frankcohen/ReflectionsOS/Devices/Hoober/Hoober Avinidad Rework rev 2.pdf

July 10, 2022

Hi Ryan,

Here is a rework list for the remaining 4 Hoober Avinadad boards. Would you please make these reworks, then ship the boards to me at:

Frank Cohen
Bellingham Makerspace
1 Bellis
Fair Parkway #618,
Bellingham, WA 98225
Phone: (408) 364-5508

Thank you! -Frank

Rework #1
Hand-made wiring between TFT display module and pads. Pads are the wrong pitch.

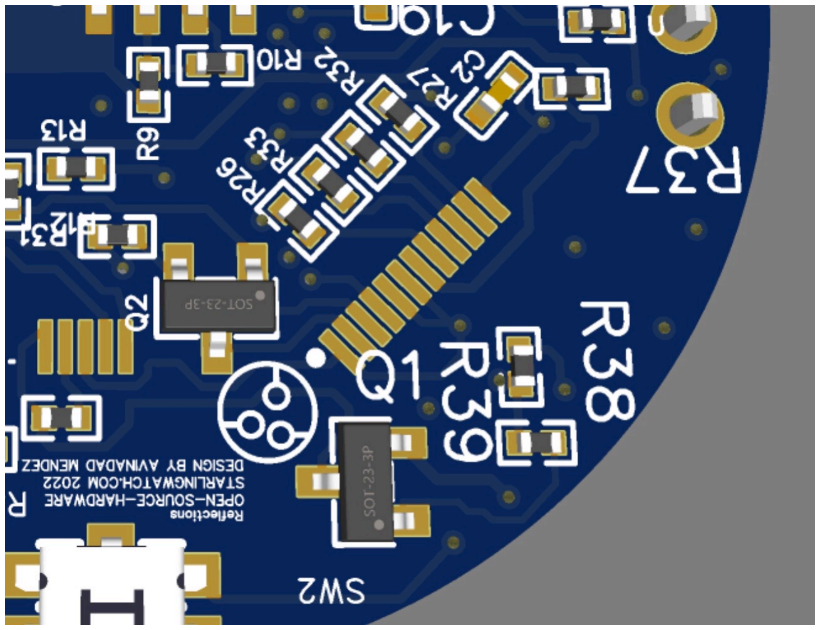
[picture p22: figure]
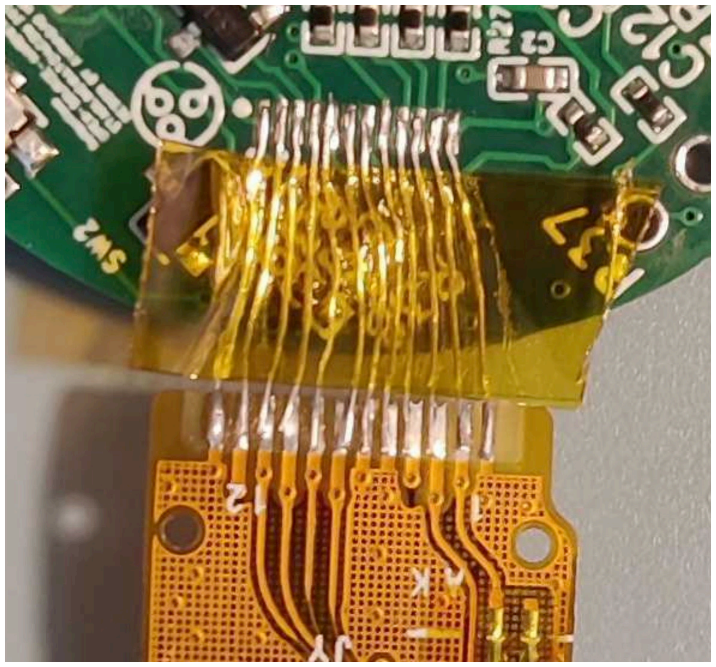
[picture p23: figure]

Make sure the display connector Pin 1 matches Pin 1 on the board.

Remove R26 from the board. There is no need to solder anything there.

Rework #2

Daughterboard welded to Main board using provided cable.

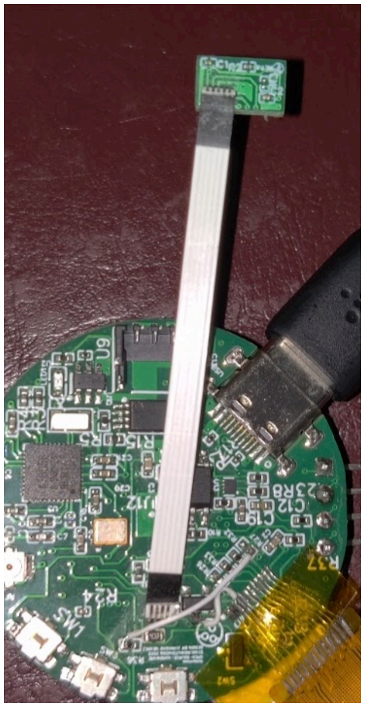
[picture p24: figure]

Rework #3

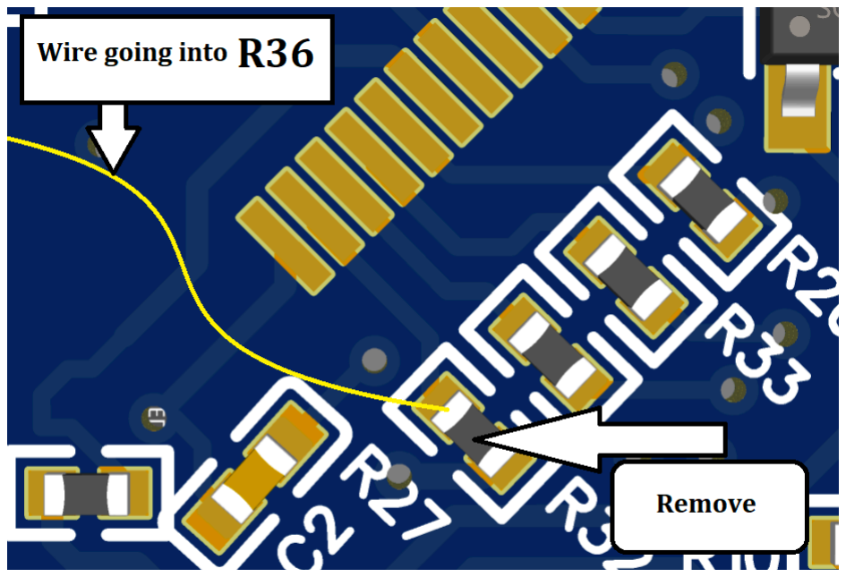
[picture p25: figure]
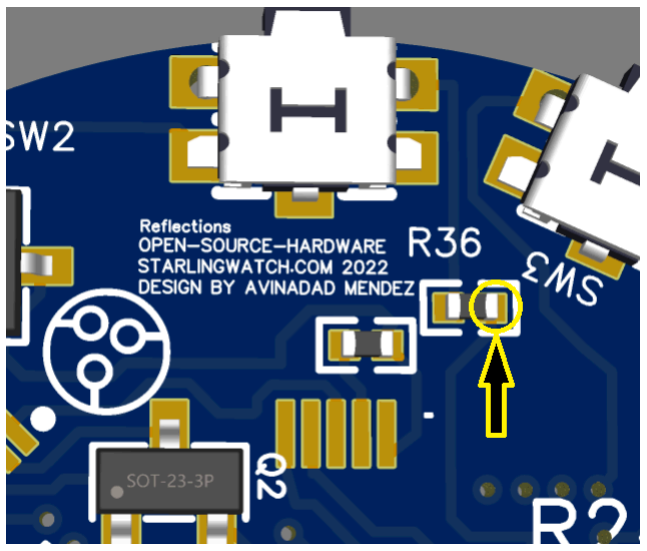
[picture p26: figure]
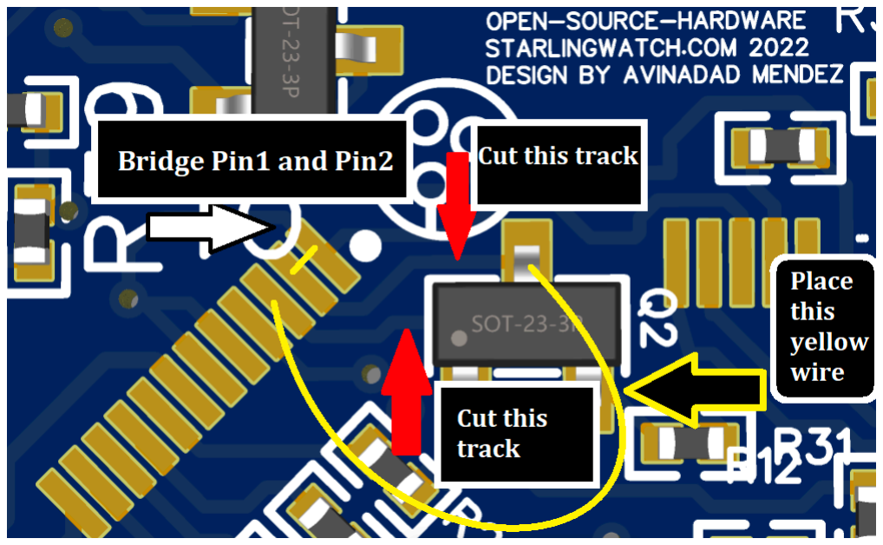
[picture p27: figure]

Rework #4

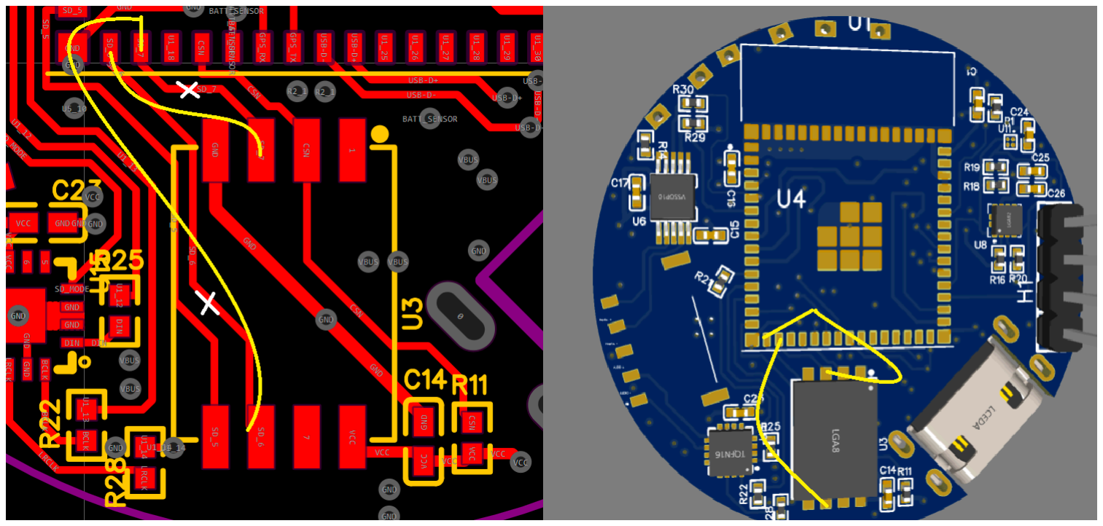
[picture p28: figure]

Cut SD_7 track.
Cut SD_6 track.
Solder SD_6 (ESP32) to SD_7 (NAND).
Solder SD_7 (ESP32) to SD_6 (NAND).
Remove R11
Cut pin 2 of the NAND (U3) from the trace/pad
Connect a wire to pin 2, the wire has a female Dupont connector

Rework #5
This is only for 2 of the remaining 4 boards.

Wire GPIO 8 of the AT6558R (U5) to Ground

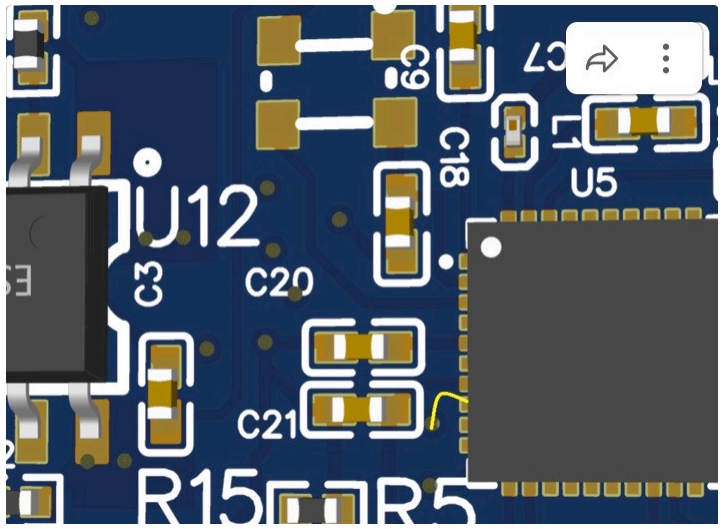
[picture p29: figure]
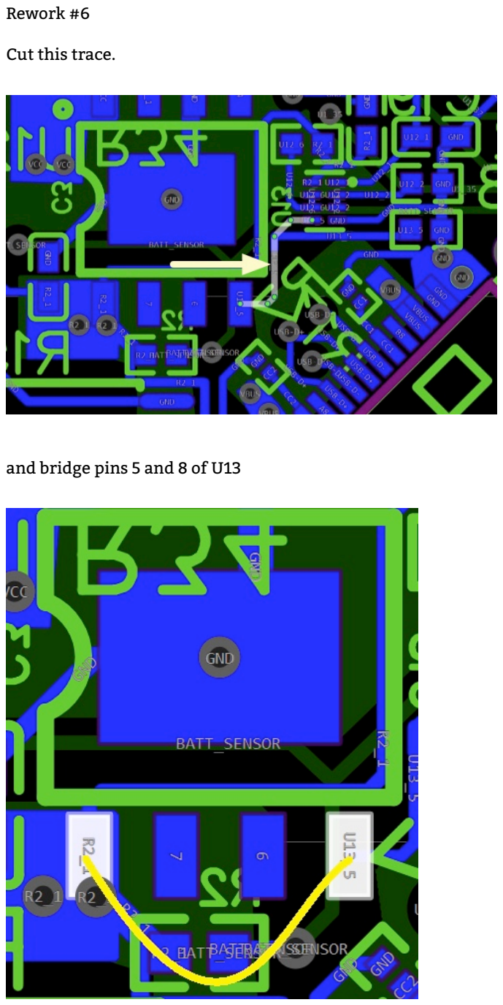
[picture p30: page 6]

Rework #6

Cut this trace.

and bridge pins 5 and 8 of U13
