frankcohen/ReflectionsOS/Devices/Hoober/Gesture Sensor Daughter Board.pdf

# Gesture Sensor Board

# VL53L5CX Sensor daughter board with FFC 4 wire cable

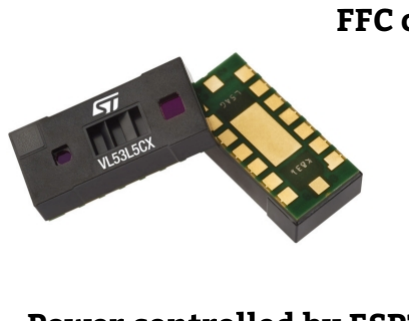
[picture p31: figure]

FFC connector welded to daughter board, adds FFC connector to main board

VL53L5CX

Power controlled by ESP32 GPIO pin

FFC 4 wire cable welded to the daughter board bottom Board is: 8mm x 4.67 mm, 1.57 mm
Sensor is: 6.4 mm x 3 mm x 1.5 mm
FFC wire: 5 mm x 20 mm x .24 mm
SMT mounted sensor pointing upwards

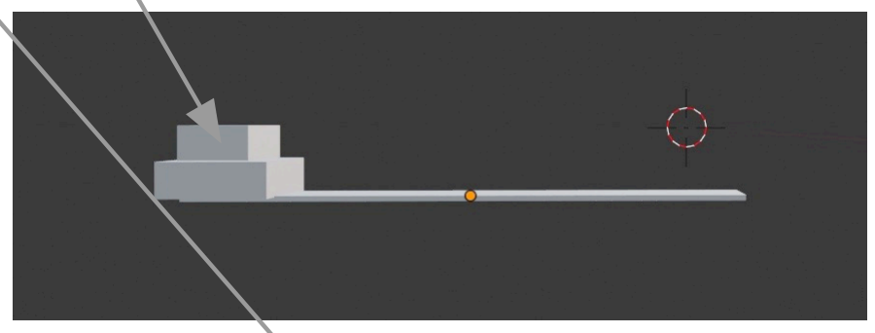
[picture p32: figure]
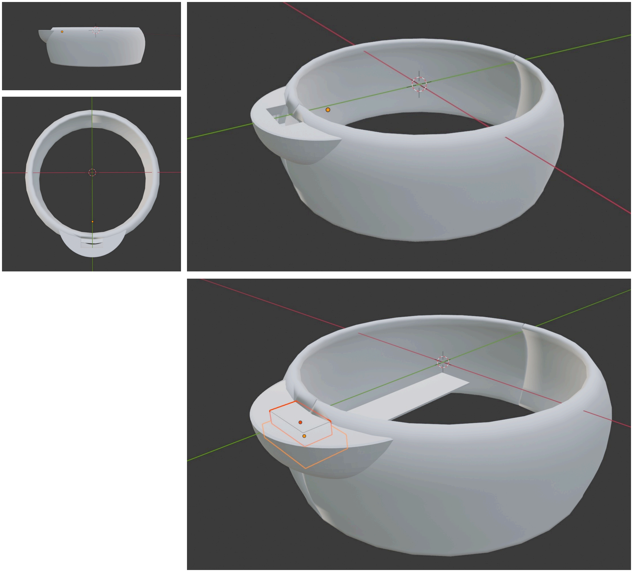
[picture p33: figure]
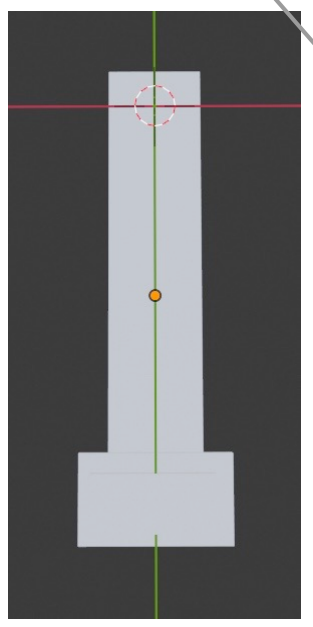
[picture p34: figure]
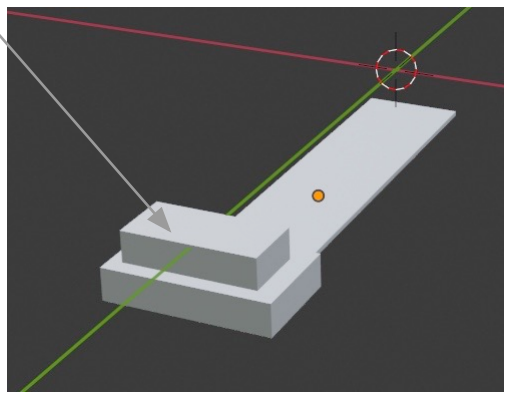
[picture p35: figure]
