frankcohen/ReflectionsOS/Devices/VladPlus/layouts/BoardOutLine.pdf

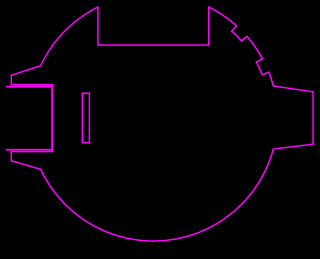
[picture p49: figure]
