frankcohen/ReflectionsOS/Devices/BlueFish/Datasheets/adafruit_products_FESP3_sch.png

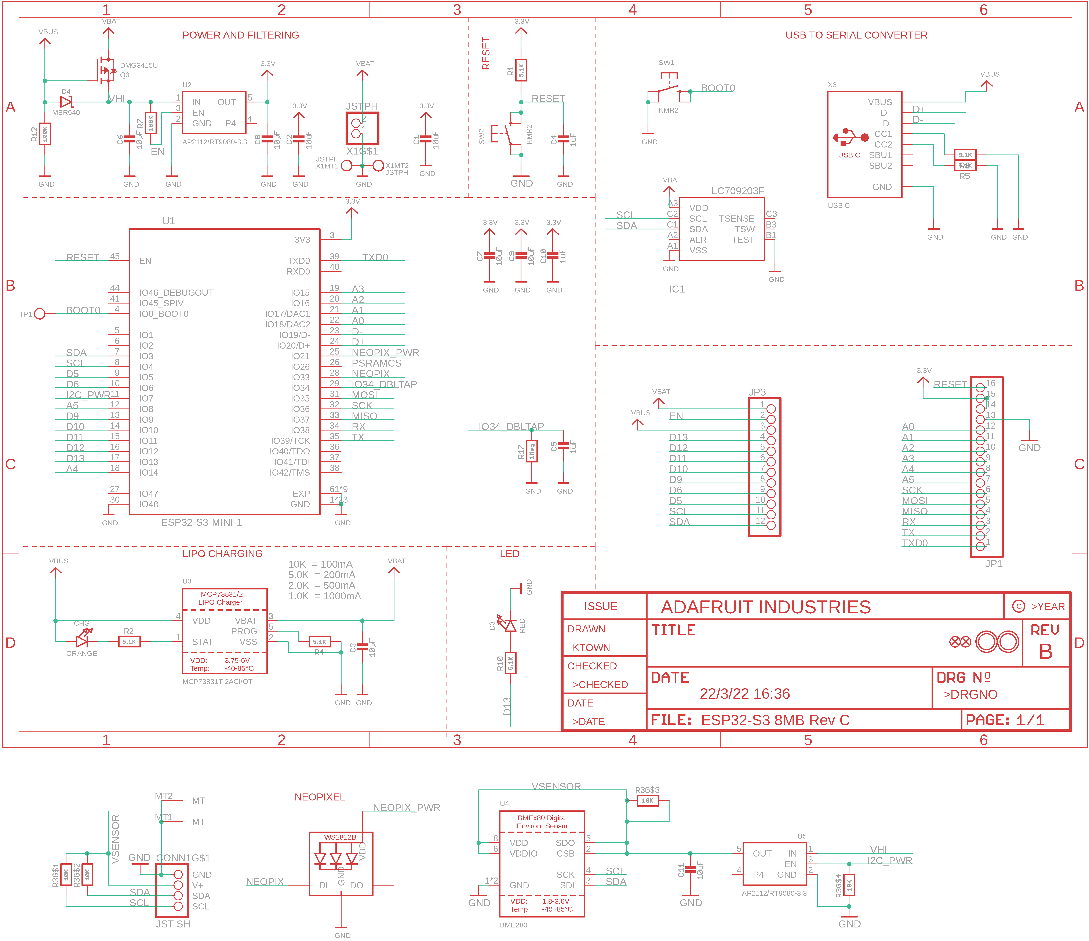
Devices/BlueFish/Datasheets/adafruit_products_FESP3_sch.png
