frankcohen/ReflectionsOS/Devices/CindyLou/CindyLou_daughter_board_stiffener.jpg

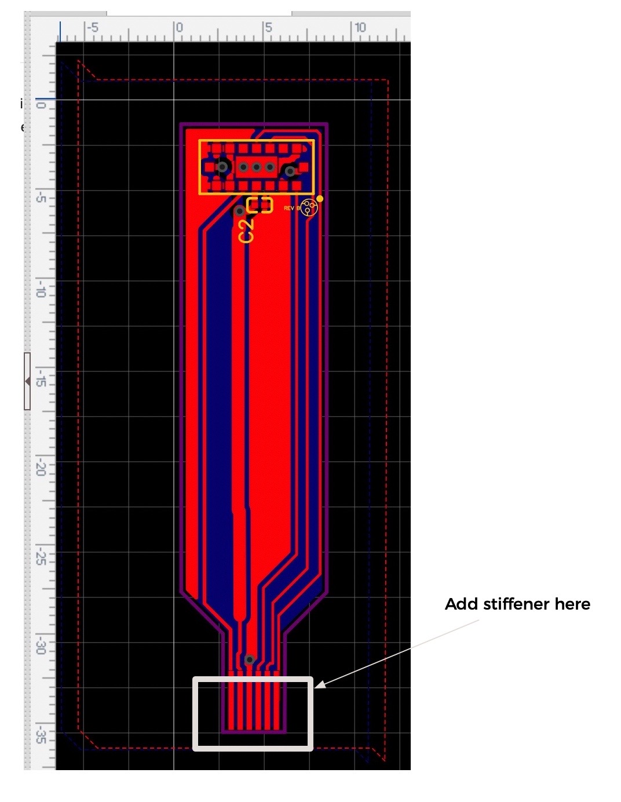
Devices/CindyLou/CindyLou_daughter_board_stiffener.jpg
