frankcohen/ReflectionsOS/Devices/CindyLou/Details daughter board.jpg

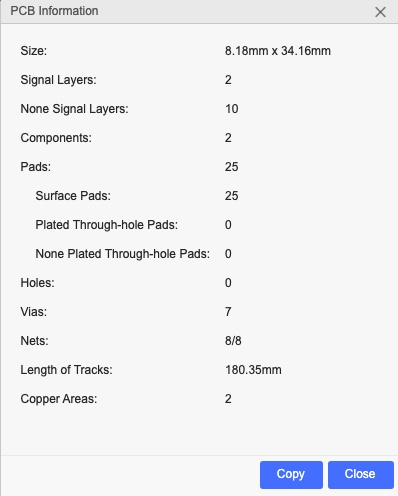
Devices/CindyLou/Details daughter board.jpg
