frankcohen/ReflectionsOS/Devices/CindyLou/Details main board.jpg

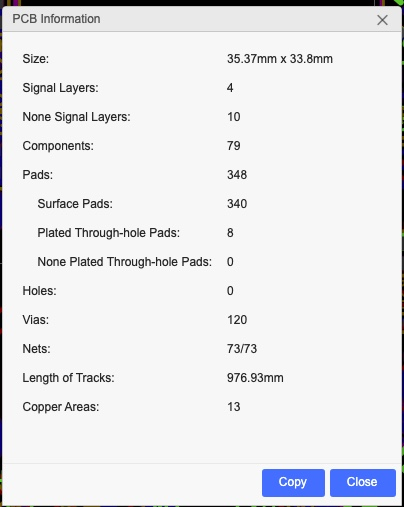
Devices/CindyLou/Details main board.jpg
