frankcohen/ReflectionsOS/Devices/CindyLou/PCBway photos/61b101b553f684890c5e4af1a7ff25e.jpeg

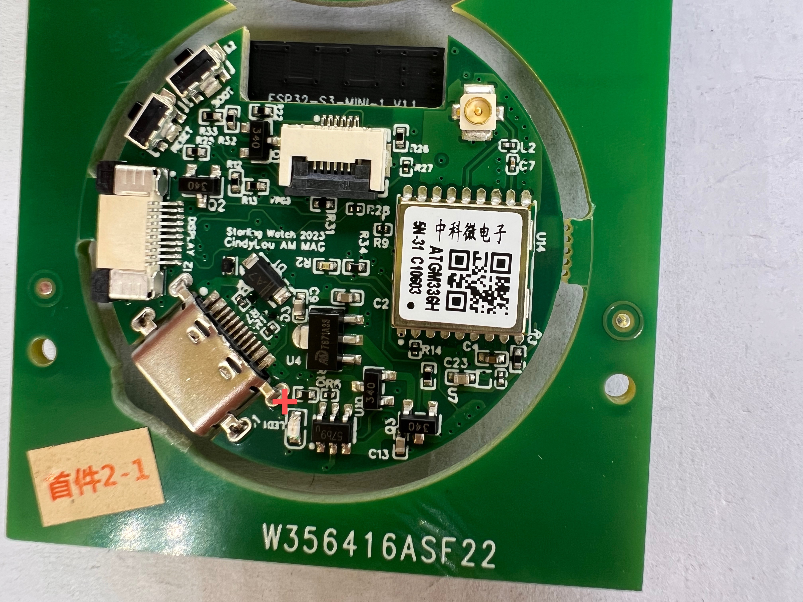
Devices/CindyLou/PCBway photos/61b101b553f684890c5e4af1a7ff25e.jpeg
