frankcohen/ReflectionsOS/Devices/Hoober/Photos/IMG_20220601_134554.jpg

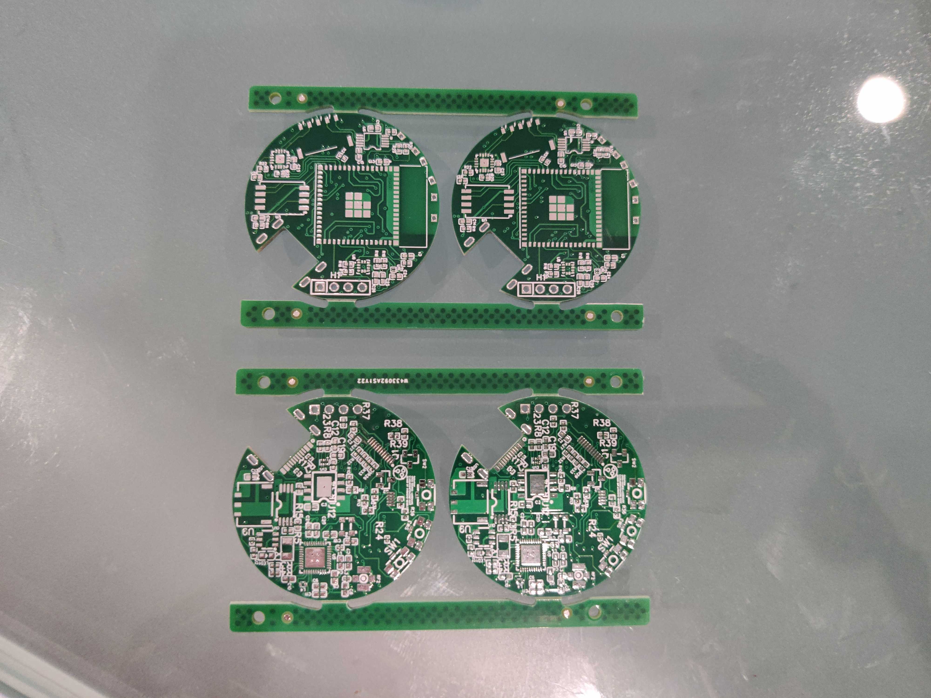
Devices/Hoober/Photos/IMG_20220601_134554.jpg
