frankcohen/ReflectionsOS/Devices/Hoober/Photos/IMG_20220627_172540.jpg

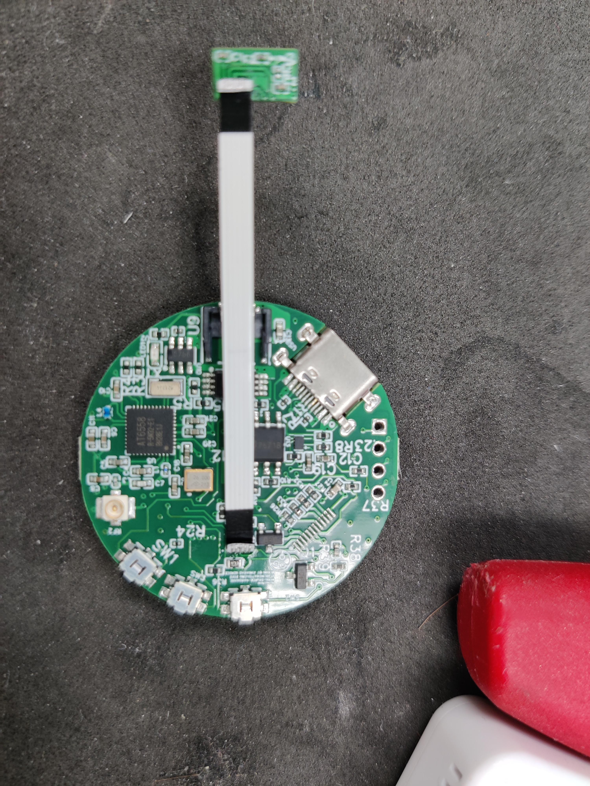
Devices/Hoober/Photos/IMG_20220627_172540.jpg
