frankcohen/ReflectionsOS/Devices/Hoober/Photos/IMG_20220627_172551.jpg

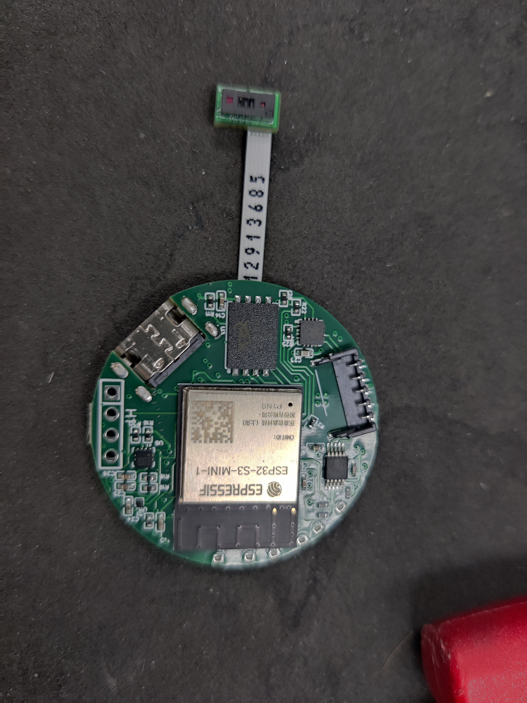
Devices/Hoober/Photos/IMG_20220627_172551.jpg
