frankcohen/ReflectionsOS/Devices/Hoober/Photos/IMG_20220627_183308.jpg

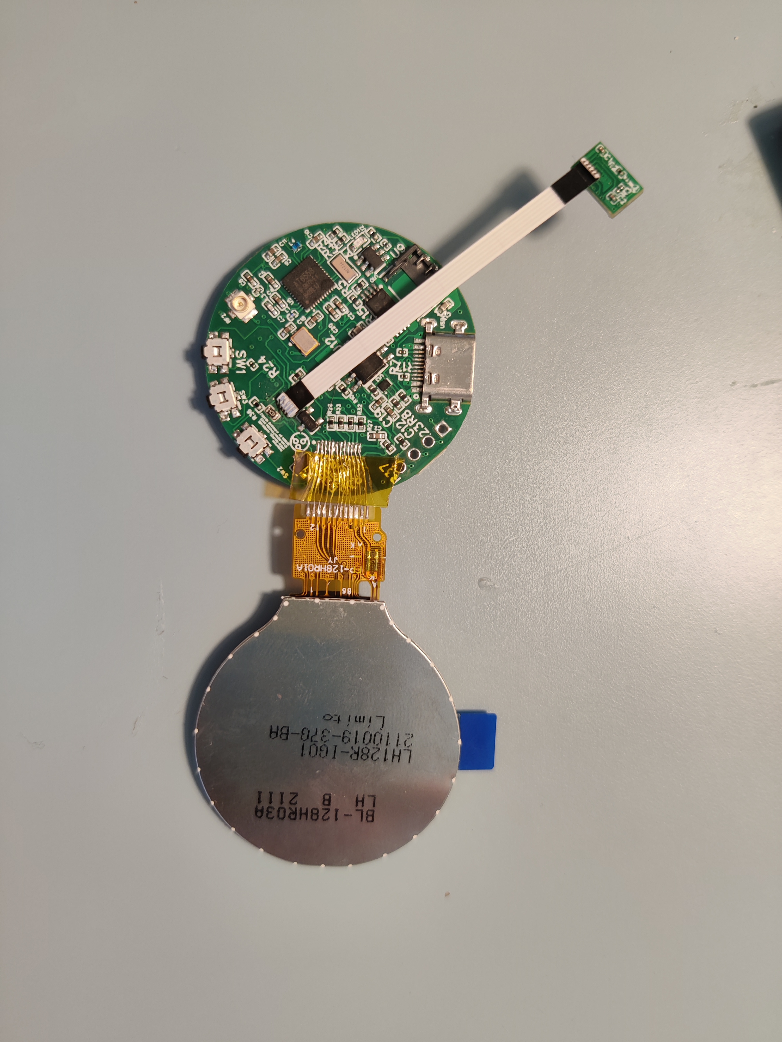
Devices/Hoober/Photos/IMG_20220627_183308.jpg
