frankcohen/ReflectionsOS/Devices/Hoober/Photos/IMG_20220627_183316.jpg

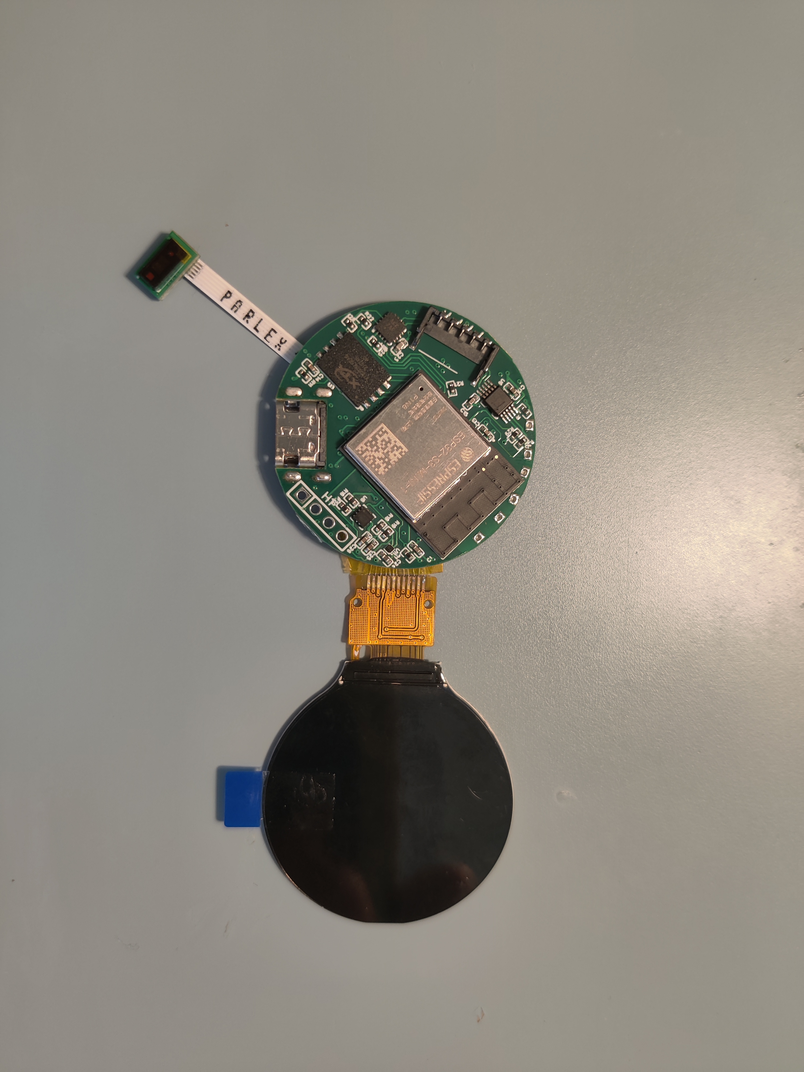
Devices/Hoober/Photos/IMG_20220627_183316.jpg
