frankcohen/ReflectionsOS/Devices/Hoober/Photos/IMG_20220707_080942.jpg

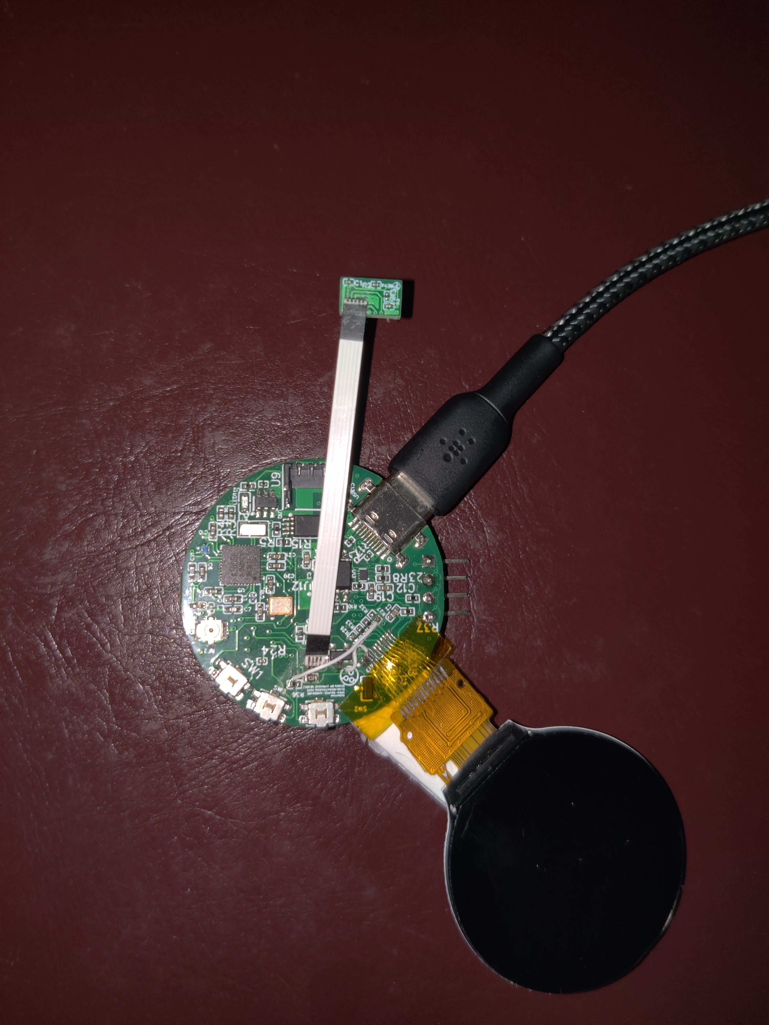
Devices/Hoober/Photos/IMG_20220707_080942.jpg
