frankcohen/ReflectionsOS/Devices/Hoober/Photos/IMG_20220710_211812.jpg

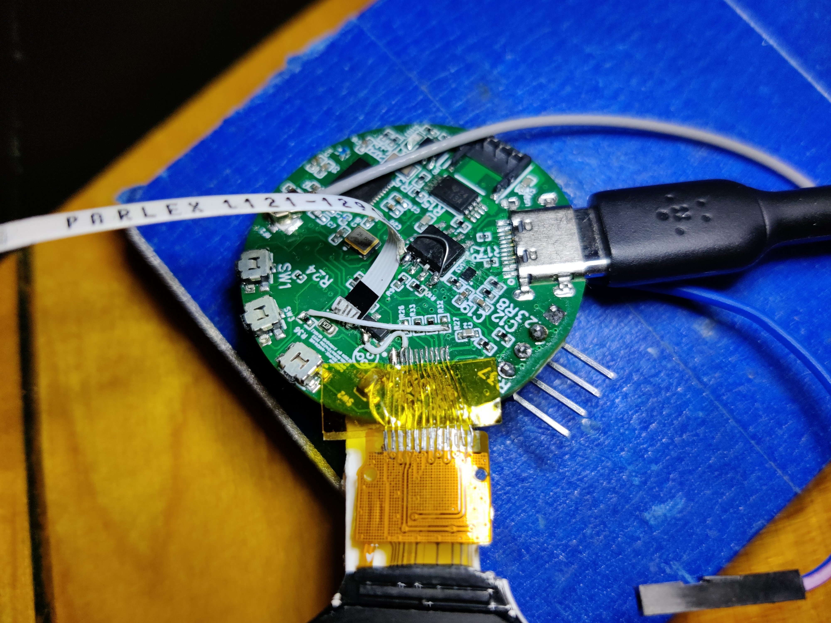
Devices/Hoober/Photos/IMG_20220710_211812.jpg
