frankcohen/ReflectionsOS/Devices/Hoober/Photos/screenshot_7177.jpg

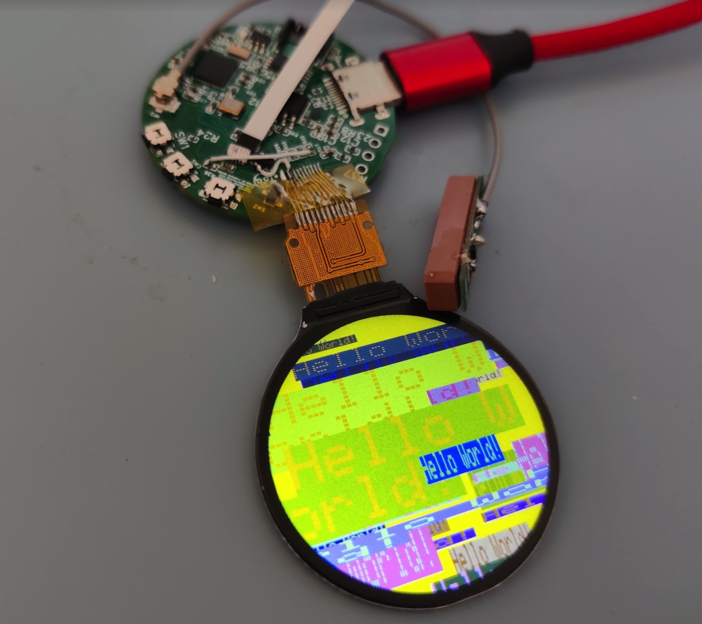
Devices/Hoober/Photos/screenshot_7177.jpg
