frankcohen/ReflectionsOS/Devices/Horton/Datasheets/Belinda FPC adaptor 3f5895c3af74f1fa5b2311e33c003cb9.jpg

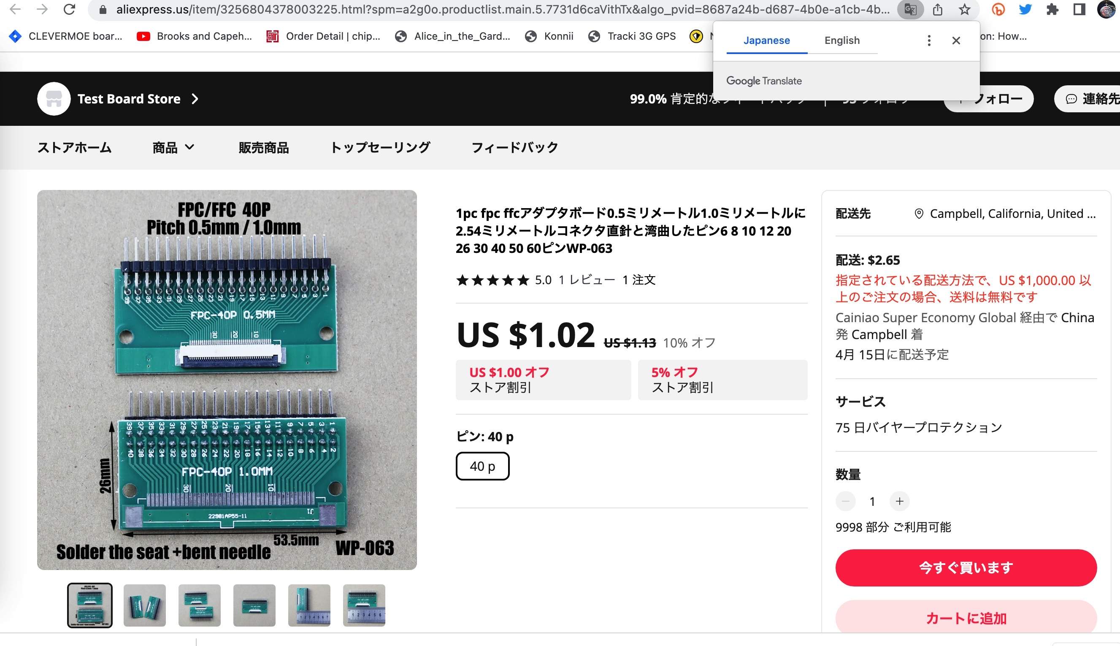
Devices/Horton/Datasheets/Belinda FPC adaptor 3f5895c3af74f1fa5b2311e33c003cb9.jpg
