frankcohen/ReflectionsOS/Devices/Knox/Breadboard Photos/IMG_20220116_211522.jpg

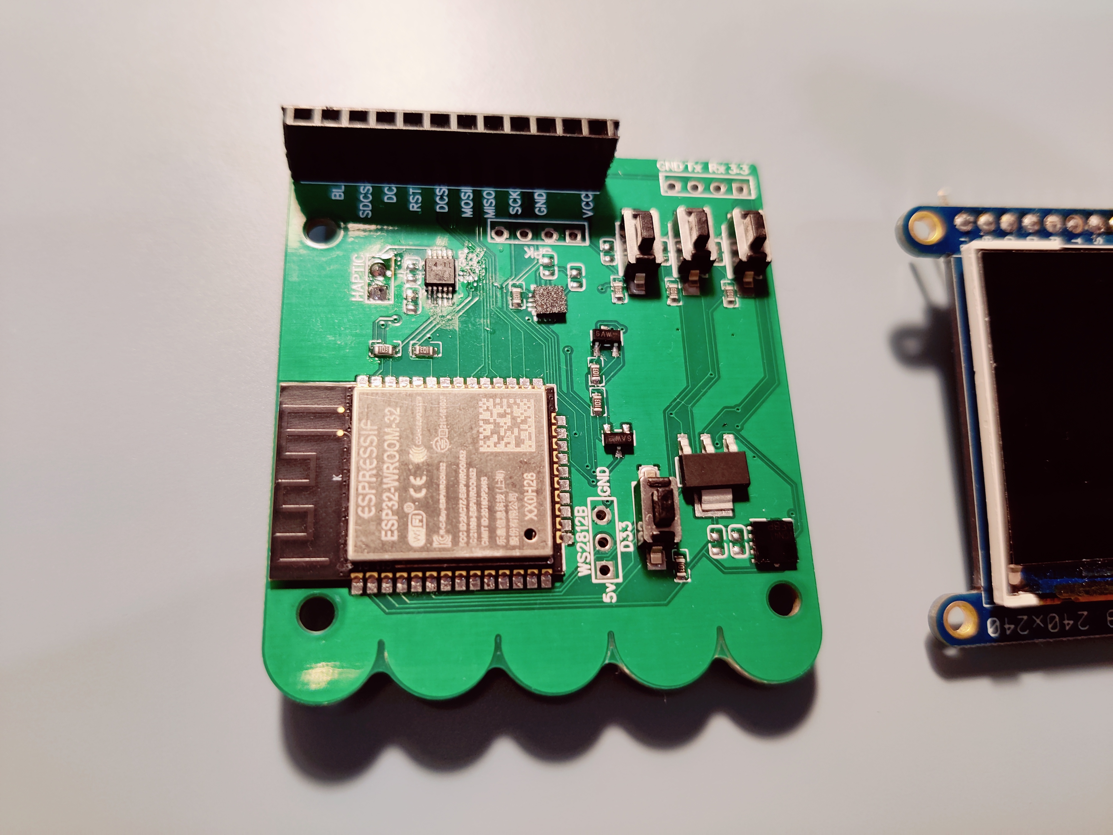
Devices/Knox/Breadboard Photos/IMG_20220116_211522.jpg
