frankcohen/ReflectionsOS/Devices/Knox/Breadboard Photos/IMG_20220116_211529.jpg

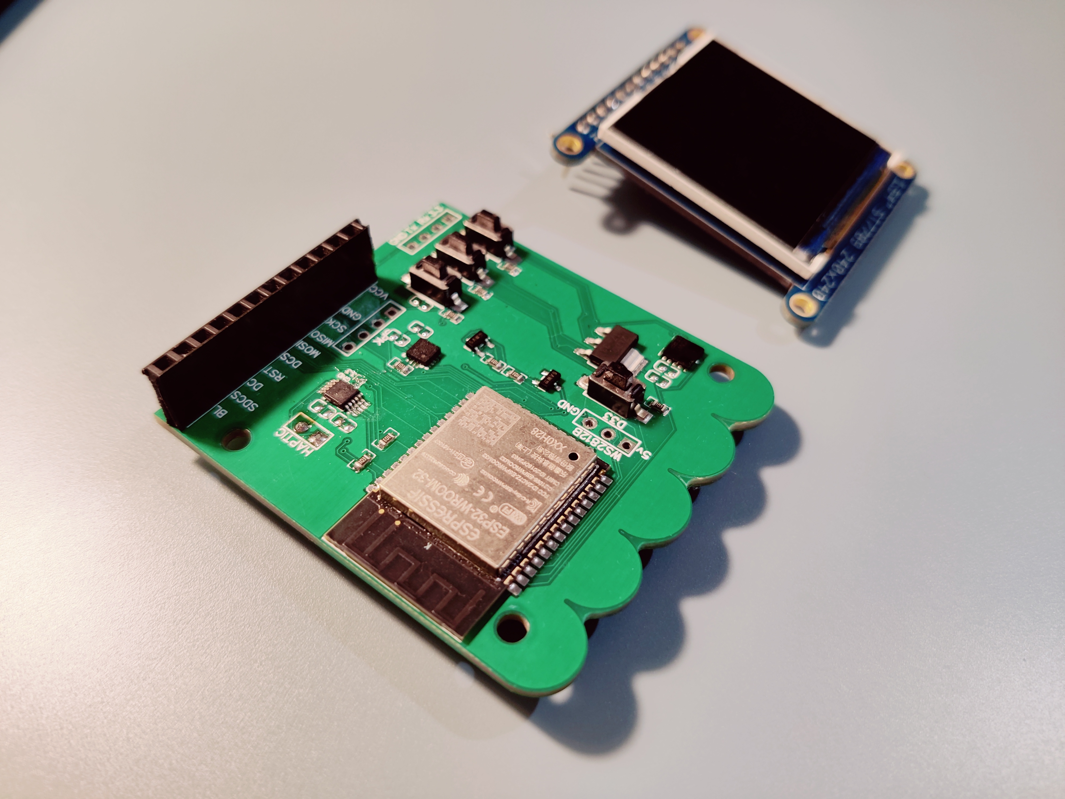
Devices/Knox/Breadboard Photos/IMG_20220116_211529.jpg
