frankcohen/ReflectionsOS/Devices/Knox/Breadboard Photos/IMG_20220116_211533.jpg

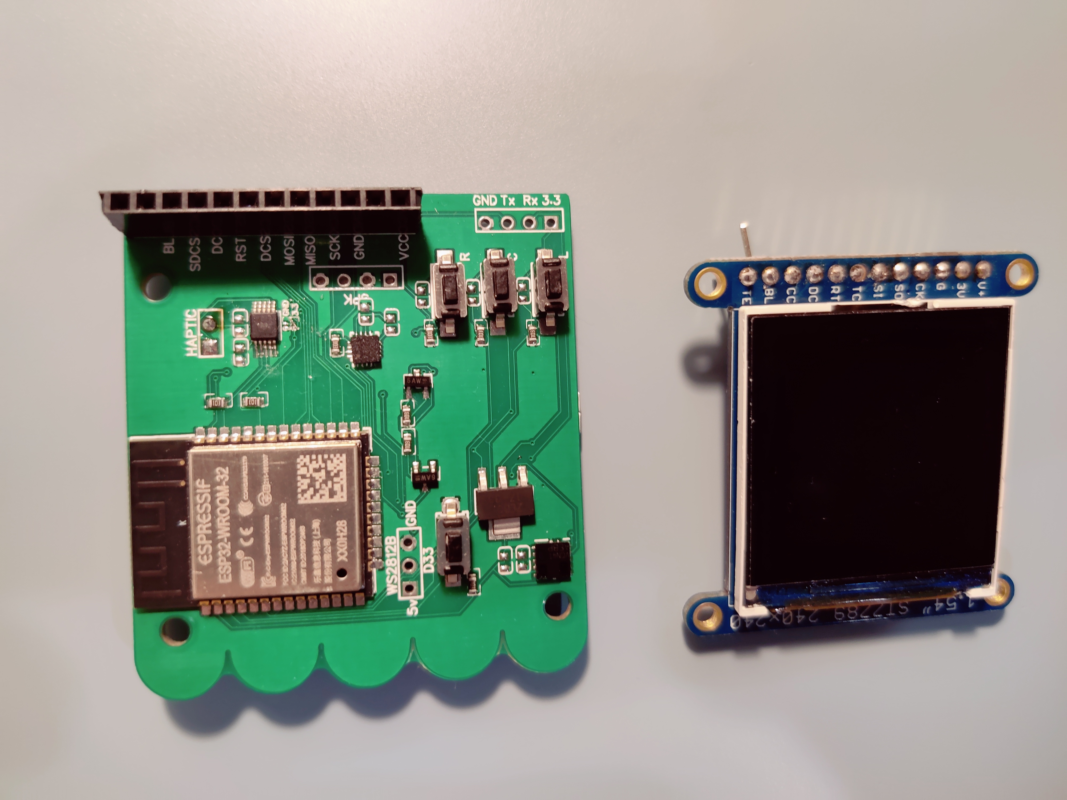
Devices/Knox/Breadboard Photos/IMG_20220116_211533.jpg
