frankcohen/ReflectionsOS/Devices/RedFish/T-F39W356416A/Check whether the orientation is correct.png

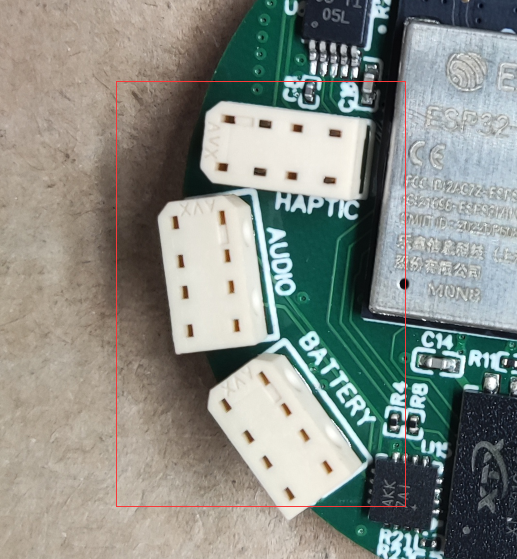
Devices/RedFish/T-F39W356416A/Check whether the orientation is correct.png
