frankcohen/ReflectionsOS/Devices/RedFish/T-F39W356416A/D3ĢŽD4 Check whether the orientation is correct.png

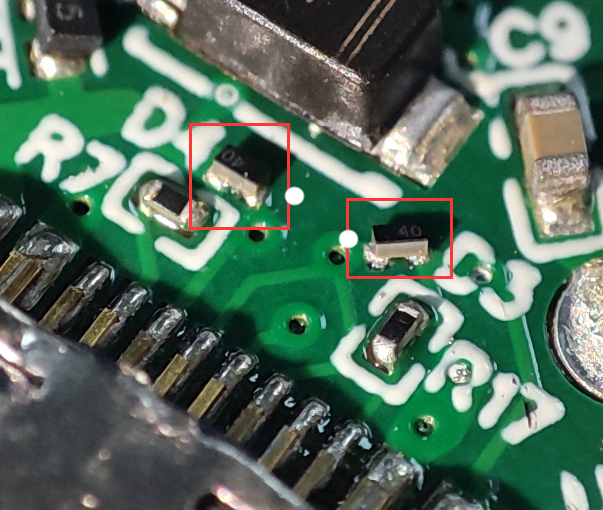
Devices/RedFish/T-F39W356416A/D3ĢŽD4 Check whether the orientation is correct.png
