frankcohen/ReflectionsOS/Devices/RedFish/T-F39W356416A/T-F39W356416A-QQ截图20230922172746.png

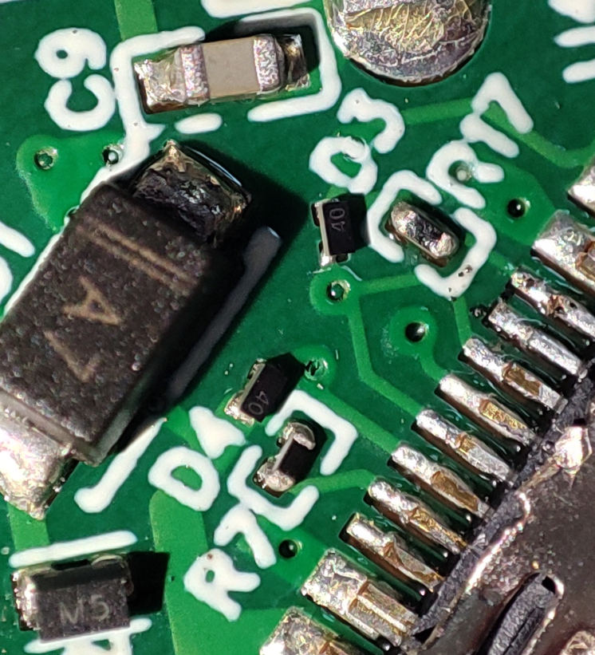
Devices/RedFish/T-F39W356416A/T-F39W356416A-QQ截图20230922172746.png
