frankcohen/ReflectionsOS/Devices/Sox/Breadboard Photos/Soxv1Breadboard/IMG_20220116_210145.jpg

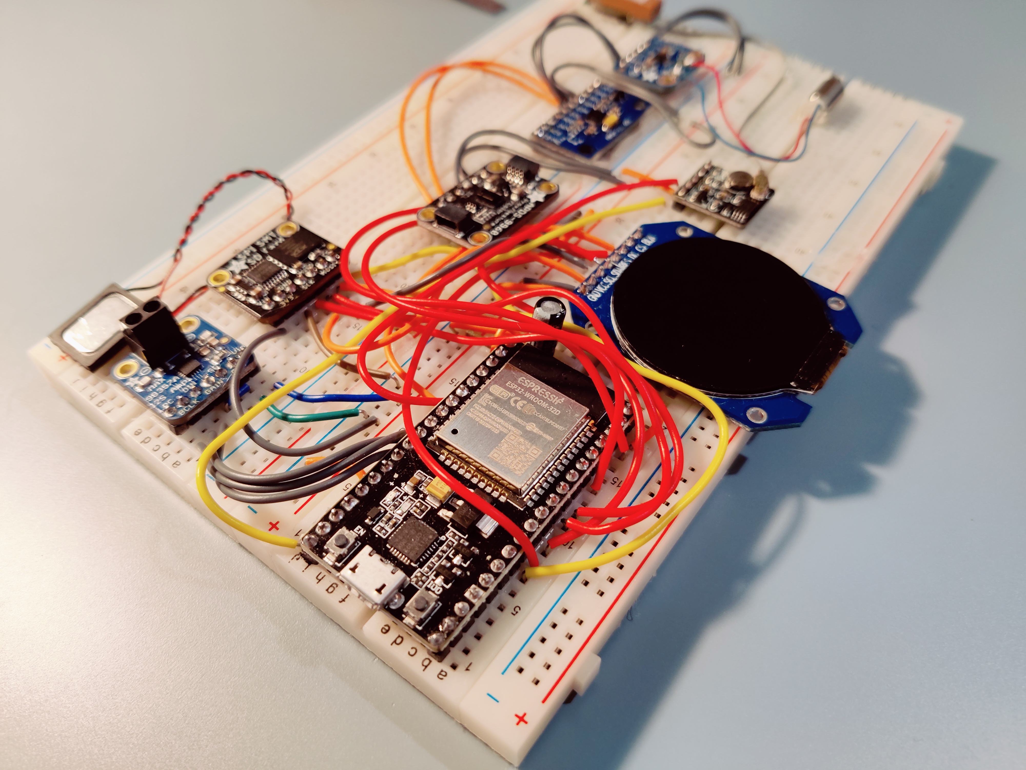
Devices/Sox/Breadboard Photos/Soxv1Breadboard/IMG_20220116_210145.jpg
