frankcohen/ReflectionsOS/Devices/Sox/Breadboard Photos/Soxv1Breadboard/IMG_20220116_210226.jpg

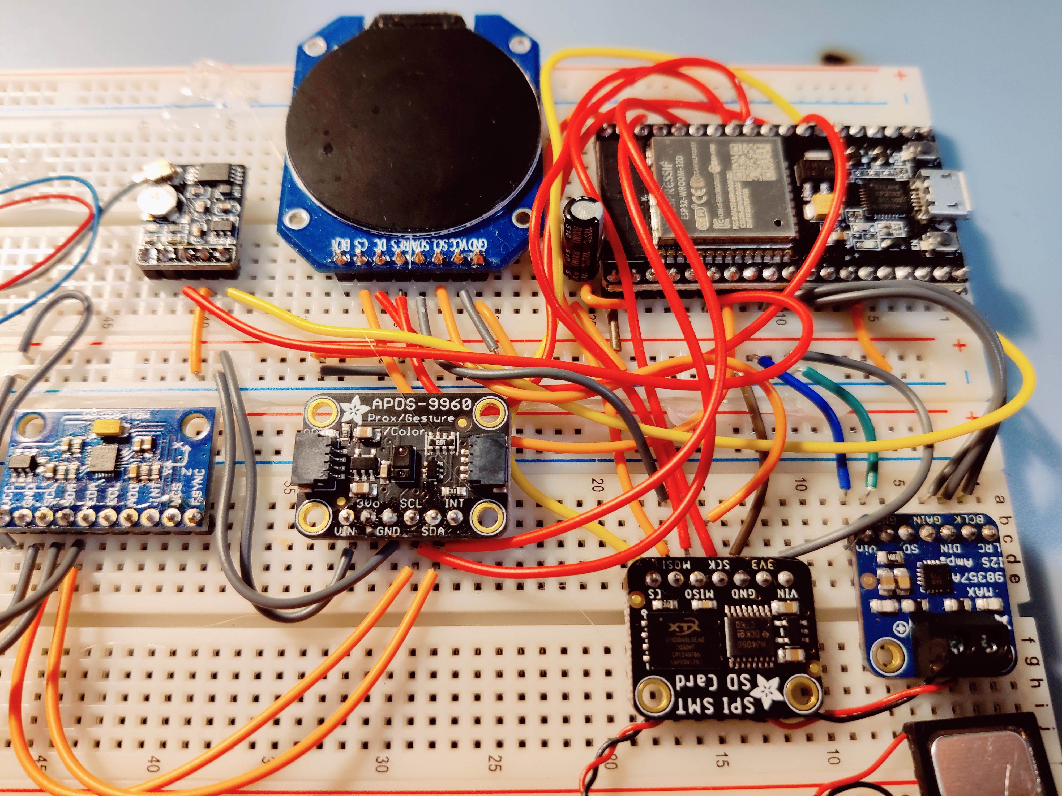
Devices/Sox/Breadboard Photos/Soxv1Breadboard/IMG_20220116_210226.jpg
