frankcohen/ReflectionsOS/Devices/Sox/Breadboard Photos/Soxv2Breadboard/IMG_20220124_091618.jpg

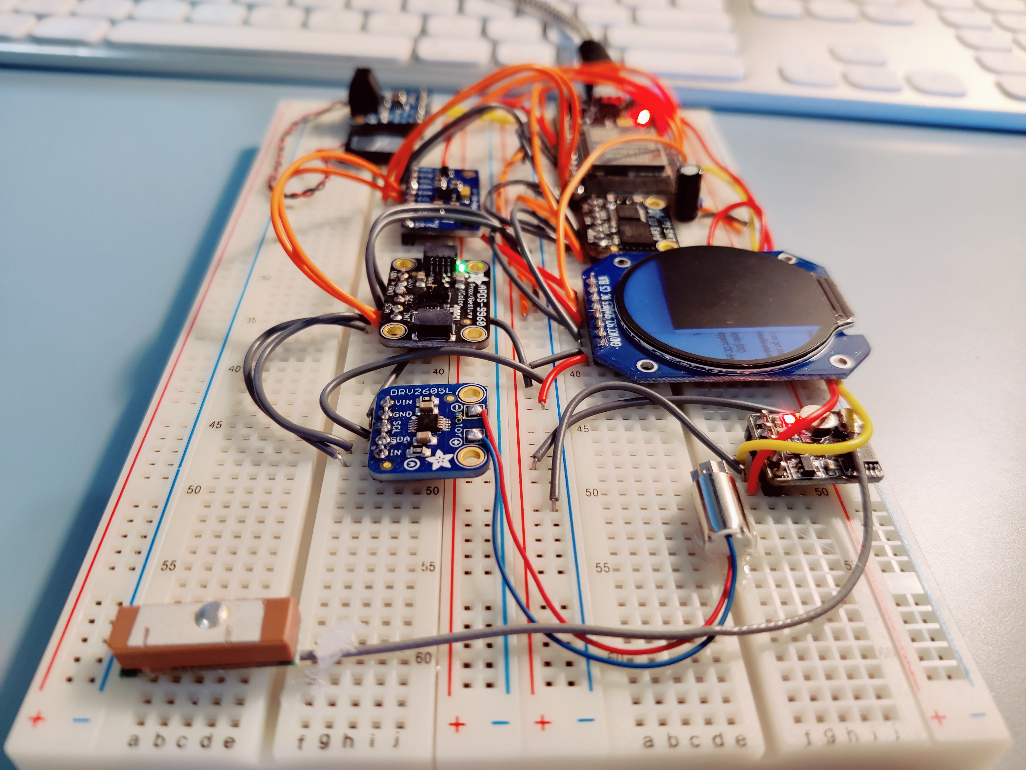
Devices/Sox/Breadboard Photos/Soxv2Breadboard/IMG_20220124_091618.jpg
