frankcohen/ReflectionsOS/Devices/Sox/Data Sheets/Haptic controller.jpeg

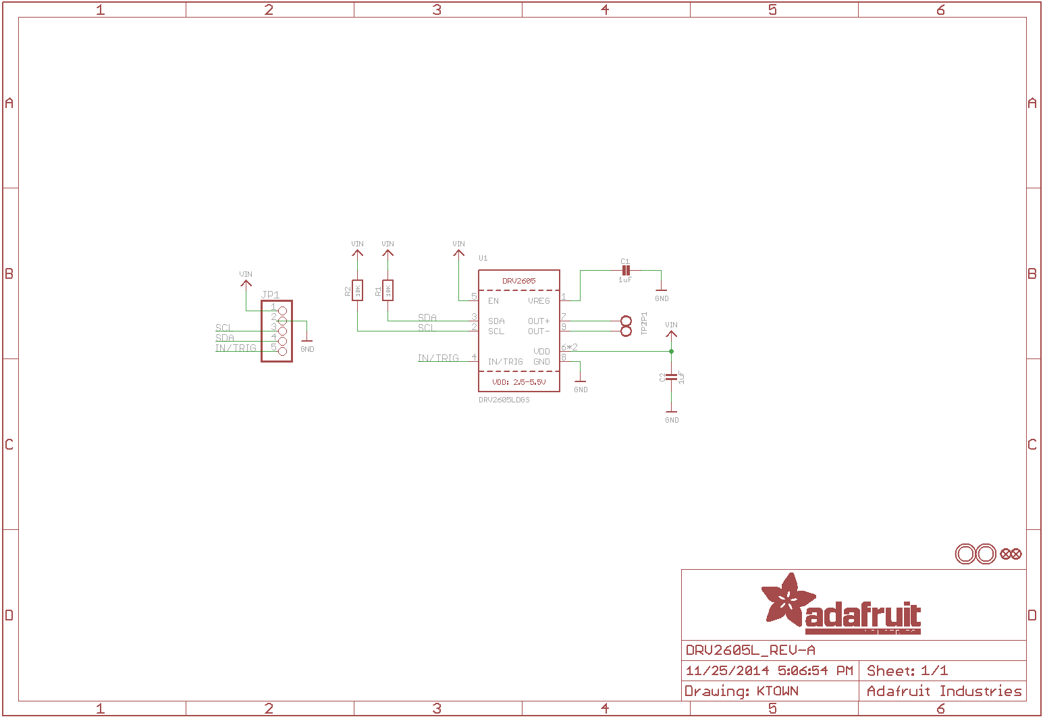
Devices/Sox/Data Sheets/Haptic controller.jpeg
