frankcohen/ReflectionsOS/Devices/Sox/Schematic/PCBway/Gerber_PCB_Sox Board Avinadad_2/阻抗线.png

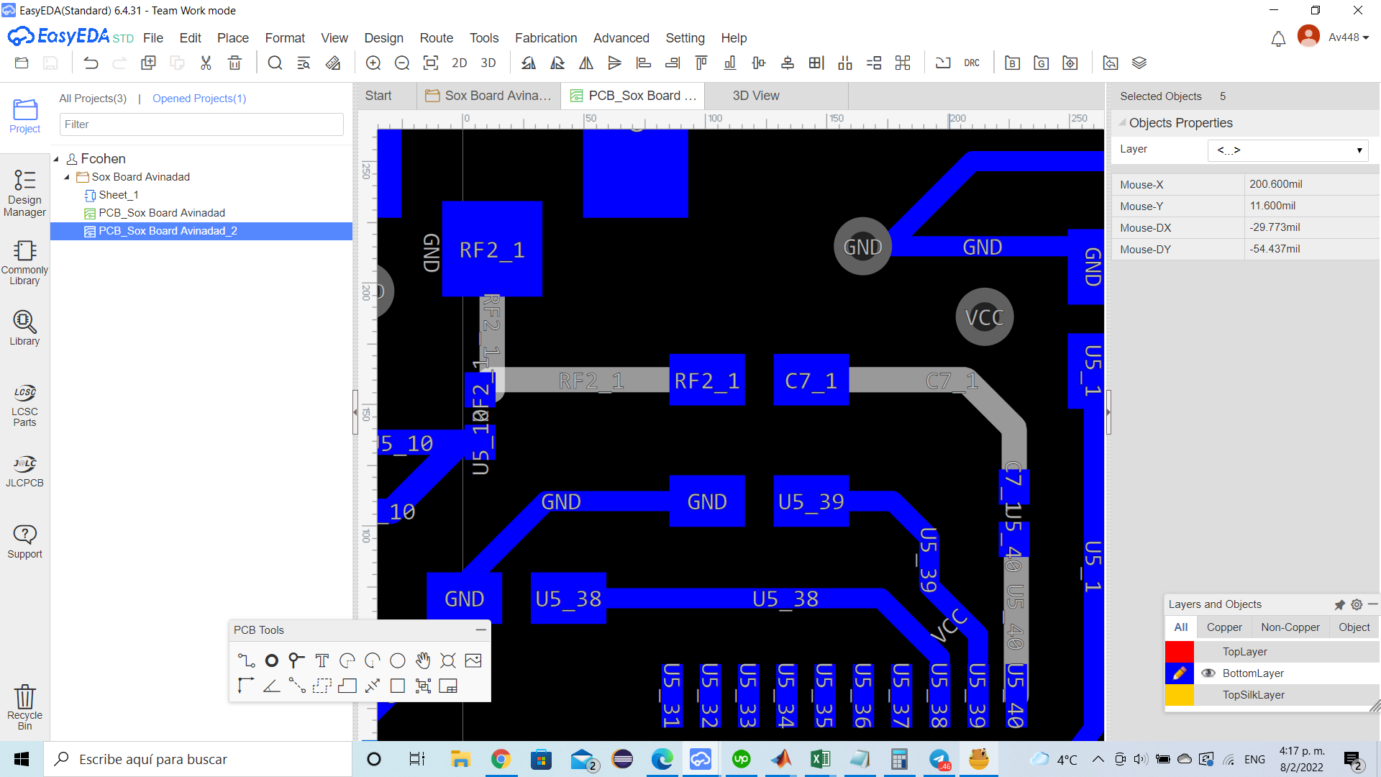
Devices/Sox/Schematic/PCBway/Gerber_PCB_Sox Board Avinadad_2/阻抗线.png
