frankcohen/ReflectionsOS/Devices/Vlad/XRays it is a board/1.jpg

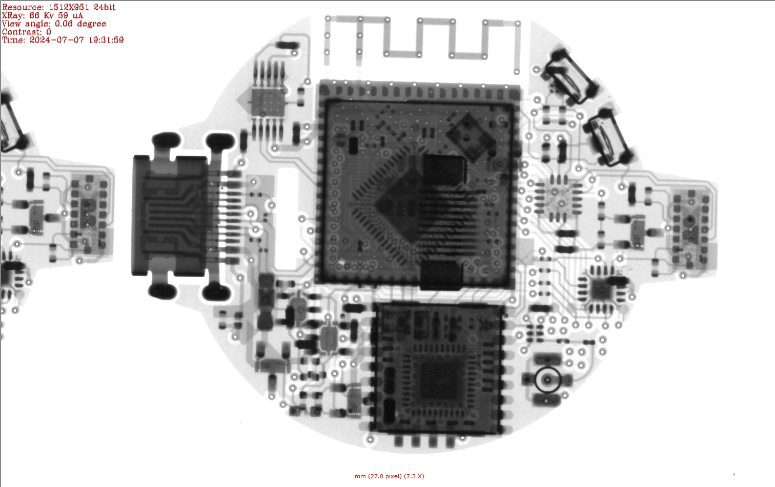
Devices/Vlad/XRays it is a board/1.jpg
