frankcohen/ReflectionsOS/Devices/Vlad/XRays it is a board/2.jpg

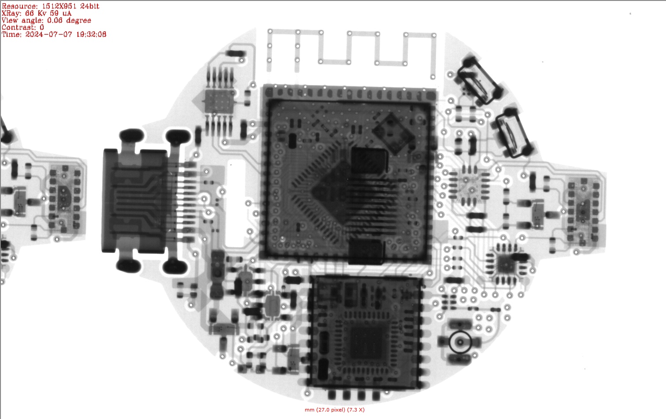
Devices/Vlad/XRays it is a board/2.jpg
