frankcohen/ReflectionsOS/Devices/Vlad/XRays it is a board/3.jpg

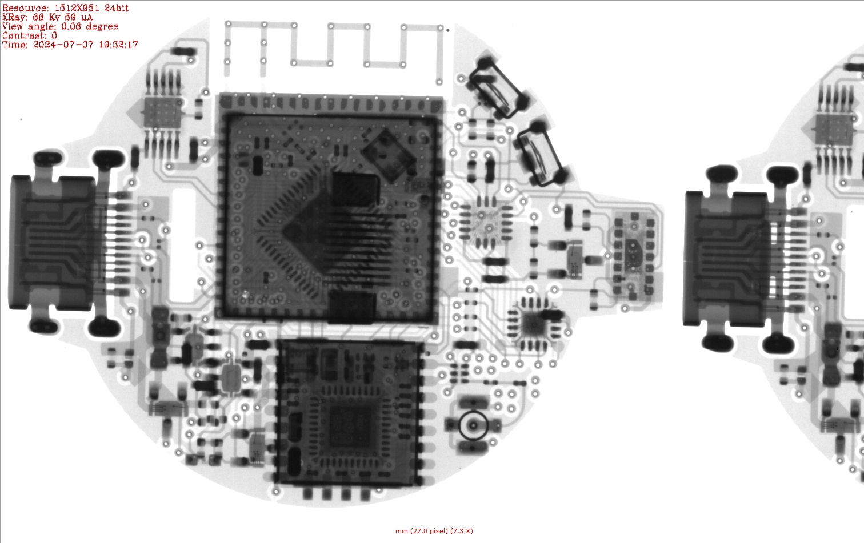
Devices/Vlad/XRays it is a board/3.jpg
