frankcohen/ReflectionsOS/Devices/Vlad/XRays it is a board/4.jpg

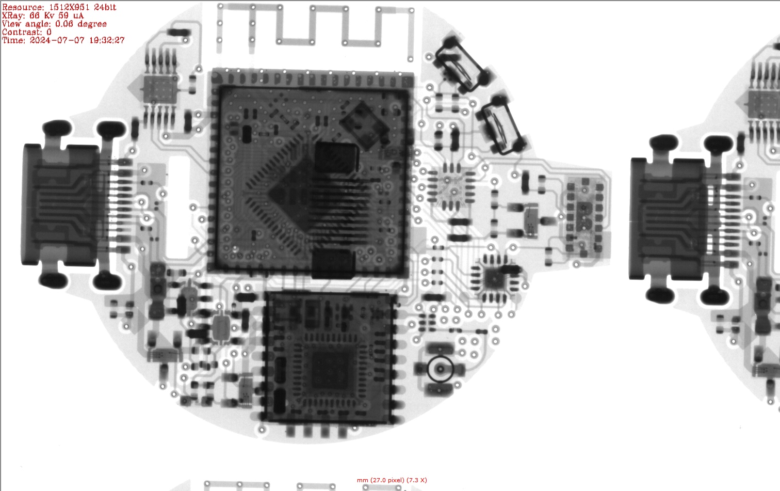
Devices/Vlad/XRays it is a board/4.jpg
