frankcohen/ReflectionsOS/Devices/Vlad/XRays it is a board/5.jpg

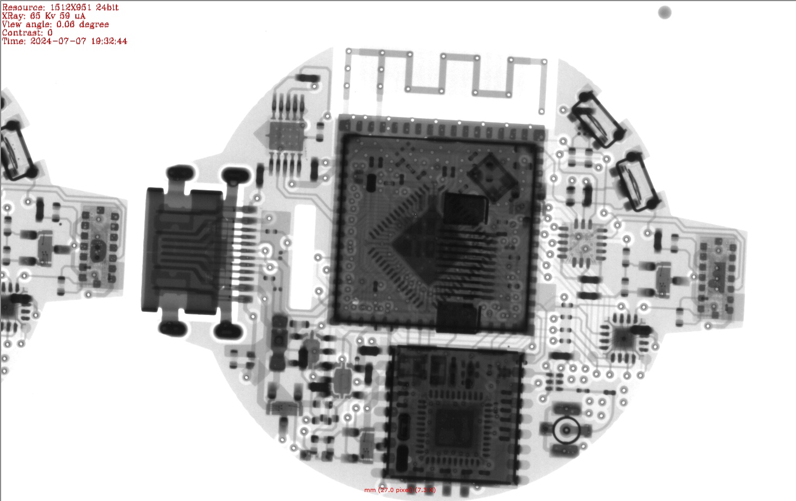
Devices/Vlad/XRays it is a board/5.jpg
