frankcohen/ReflectionsOS/Devices/Vlad/XRays it is a board/7.jpg

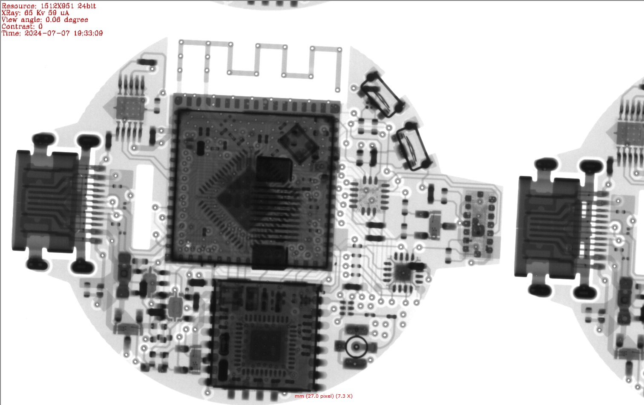
Devices/Vlad/XRays it is a board/7.jpg
