frankcohen/ReflectionsOS/Devices/Vlad/XRays it is a board/8.jpg

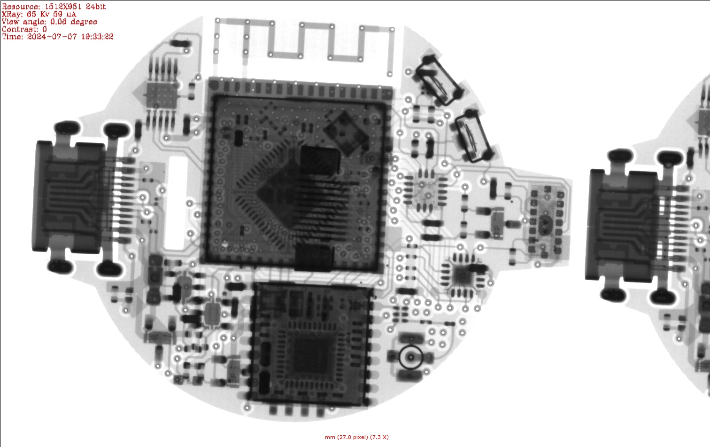
Devices/Vlad/XRays it is a board/8.jpg
