frankcohen/ReflectionsOS/Devices/VladPlus/Schematic_Vladplus_2024-10-29.png

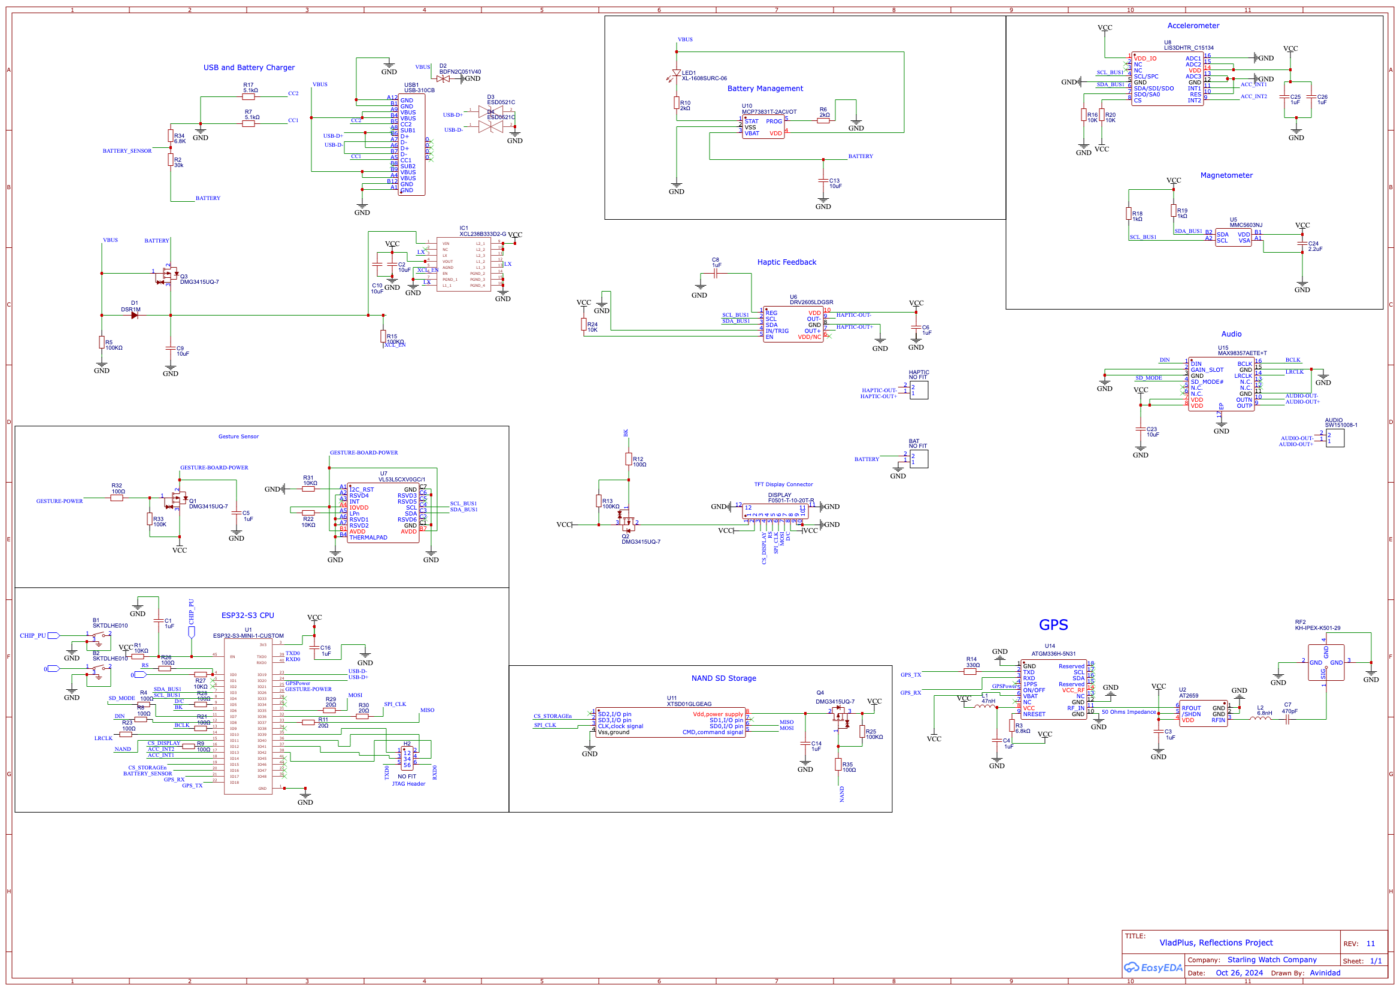
Devices/VladPlus/Schematic_Vladplus_2024-10-29.png
