frankcohen/ReflectionsOS/Docs/images/Cat In Hat.jpg

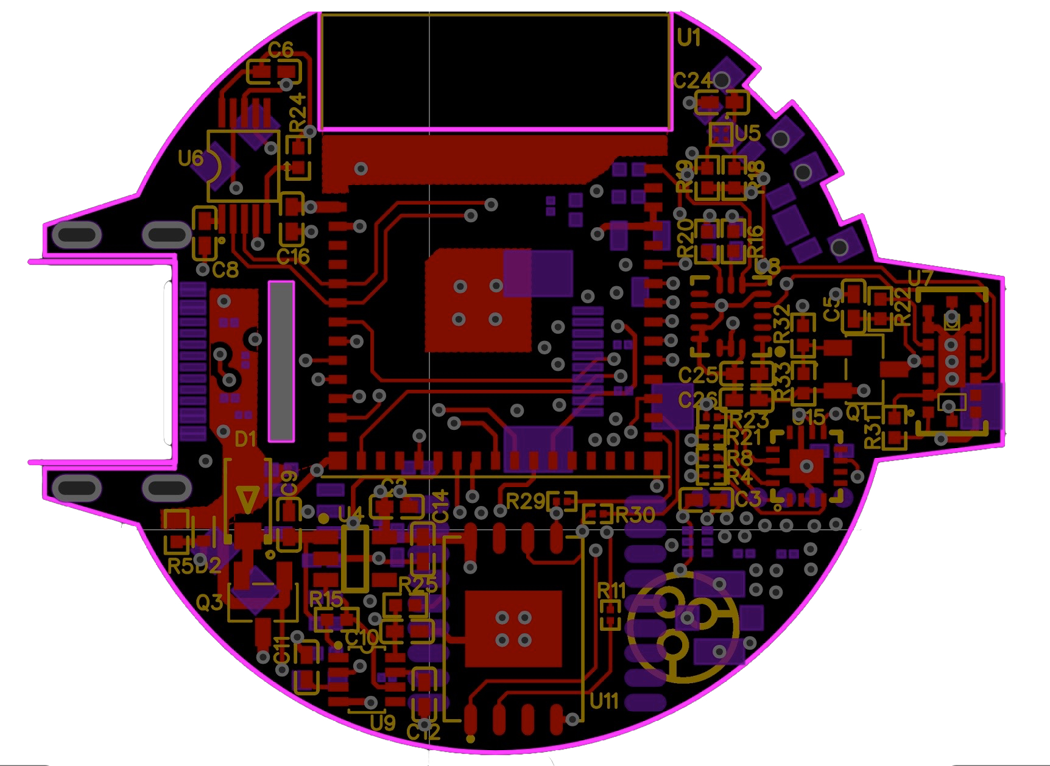
Docs/images/Cat In Hat.jpg
