frankcohen/ReflectionsOS/Docs/images/Intro title card.jpg

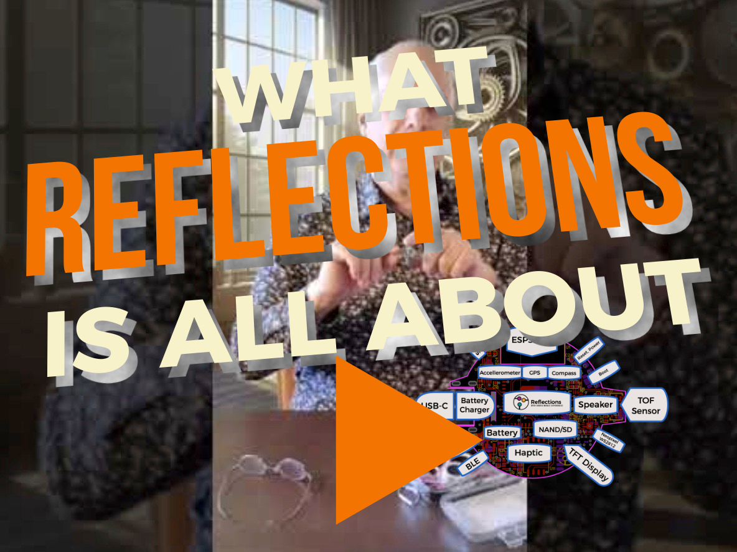
Docs/images/Intro title card.jpg
