frankcohen/ReflectionsOS/Docs/images/Reddit_USB_Frustratiing.jpg

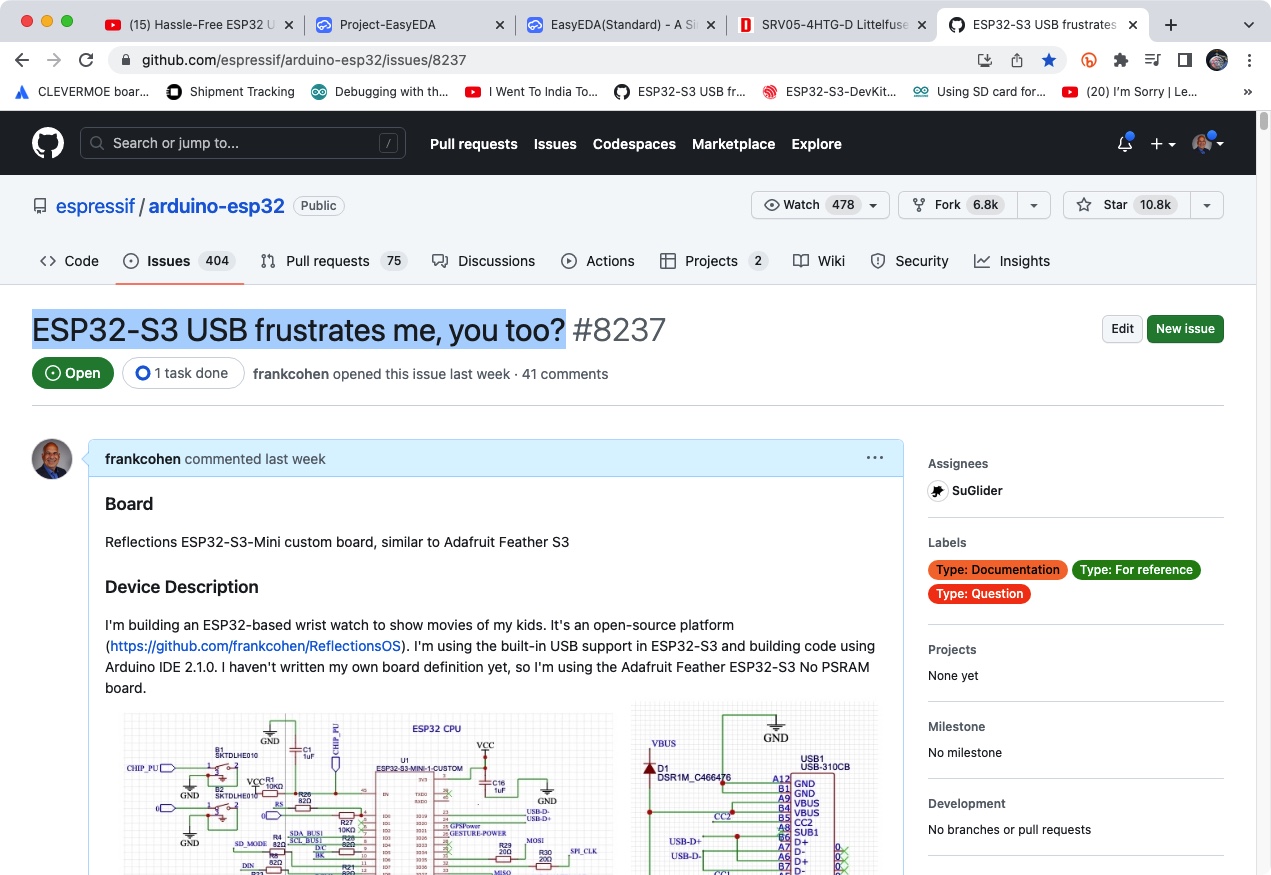
Docs/images/Reddit_USB_Frustratiing.jpg
