frankcohen/ReflectionsOS/Experiments/Parallax 3D Wallpaper/parallax_cat_face/cat1.jpg

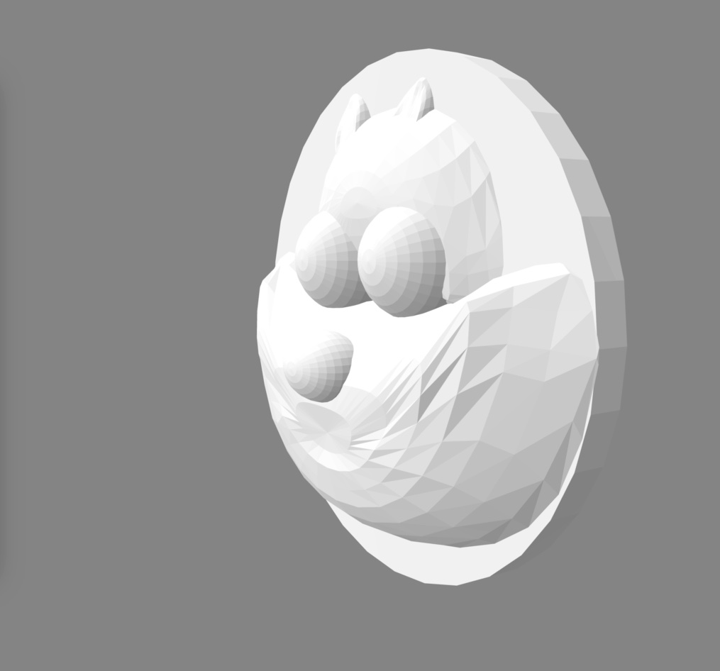
Experiments/Parallax 3D Wallpaper/parallax_cat_face/cat1.jpg
