frankcohen/ReflectionsOS/Experiments/Parallax 3D Wallpaper/parallax_cat_face/cat3.jpg

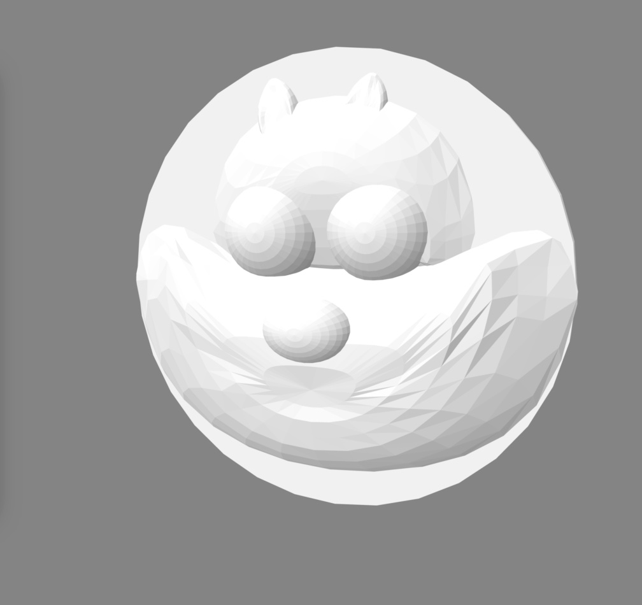
Experiments/Parallax 3D Wallpaper/parallax_cat_face/cat3.jpg
