frankcohen/ReflectionsOS/Devices/Sox/Schematic/PCBway/BOM.xlsx

Quantity | Reference | Part | Package | Manufacturer | Mfg # | Distributor | Dist #
17 | C1,C4,C5,C6,C9,C10,C12,C14,C15,C16,C17,C18,C20,C21,C22,C25,C26 | 1uF | C0402 | muRata(村田) | GRT155R70J105KE01D | LCSC | C711581
4 | C2,C3,C13,C23 | 10uF | C0402 | SAMSUNG(三星) | CL05A106MQ5NUNZ | LCSC | C2839440
1 | C7 | 100pF | C0402 | KEMET | C0402C101J5GAC7867 | LCSC | C140932
1 | C11 | 4.7uF | C0402 | Taiyo Yuden | JMK105BBJ475MVHF | LCSC | C386009
1 | C24 | 2.2uF | C0402 | MuRata | GRM155R61A225KE95D | LCSC | C77002
1 | FPC1 | FPC-05F-12PH20 | FPC-SMD_12P-P0.50_FPC-05F-12PH20 | XUNPU(讯普) | FPC-05F-12PH20 | LCSC | C2856799
1 | L1 | 6.2nH | L0201 | MuRata | LQP03TG6N2H02D | LCSC | C86119
1 | L3 | 33nH | L0201 | TDK | MLG0603P33NHTZ10 | LCSC | C275197
1 | L4 | 2.2nH | IND-SMD_L1.0-W0.5-2 | Murata Electronics | LQW15AN2N2G80D | LCSC | C412264
1 | LED1 | XL-1608SURC-06 | LED0603-RD_RED | XINGLIGHT(成兴光) | XL-1608SURC-06 | LCSC | C965799
1 | P1 | Female header1*2P | HDR-TH_2P-P2.00-V-F-1 | BOOMELE | Female header1*2P | LCSC | C66509
2 | Q1,Q2 | FDN340P | SOT-23-3_L2.9-W1.3-P1.90-LS2.4-BR | TECH PUBLIC(台舟) | FDN340P | LCSC | C2890122
1 | R1 | 10K | R0402 | Stackpole Elec | RNCF0402BTE10K0 | LCSC | C346559
1 | R2 | 20K | R0402 | ResistorToday | PTFR0402B20K0N9 | LCSC | C351700
2 | R3,R4 | 100 | R0402 | ResistorToday | PTFR0402B100RN9 | LCSC | C328416
1 | R5 | 10.7K | R0402 | Guangdong Fenghua Advanced Tech | RC-02W1072FT | LCSC | C321262
1 | R6 | 2kΩ | R0201 | Uniroyal Elec | 0201WMF2001TEE | LCSC | C270358
3 | R7,R8,R12 | 5.6K | R0402 | Uniroyal Elec | 0402WGD5601TCE | LCSC | C423273
1 | R9 | 390K | R0402 | ResistorToday | AECR0402F390KK9 | LCSC | C352430
1 | R10 | 105K | R0402 | YAGEO | AC0402FR-07105KL | LCSC | C226742
1 | R11 | 6.8kΩ | R0402 | TA-I | RM04FTN6801 | LCSC | C156119
5 | R13,R16,R24,R26,R27 | 100K | R0402 | YAGEO | RC0402FR-07100KL | LCSC | C60491
4 | R14,R18,R19,R20 | 10K | R0402 | ResistorToday | AECR0402F10K0K9 | LCSC | C328298
3 | R15,R17,R23 | 300 | R0402 | ResistorToday | AECR0402F120RK9 | LCSC | C352482
3 | R21,R22,R25 | 62 | R0402 | ResistorToday | AECR0402F62R0K9 | LCSC | C352402
1 | RF2 | KH-IPEX-K501-29 | ANT-SMD_KH-IPEX-K501-29 | Shenzhen Kinghelm Elec | KH-IPEX-K501-29 | LCSC | C411563
1 | U1 | ESP32-S3-MINI-1-N8 | XCVR_ESP32-S3-MINI-1-N8
1 | U2 | 182Ω | R0402 | Multicomp | MCWR04X1820FTL | LCSC | C241158
1 | U3 | XTSD01GLGEAG | LGA-8_L6.0-W8.0-P1.27-BL | XTX | XTSD01GLGEAG | LCSC | C558837
1 | U4 | 7L26003006 | OSC-SMD_4P-L2.5-W2.0-BL_7L-XXXXXXX | TXC(台湾晶技) | 7L26003006 | LCSC | C2452269
1 | U5 | AT6558R | QFN-40_L5.0-W5.0-P0.40-BL-EP | ZHONGKEWEI | AT6558R | LCSC | C350653
1 | U6 | DRV2605LDGSR | VSSOP-10_L3.0-W3.0-P0.50-LS4.9-BL | Texas Instruments | DRV2605LDGSR | LCSC | C527464
1 | U7 | 6.8K | R0402 | ResistorToday | HPCR0402F6K80K9 | LCSC | C365045
1 | U8 | LIS2DH12TR | LGA-12_L2.0-W2.0-P0.50-BL | STMicroelectronics | LIS2DH12TR | LCSC | C110926
1 | U10 | TP4057_C725791 | SOT-23-6_L2.9-W1.6-P0.95-LS2.8-BR | UMW(Youtai Semiconductor Co., Ltd.) | TP4057 | LCSC | C725791
1 | U11 | MMC5603NJ | FLIPCHIP-4_L0.8-W0.8-R2-C2-P0.40-TL | MEMSIC | MMC5603NJ | LCSC | C404328
1 | U12 | MAX98357AEWL+T | WLP-9_L1.4-W1.3-P0.40-R3-C3-BR | MAXIM(美信) | MAX98357AEWL+T | LCSC | C2682619
1 | U13 | MD7671B50SF4 | ESOP-8_L4.9-W3.9-P1.27-LS6.0-BL-EP | Shanghai Mingda Microelectronics | MD7671B50SF4 | LCSC | C920512
1 | U14 | 680 | R0402 | ResistorToday | HPCR0402F680RK9 | LCSC | C365041
1 | USB1 | USB-310CB | USB-C-SMD_20P-P0.50-L6.5-W11.2 | HOOYA | USB-310CB | LCSC | C309373
1 | X1 | 32.768KHz | CRYSTAL-SMD_L1.6-W1.0 | KDS Daishinku | DST1610A-32.768KHz | LCSC | C93230
