frankcohen/ReflectionsOS/Devices/Hoober/BOM Hoober Avinadad.xlsx

ID | Name | Designator | Footprint | Quantity | Manufacturer Part | Manufacturer | Digikey | Supplier Part | Price
1 | 1uF | C1,C4,C5,C6,C9,C10,C12,C14,C15,C16,C17,C18,C20,C21,C25,C26 | C0402 | 16 | CL05B105KQ5NQNC | Samsung Electro-Mechanics | Digikey | 1276-1513-2-ND | 0.028
2 | 10uF | C2,C3,C13,C23 | C0402 | 4 | C0402X5R6R3-106MNP-CT | Venkel | Digikey | 2679-C0402X5R6R3-106MNP-CT-ND | 0.009
3 | 100pF | C7 | C0402 | 1 | C0402C101J5GAC7867 | KEMET | Digikey | C140932 | 0.005
4 | 100nF | C8,C19 | C0402 | 2 | CL10B104KB8WPND | Samsung Electro-Mechanics | Digikey | 1276-CL10B104KB8WPNDTR-ND | 0.003
5 | 4.7uF | C11 | C0402 | 1 | JMK105BBJ475MVHF | Taiyo Yuden | Digikey | C386009 | 0.014
6 | 2.2uF | C24 | C0402 | 1 | JMK105C6225KV | Taiyo Yuden | Digikey | 587-JMK105C6225KV-FTR-ND | 0.006
7
8 | Header-Male-2.54_1x4 | H1 | HDR-TH_4P-P2.54-V-M | 1 | 210S-1*4P L=11.6MMGold-plated black | Ckmtw | LCSC | C124378 | 0.049
9 | DF65-3P-1.7V_21_ | J1 | DF65-3P-1.7V(21) | 1 | DF65-3P-1.7V(21) | Hirose Electric Co Ltd | Digikey | H122499TR-ND
10
11 | 6.2nH | L1 | L0201 | 1 | LQP03TG6N2H02D | MuRata | Digikey | C86119 | 0.008
12 | 33nH | L3 | L0201 | 1 | MLG0603P33NHTZ10 | TDK | LCSC | C275197 | 0.004
13 | 2.2nH | L4 | IND-SMD_L1.0-W0.5-2 | 1 | LQW15AN2N2G80D | Murata Electronics | Digikey | 490-LQW15AN2N2G80DCT-ND | 0.111
14 | XL-1608SURC-06 | LED1 | LED0603-RD_RED | 1 | XL-1608SURC-06 | XINGLIGHT(成兴光) | LCSC | C965799 | 0.004
15 | FDN340P_C2890122 | Q1 | SOT-23-3_L2.9-W1.3-P1.90-LS2.4-BR | 1 | FDN340P | TECH PUBLIC(台舟) | LCSC | C2890122 | 0.048
16 | FDN340P | Q2 | SOT-23-3_L2.9-W1.3-P1.90-LS2.4-BR | 1 | FDN340P | TECH PUBLIC(台舟) | LCSC | C2890122 | 0.048
17 | 10K | R1,R35 | R0402 | 2 | RNCF0402BTE10K0 | Stackpole Elec | Digikey | RNCF0402BTE10K0TR-ND | 0.098
18 | 30k | R2,R23 | R0402 | 2 | RMCF0402FT30K0TR-ND | Stackpole Elec | Digikey | RMCF0402FT30K0TR-ND
19 | 100 | R3,R4,R31 | R0402 | 3 | RC0402JR-07100RL | Yageo | Digikey | 311-100JRDKR-ND | 0.082
20 | 10K | R5,R8,R14,R20,R34,R29,R30 | R0402 | 7 | RNCF0402BTE10K0 | Stackpole Elec | Digikey | RNCF0402BTE10K0TR-ND | 0.004
21 | 2kΩ | R6 | R0201 | 1 | RMCF0201FT2K00 | Stackpole Elec | Digikey | RMCF0201FT2K00TR-ND | 0.001
22 | 5.6kΩ | R7,R17 | R0201 | 2 | CRGCQ0402F5K6 | TE Connectivity Passive Product | Digikey | A129636CT-ND | 0.002
23 | 390K | R9 | R0402 | 1 | AF0402FR-07390KL | YAGEO | Digikey | 13-AF0402FR-07390KLTR-ND | 0.002
24
25 | 6.8kΩ | R11 | R0402 | 1 | RMCF0402FT6K80 | Stackpole Electronics Inc | Digikey | RMCF0402FT6K80TR-ND | 0.002
26 | 5.6K | R12,R39 | R0402 | 2 | CRGCQ0402F5K6 | TE Connectivity Passive Product | Digikey | A129636TR-ND | 0.004
27 | 100K | R13,R16,R26,R27,R38,R10 | R0402 | 6 | RC0402FR-07100KL | YAGEO | Digikey | 311-100KJRTR-ND | 0.001
28 | 510 | R15 | R0402 | 1 | RC0402JR-07510RL | YAGEO | Digikey | 311-510JRTR-ND | 0.003
29 | 15K | R18,R19 | R0402 | 2 | RC0402FR-0715KL | YAGEO | Digikey | 311-15.0KLRTR-ND
30 | 62 | R21,R22,R25,R28 | R0402 | 4 | RMCF0402FT62R0 | Stackpole Electronics | Digikey | RMCF0402FT62R0TR-ND | 0.002
31 | 1MΩ | R24 | R0201 | 1 | ESR01MZPJ105 | ROHM Semicon | Digikey | RHM1005TR-ND | 0.011
32
33 | 20 | R32,R33,R37 | R0402 | 3 | RMCF0402JT20R0 | Stackpole Electronics Inc | Digikey | RMCF0402JT20R0TR-ND | 0.002
34 | 47kΩ | R36 | R0402 | 1 | RMCF0603FT47K0 | Stackpole Electronics Inc | Digikey | RMCF0603FT47K0TR-ND | 0.054
35 | KH-IPEX-K501-29 | RF2 | ANT-SMD_KH-IPEX-K501-29 | 1 | KH-IPEX-K501-29 | Shenzhen Kinghelm Elec | LCSC | C411563 | 0.071
36 | TBF313KQR | SW1,SW2,SW3 | KEY-SMD_4P-L3.5-W3.0-P1.50-LS4.7 | 3 | TBF313KQR | Diptronics | LCSC | C495957 | 0.228
37 | ESP32-S3-MINI-1-N8 | U1 | XCVR_ESP32-S3-MINI-1-N8 | 1
38 | 182Ω | U2 | R0402 | 1 | RC0402FR-07182RL | YAGEO | Digikey | YAG3016CT-ND | 0.002
39 | XTSD01GLGEAG | U3 | LGA-8_L6.0-W8.0-P1.27-BL | 1 | XTSD01GLGEAG | XTX | LCSC | C558837 | 2.292
40 | TCXO | U4 | OSC-SMD_4P-L2.5-W2.0-BL_7L-XXXXXXX | 1 | TXETALSANF-26.000000 | Taitien | Digikey | 1664-1264-1-ND
41 | AT6558R | U5 | QFN-40_L5.0-W5.0-P0.40-BL-EP | 1 | AT6558R | ZHONGKEWEI | LCSC | C350653 | 1.026
42 | DRV2605LDGSR | U6 | VSSOP-10_L3.0-W3.0-P0.50-LS4.9-BL | 1 | DRV2605LDGSR | Texas Instruments | LCSC | C527464 | 2.159
43 | 6.8K | U7 | R0402 | 1 | RMCF0402FT6K80 | Stackpole Electronics Inc | Digikey | RMCF0402FT6K80CT-ND | 0.004
44 | LIS2DH12TR | U8 | LGA-12_L2.0-W2.0-P0.50-BL | 1 | LIS2DH12TR | STMicroelectronics | LCSC | C110926 | 1.293
45 | TPS2113APW | U9 | TSSOP-8_L4.4-W3.0-P0.65-LS6.4-TL | 1 | TPS2113APW | TI(德州仪器) | Digikey | TPS2113APW | 2.034
46 | TP4057_C725791 | U10 | SOT-23-6_L2.9-W1.6-P0.95-LS2.8-BR | 1 | TP4057 | UMW(Youtai Semiconductor Co., Ltd.) | LCSC | C725791 | 0.094
47 | MMC5603NJ | U11 | FLIPCHIP-4_L0.8-W0.8-R2-C2-P0.40-TL | 1 | MMC5603NJ | MEMSIC | Digikey | 1267-MMC5603NJCT-ND | 0.331
48 | 74LVC1G74GF,115 | U12 | XSON-8_L1.4-W1.0-P0.35-S0.55-BL | 1 | 74LVC1G74GF,115 | Nexperia | Digikey | 74LVC1G74GF,115 | 0.469
49 | MD7671B50SF4 | U13 | ESOP-8_L4.9-W3.9-P1.27-LS6.0-BL-EP | 1 | MD7671B50SF4 | Shanghai Mingda Microelectronics | LCSC | C920512 | 0.246
50 | MAX98357AETE+T | U15 | TQFN-16_L3.0-W3.0-P0.50-BL-EP1.5 | 1 | MAX98357AETE+T | MAXIM(美信) | LCSC | C910544 | 1.569
51 | USB-310CB | USB1 | USB-C-SMD_20P-P0.50-L6.5-W11.2 | 1 | USB-310CB | HOOYA | LCSC | C309373 | 0.431
52 | - | X1 | OSC-SMD_L3.2-W1.5 | 1 | CM7V-T1A-32.768KHZ-12.5PF-20PPM-TA-QC | Micro Crystal AG | Digikey | 2195-CM7V-T1A-32.768KHZ-12.5PF-20PPM-TA-QCCT-ND - Cut Tape | 0.731
