frankcohen/ReflectionsOS/src/ReflectionsOS/build/esp32.esp32.esp32s3/flash_log.csv

timestamp | port | baud | result | exit_code | note | merged_bin
2026-01-20 14:26:38 | /dev/cu.usbmodem122301 | 921600 | FAIL | 2 | esptool failed; will retry lower baud | /Users/frankcohen/Documents/Arduino/ReflectionsOS/src/ReflectionsOS/build/esp32.esp32.esp32s3/ReflectionsOS.ino.merged.bin
2026-01-20 14:26:42 | /dev/cu.usbmodem122301 | 460800 | FAIL | 2 | esptool failed; will retry lower baud | /Users/frankcohen/Documents/Arduino/ReflectionsOS/src/ReflectionsOS/build/esp32.esp32.esp32s3/ReflectionsOS.ino.merged.bin
2026-01-20 14:26:45 | /dev/cu.usbmodem122301 | 115200 | FAIL | 2 | esptool failed; will retry lower baud | /Users/frankcohen/Documents/Arduino/ReflectionsOS/src/ReflectionsOS/build/esp32.esp32.esp32s3/ReflectionsOS.ino.merged.bin
2026-01-20 14:27:07 | /dev/cu.usbmodem122301 | 921600 | FAIL | 2 | esptool failed; will retry lower baud | /Users/frankcohen/Documents/Arduino/ReflectionsOS/src/ReflectionsOS/build/esp32.esp32.esp32s3/ReflectionsOS.ino.merged.bin
2026-01-20 14:27:10 | /dev/cu.usbmodem122301 | 460800 | FAIL | 2 | esptool failed; will retry lower baud | /Users/frankcohen/Documents/Arduino/ReflectionsOS/src/ReflectionsOS/build/esp32.esp32.esp32s3/ReflectionsOS.ino.merged.bin
2026-01-20 14:27:14 | /dev/cu.usbmodem122301 | 115200 | FAIL | 2 | esptool failed; will retry lower baud | /Users/frankcohen/Documents/Arduino/ReflectionsOS/src/ReflectionsOS/build/esp32.esp32.esp32s3/ReflectionsOS.ino.merged.bin
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
2026-01-20 15:07:52 | /dev/cu.usbmodem1224401 | f0:f5:bd:51:1a:10 | 921600 | OK | 0 | flashed merged.bin | /Users/frankcohen/Documents/Arduino/ReflectionsOS/src/ReflectionsOS/build/esp32.esp32.esp32s3/ReflectionsOS.ino.merged.bin
