frankcohen/ReflectionsOS/Experiments/Recorder4/README.md

# Reflections Recorder version 4

Moved to 
https://github.com/frankcohen/ReflectionsOS/tree/main/CloudCity/Recorder

-Frank
August 8, 2023
