frankcohen/ReflectionsOS/Devices/Horton/Datasheets/Annie Test Code 7fe819344983bc1aaa16103deedac08b.txt

void GC9A01_HSD1.28_Init(void)
{
LCD_RST = 1;
delayms(120);
LCD_RST = 0;
delayms(100); 
LCD_RST = 1;
delayms(120);
SPI_WriteComm(0xFE);			 
SPI_WriteComm(0xEF); 

SPI_WriteComm(0xEB);	
SPI_WriteData(0x14); 

SPI_WriteComm(0x84);			
SPI_WriteData(0x40); 

SPI_WriteComm(0x85);
SPI_WriteData(0xFF); 

SPI_WriteComm(0x86);            
SPI_WriteData(0xFF); 

SPI_WriteComm(0x87);            
SPI_WriteData(0xFF);

SPI_WriteComm(0x8E);        
SPI_WriteData(0xFF); 

SPI_WriteComm(0x8F);     
SPI_WriteData(0xFF); 

SPI_WriteComm(0x88);			
SPI_WriteData(0x0A);

SPI_WriteComm(0x89);			
SPI_WriteData(0x21); 

SPI_WriteComm(0x8A);			
SPI_WriteData(0x00); 

SPI_WriteComm(0x8B);			
SPI_WriteData(0x80); 

SPI_WriteComm(0x8C);			
SPI_WriteData(0x01); 

SPI_WriteComm(0x8D);			
SPI_WriteData(0x01); 

//正扫
SPI_WriteComm(0xB6);			
SPI_WriteData(0x00); 
SPI_WriteData(0x00); 

SPI_WriteComm(0x36);			
SPI_WriteData(0x48);

SPI_WriteComm(0x3A);			
SPI_WriteData(0x05); 

SPI_WriteComm(0x90);			
SPI_WriteData(0x08);
SPI_WriteData(0x08);
SPI_WriteData(0x08);
SPI_WriteData(0x08); 

SPI_WriteComm(0xBD);			
SPI_WriteData(0x06);

SPI_WriteComm(0xBC);			
SPI_WriteData(0x00);	

SPI_WriteComm(0xFF);			
SPI_WriteData(0x60);
SPI_WriteData(0x01);
SPI_WriteData(0x04);

SPI_WriteComm(0xC3);			
SPI_WriteData(0x1d);
SPI_WriteComm(0xC4);			
SPI_WriteData(0x1d);

SPI_WriteComm(0xC9);			
SPI_WriteData(0x25);

SPI_WriteComm(0xBE);			
SPI_WriteData(0x11); 

SPI_WriteComm(0xE1);
SPI_WriteData(0x10);
SPI_WriteData(0x0E);

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

SPI_WriteComm(0x98);			
SPI_WriteData(0x3e);
SPI_WriteData(0x07);

SPI_WriteComm(0x35);	
SPI_WriteData(0x00); 
SPI_WriteComm(0x21);
Delay(120);
//--------end gamma setting--------------//

SPI_WriteComm(0x11);
Delay(120);
SPI_WriteComm(0x29);
Delay(120);
SPI_WriteComm(0x2C);
Delay(120);
