frankcohen/ReflectionsOS/Experiments/Range Heading Distance RHD/Angle model.ods

Reflections by Frank Cohen, fcohen@starlingwatch.com, July 3, 2023
Solving the Range Heading Distance Experiment using Law Of Cosines
https://www.youtube.com/watch?v=9CGY0s-uCUE
Step 1) Solve for angle C using c^2 = a^2 + b^2 – 2ab cos z
a | 200 | 40000
b rssi | 36.33 | 1319.8689
c | 200 | 40000
 | -1319.8689 | 0.090825
 |  | 1.479845989
 | C = | 84.7889294987 | degrees
Step 2) Solve for angle C using a^2 = b^2 + c^2 – 2bc cos x
 | -1319.8689 | 0.090825
 |  | 1.479845989
 | A = | 84.7889294987 | degrees
Step 3) Solve for angle B using 180 = a + b + c
 | B = | 10.4221410027 | degrees
Step 4)
Alternate method to solve for angle A
 | -0.9100351993 | -6.3702463949 | = 9 sin A
 |  | -0.707805155 | = sin A
 | A = | 45.0566161414
 | B = | 50.15445436
