frankcohen/ReflectionsOS/Experiments/Range Heading Distance RHD/Cat_RHD_Faces/cat_6_baseline.jpg

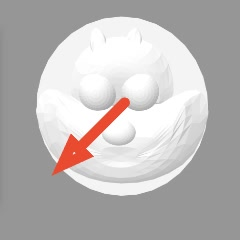
Experiments/Range Heading Distance RHD/Cat_RHD_Faces/cat_6_baseline.jpg
