frankcohen/ReflectionsOS/Devices/Marvin/Benjamin display.pdf

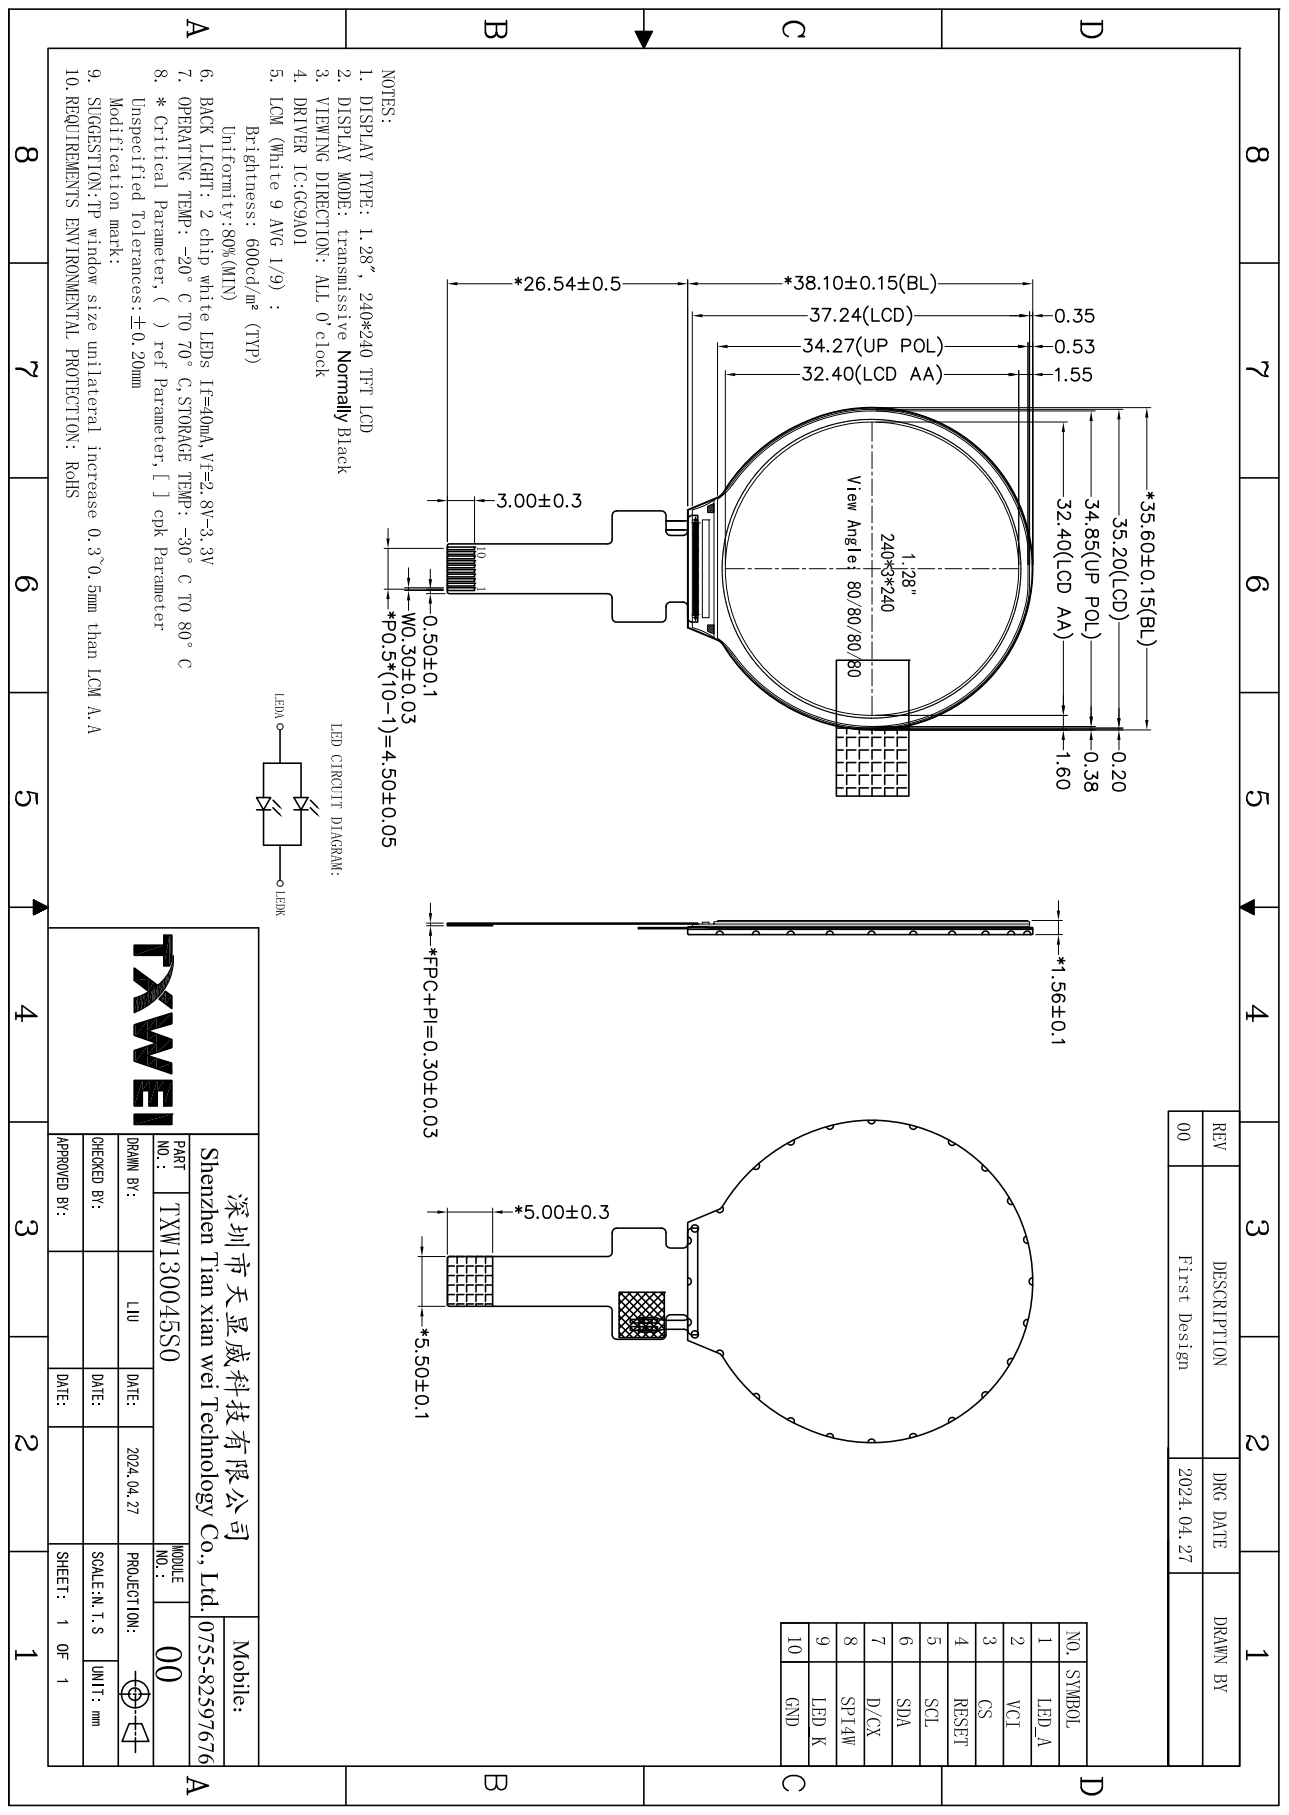
[picture p142: page 1]
