frankcohen/ReflectionsOS/Devices/Horton/pcb panelization banke transfer.pdf

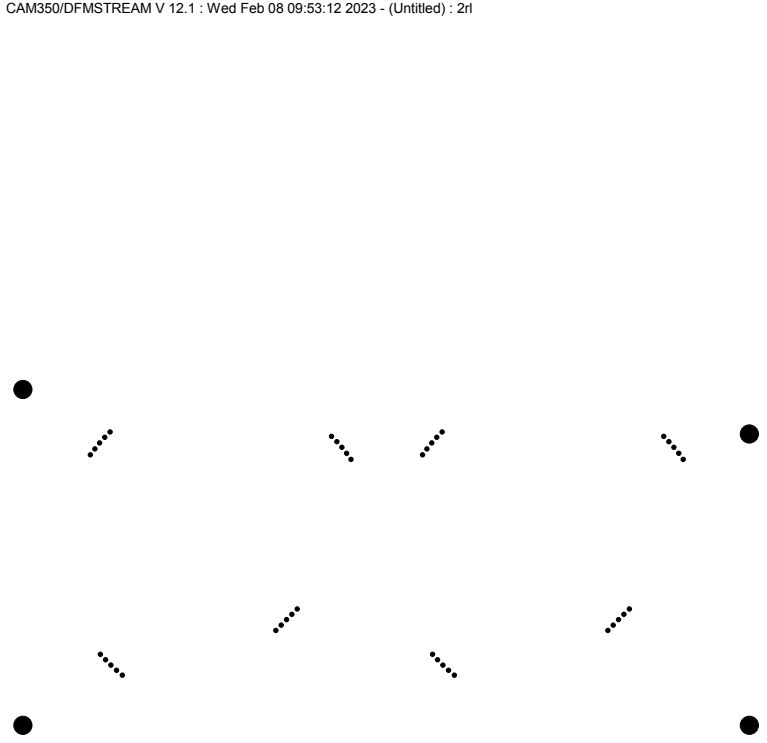
[picture p143: page 1]

CAM350/DFMSTREAM V 12.1 : Wed Feb 08 09:53:12 2023 - (Untitled) : 2rl

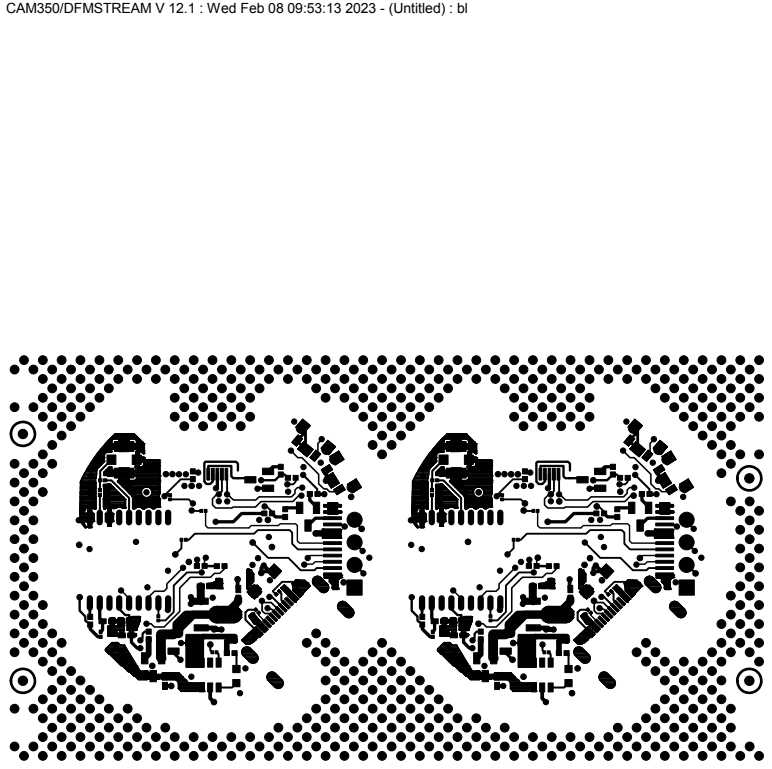
[picture p144: page 2]

CAM350/DFMSTREAM V 12.1 : Wed Feb 08 09:53:13 2023 - (Untitled) : bl

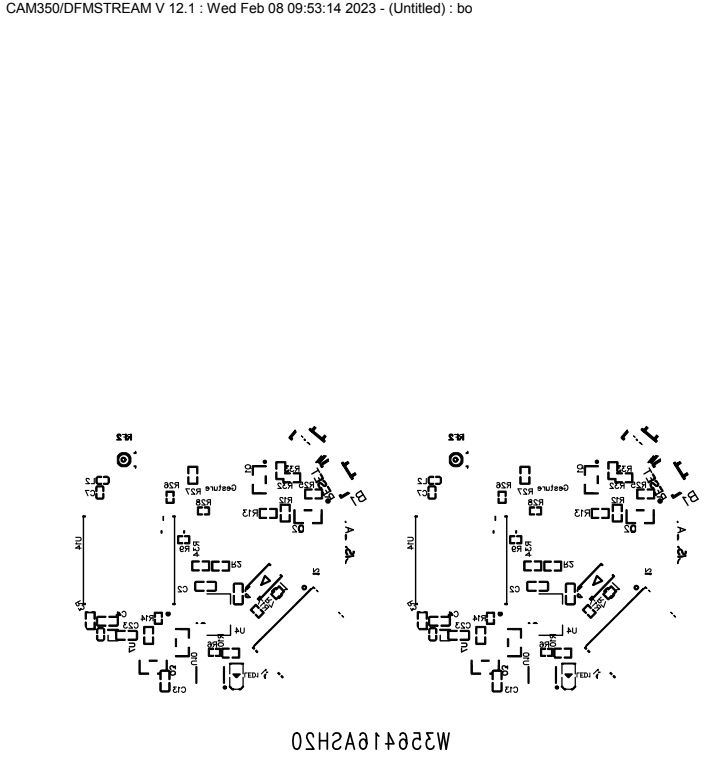
[picture p145: page 3]

CAM350/DFMSTREAM V 12.1 : Wed Feb 08 09:53:14 2023 - (Untitled) : bo

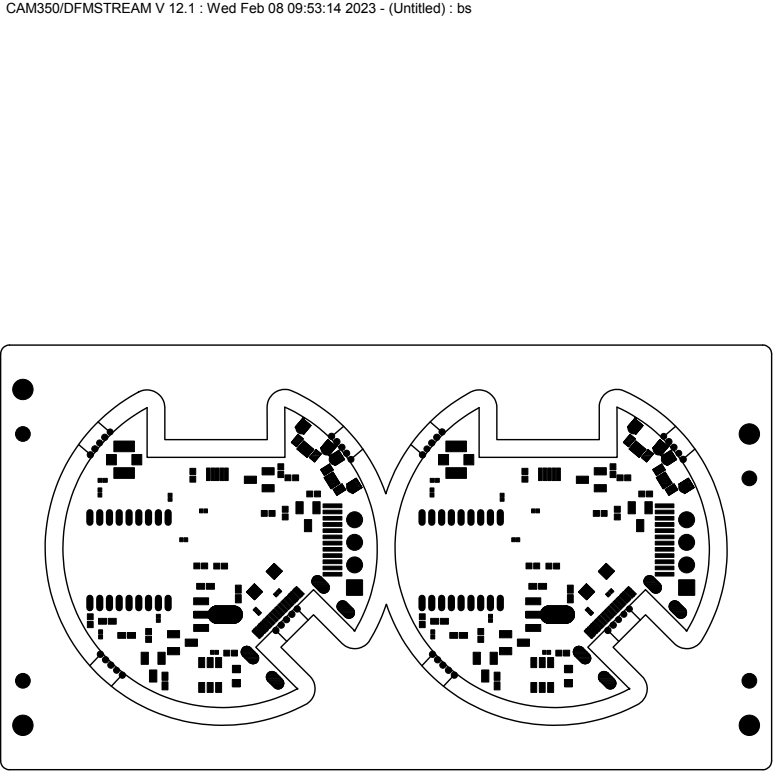
[picture p146: page 4]

CAM350/DFMSTREAM V 12.1 : Wed Feb 08 09:53:14 2023 - (Untitled) : bs

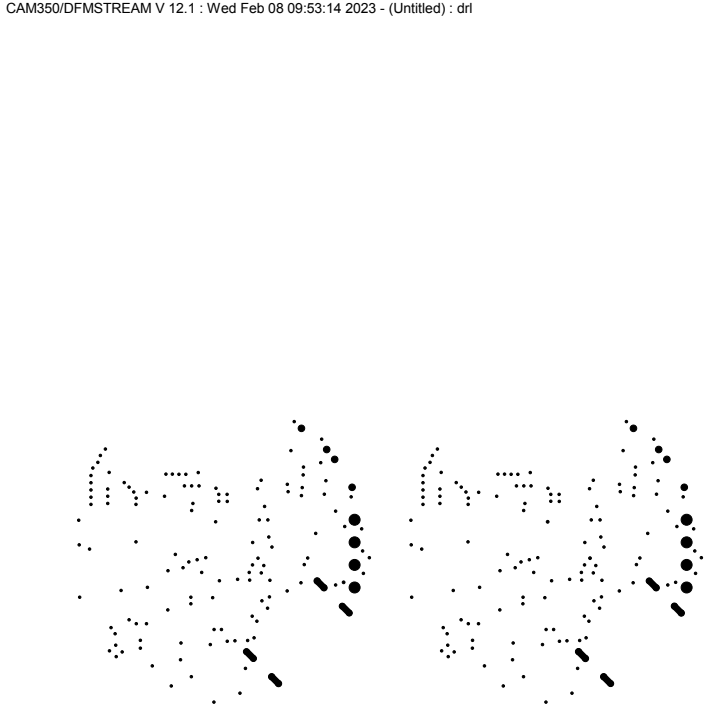
[picture p147: page 5]

CAM350/DFMSTREAM V 12.1 : Wed Feb 08 09:53:14 2023 - (Untitled) : drl

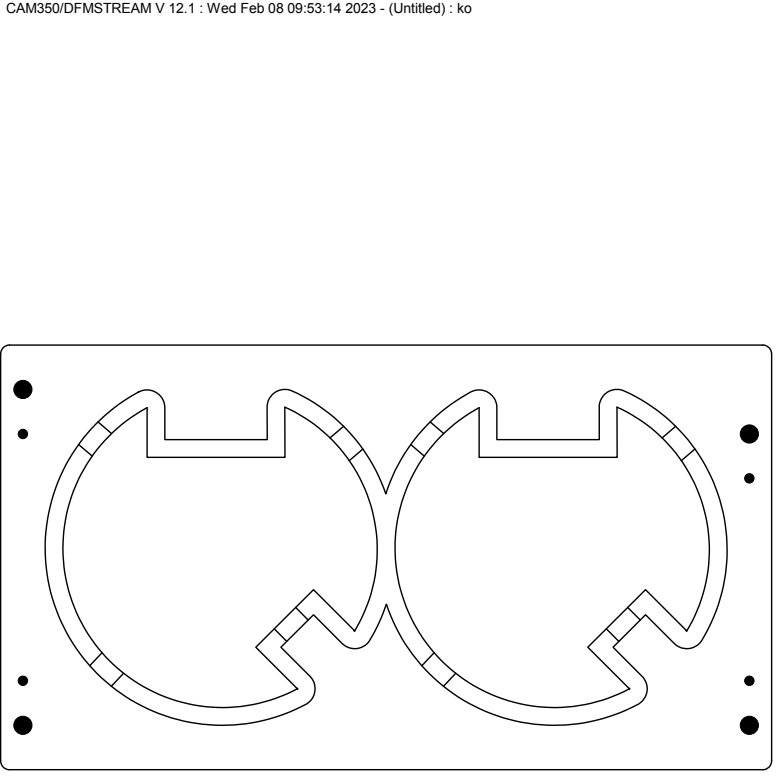
[picture p148: page 6]

CAM350/DFMSTREAM V 12.1 : Wed Feb 08 09:53:14 2023 - (Untitled) : ko

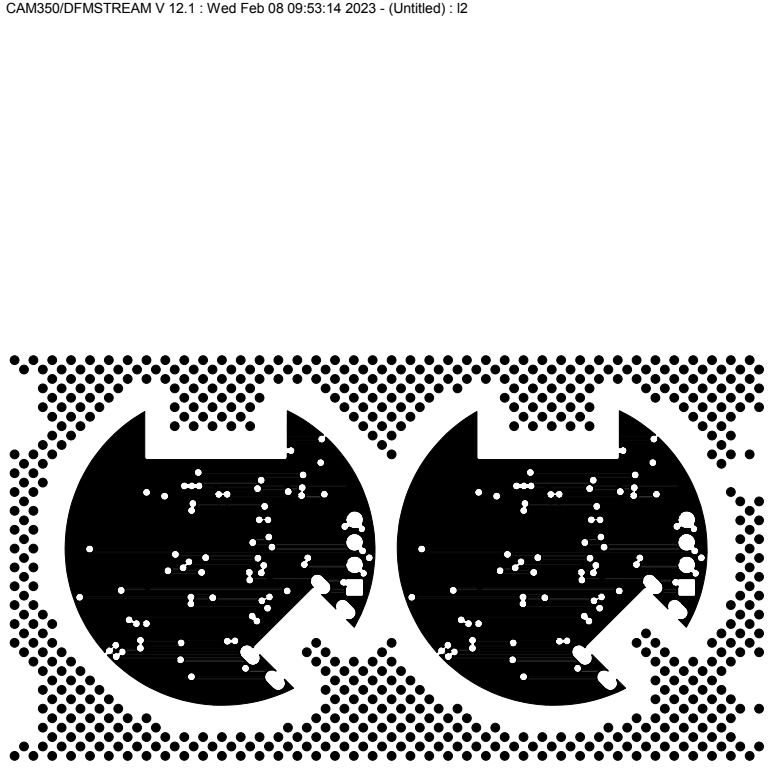
[picture p149: page 7]

CAM350/DFMSTREAM V 12.1 : Wed Feb 08 09:53:14 2023 - (Untitled) : l2

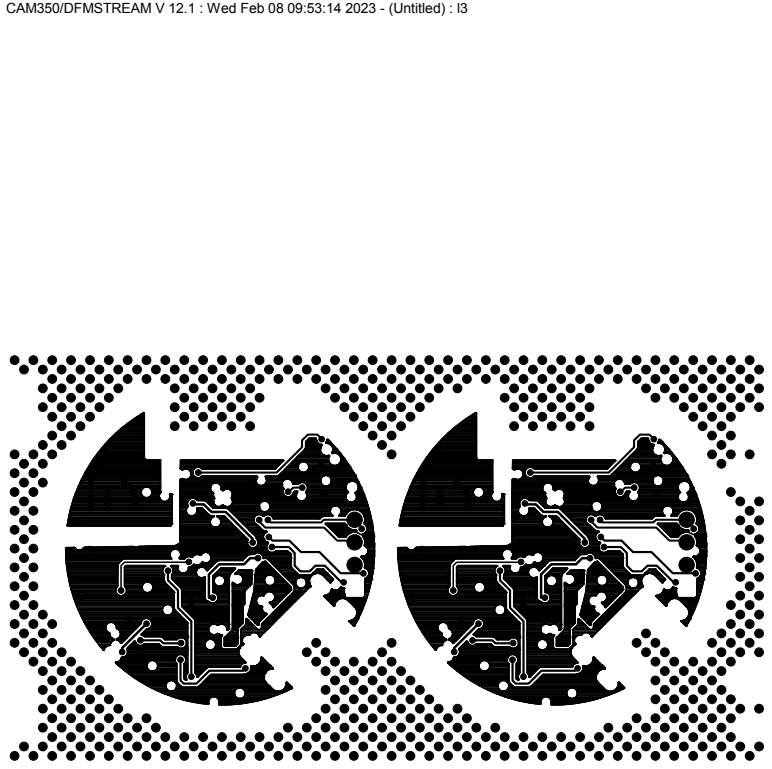
[picture p150: page 8]

CAM350/DFMSTREAM V 12.1 : Wed Feb 08 09:53:14 2023 - (Untitled) : l3

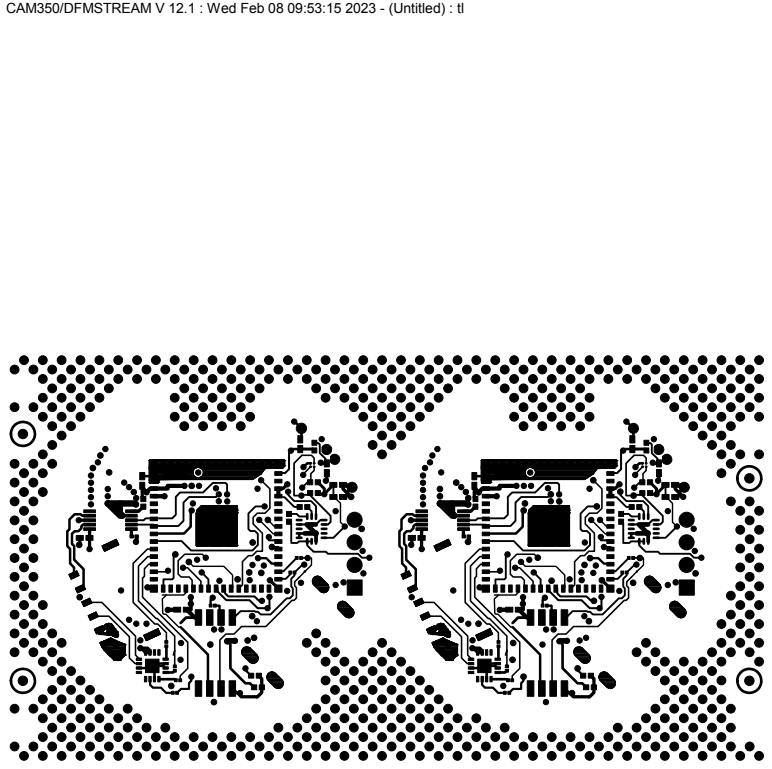
[picture p151: page 9]

CAM350/DFMSTREAM V 12.1 : Wed Feb 08 09:53:15 2023 - (Untitled) : tl

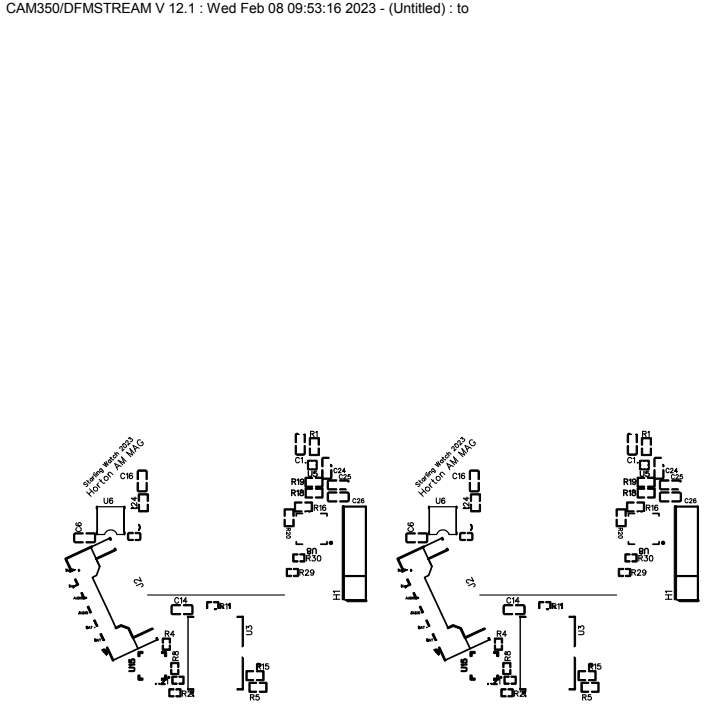
[picture p152: page 10]

CAM350/DFMSTREAM V 12.1 : Wed Feb 08 09:53:16 2023 - (Untitled) : to

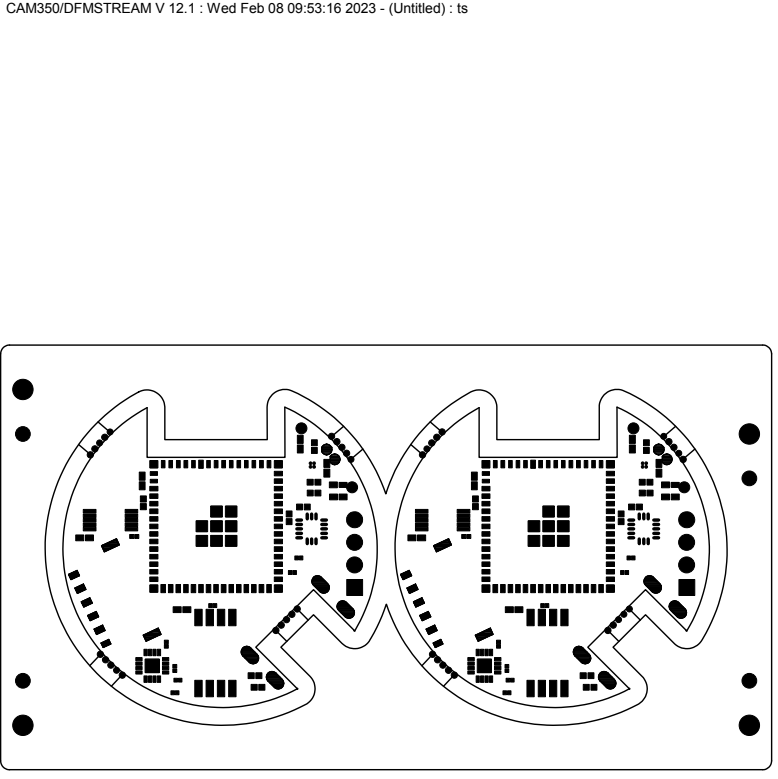
[picture p153: page 11]

CAM350/DFMSTREAM V 12.1 : Wed Feb 08 09:53:16 2023 - (Untitled) : ts
