frankcohen/ReflectionsOS/Devices/VladPlus/layouts/BottomLayer.pdf

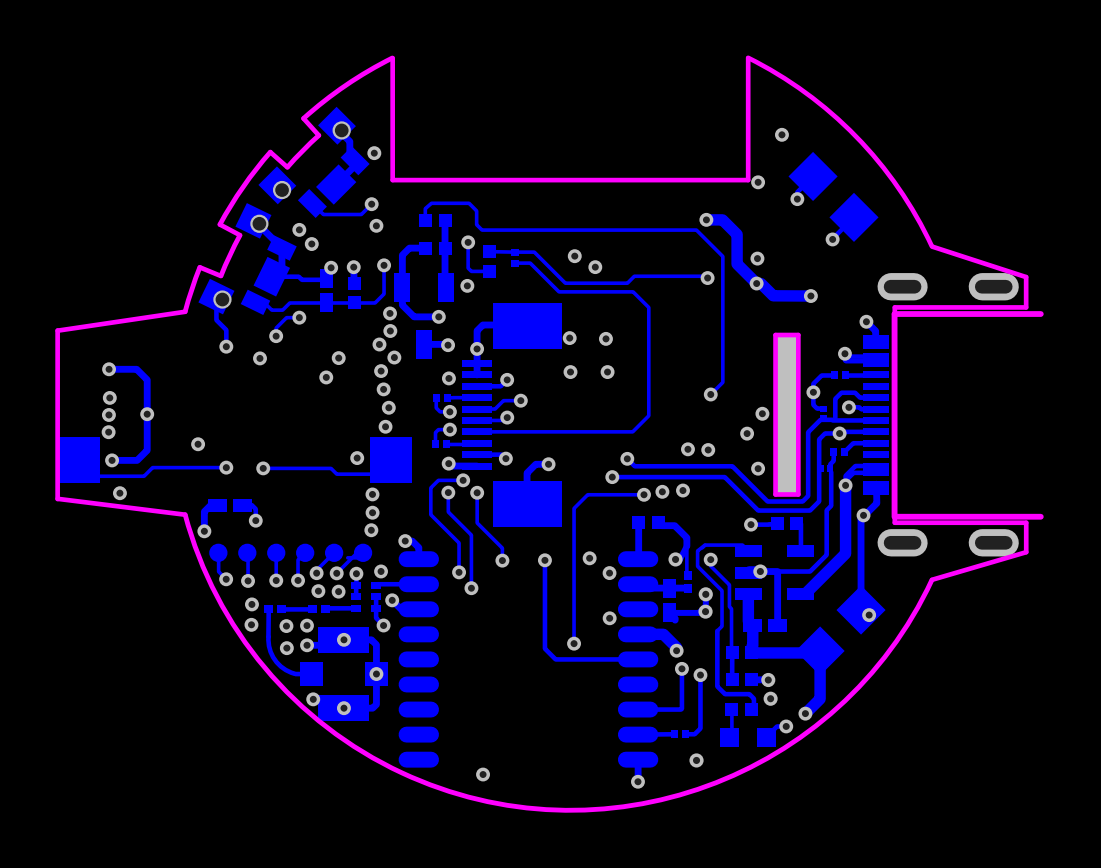
[picture p154: page 1]
