frankcohen/ReflectionsOS/Devices/VladPlus/layouts/BottomPasteMaskLayer.pdf

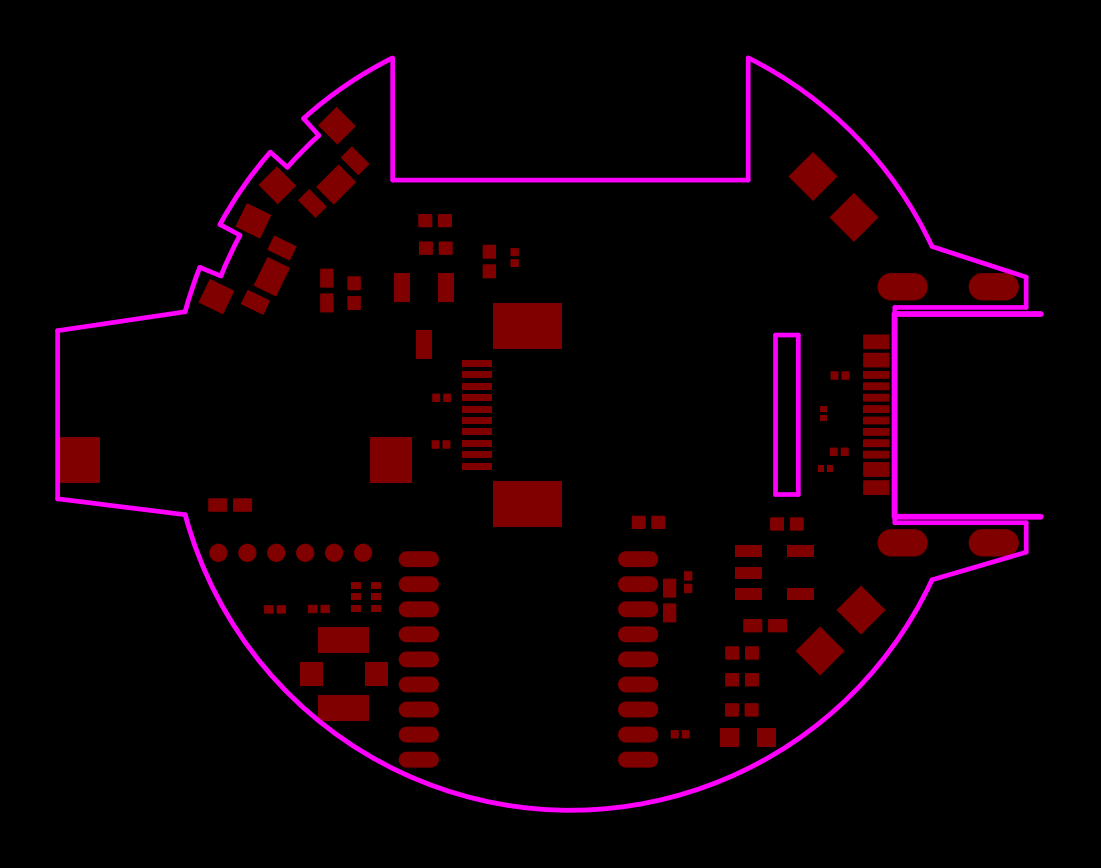
[picture p155: page 1]
