frankcohen/ReflectionsOS/Devices/VladPlus/layouts/BottomSilkLayer.pdf

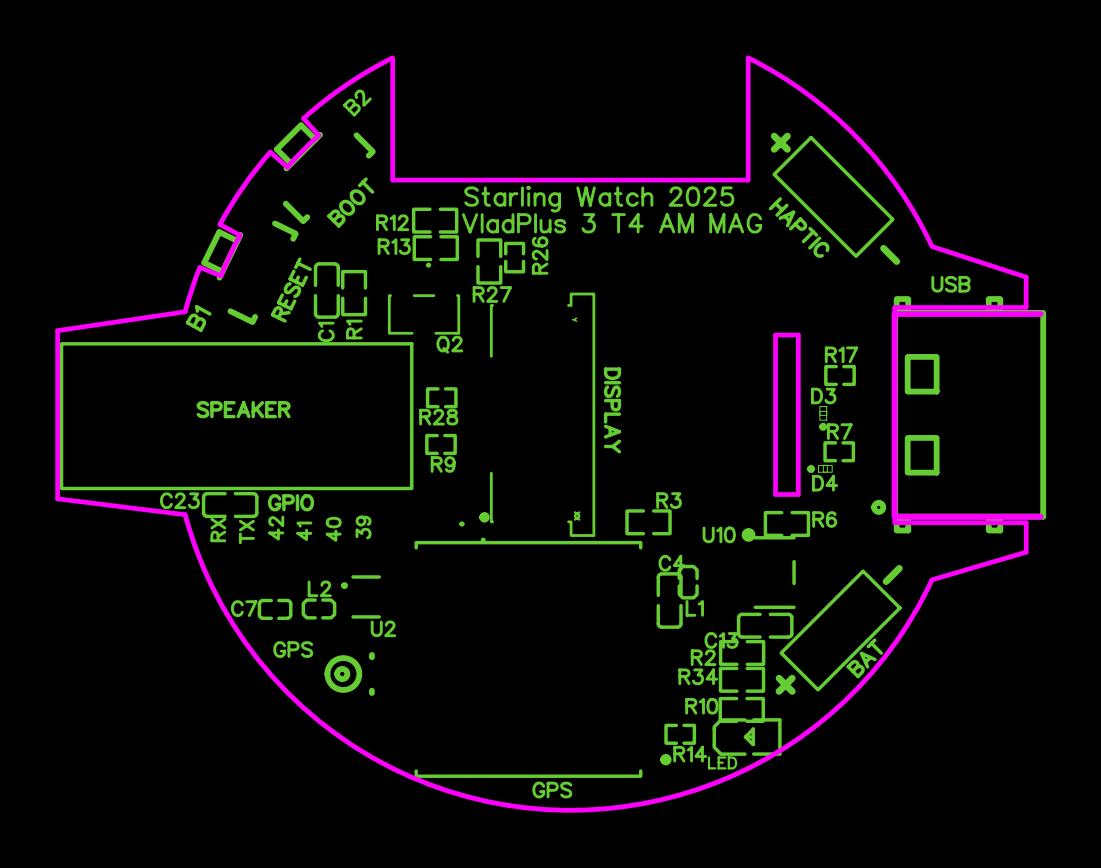
[picture p156: page 1]
