frankcohen/ReflectionsOS/Devices/VladPlus/layouts/Document.pdf

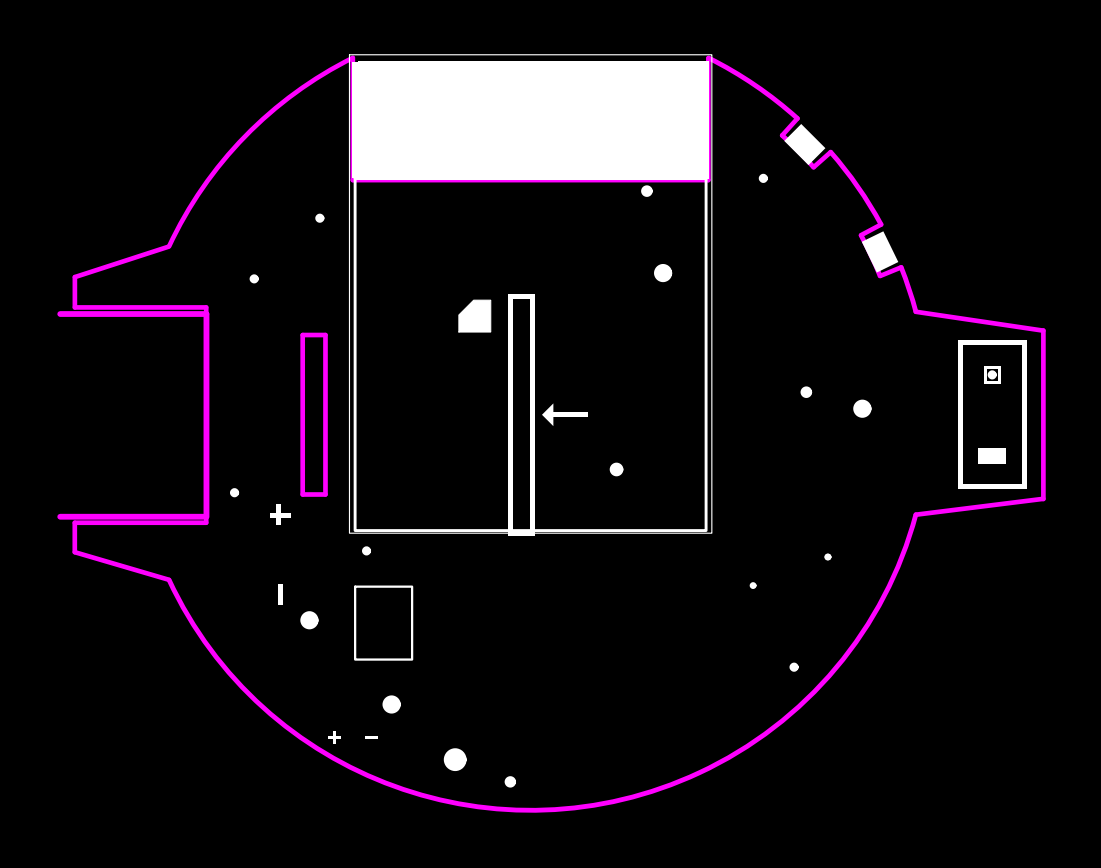
[picture p157: page 1]
