frankcohen/ReflectionsOS/Devices/VladPlus/layouts/Inner1.pdf

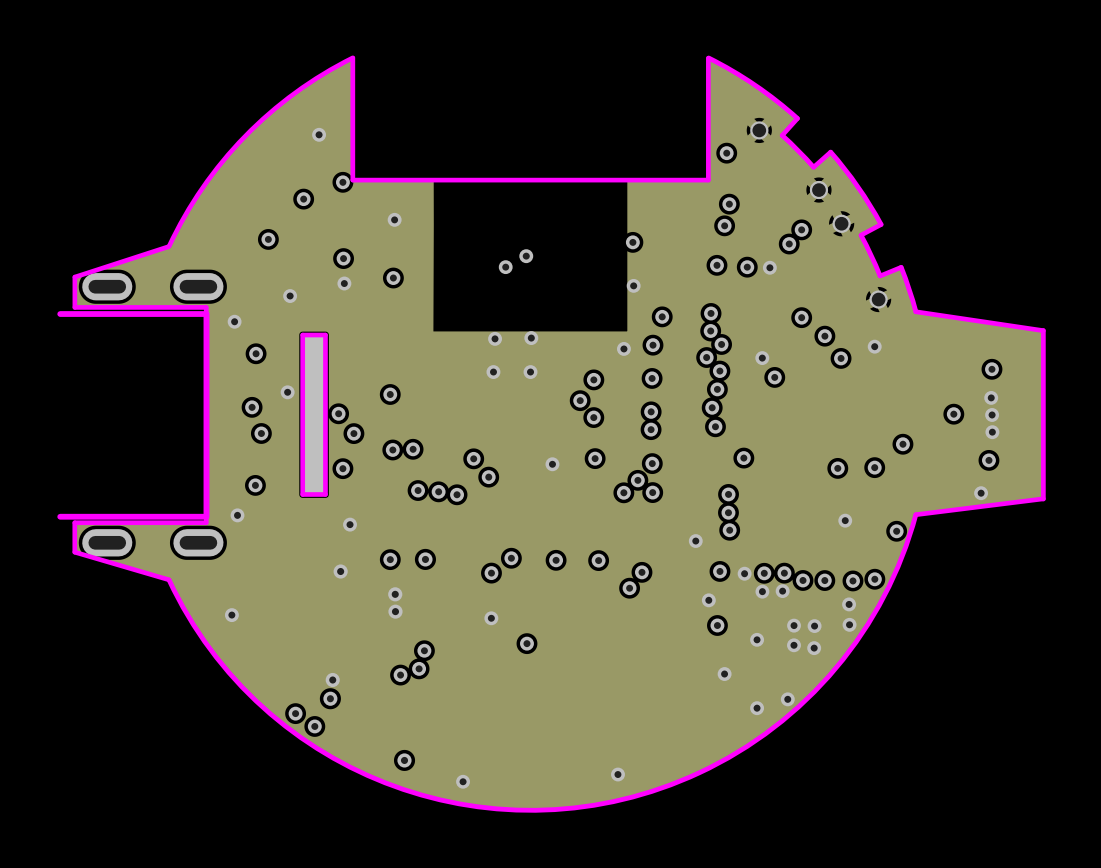
[picture p158: page 1]
