frankcohen/ReflectionsOS/Devices/VladPlus/layouts/Inner2.pdf

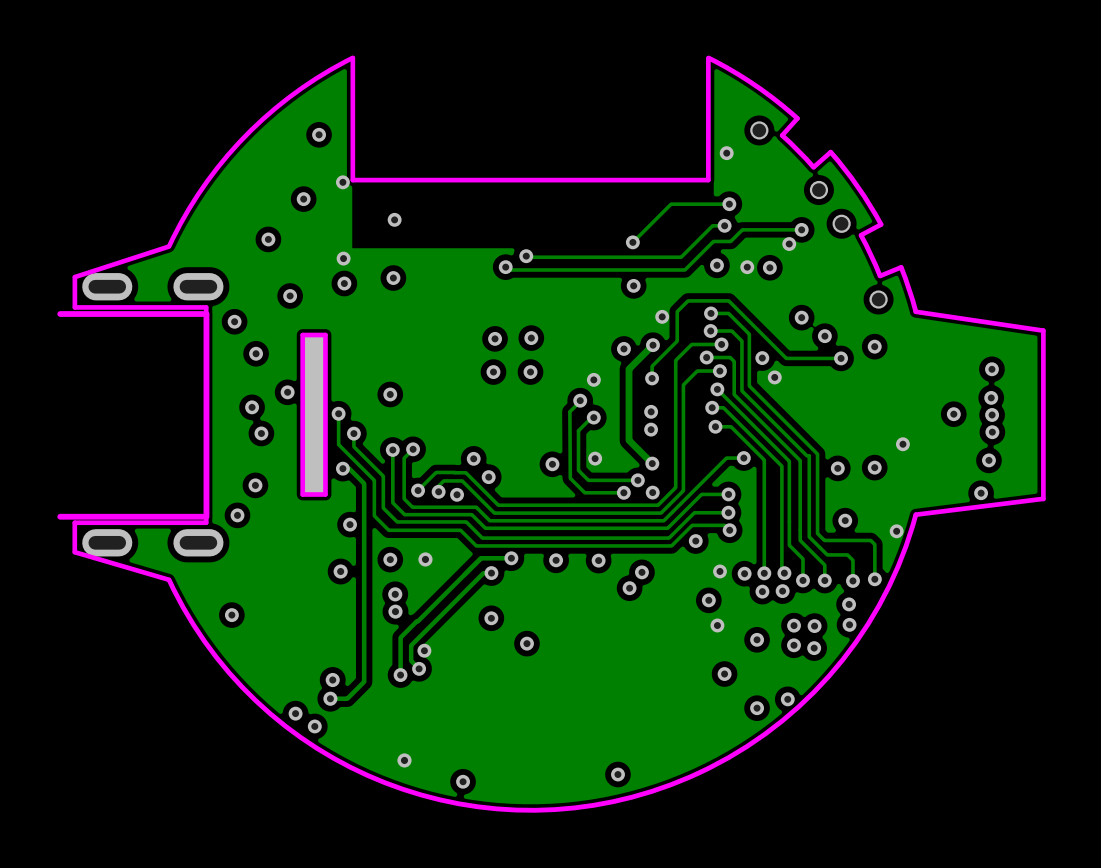
[picture p159: page 1]
