frankcohen/ReflectionsOS/Devices/VladPlus/layouts/Multi-Layer.pdf

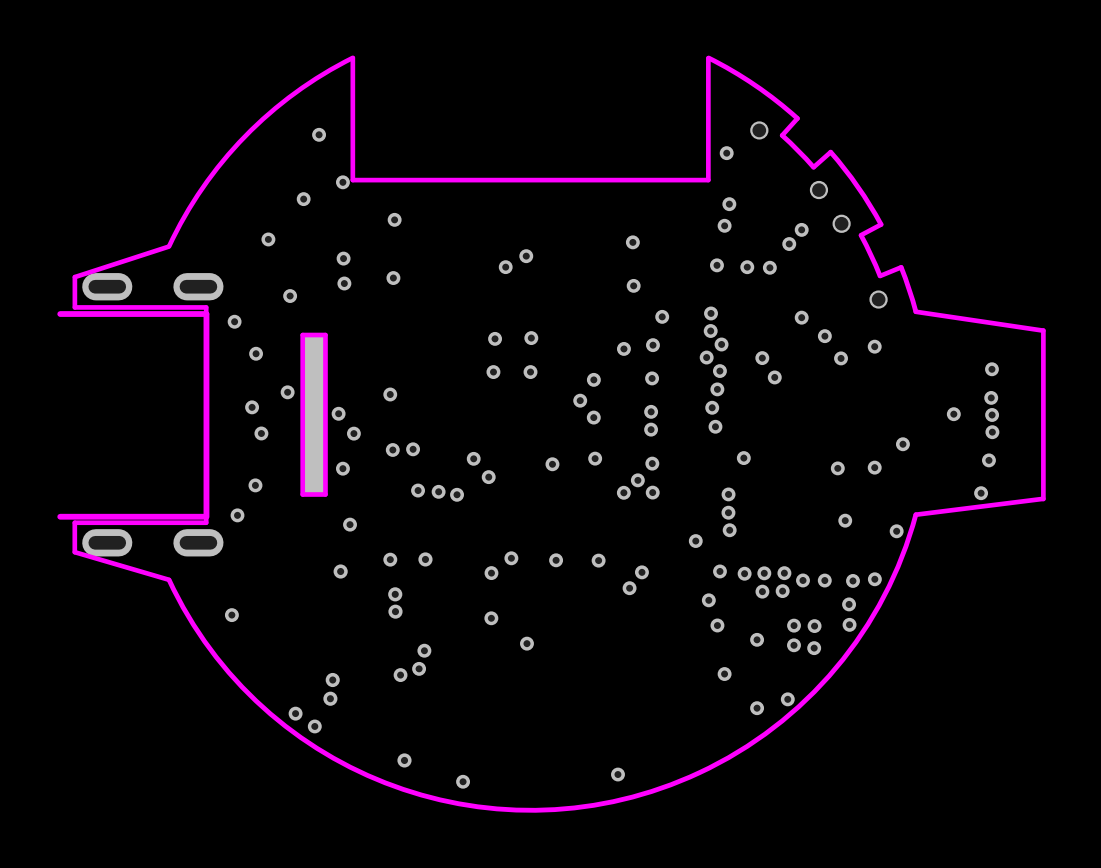
[picture p160: page 1]
