frankcohen/ReflectionsOS/Devices/VladPlus/layouts/TopLayer.pdf

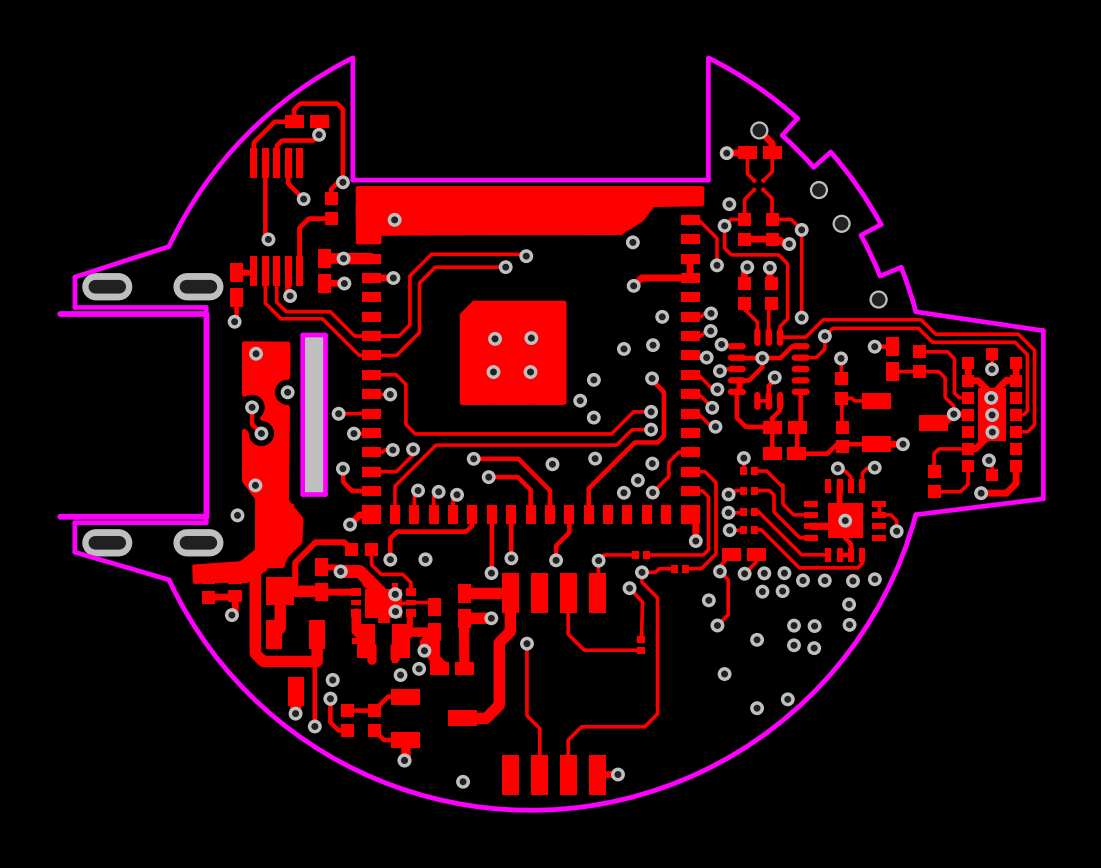
[picture p161: page 1]
