frankcohen/ReflectionsOS/Devices/VladPlus/layouts/TopPasteMaskLayer.pdf

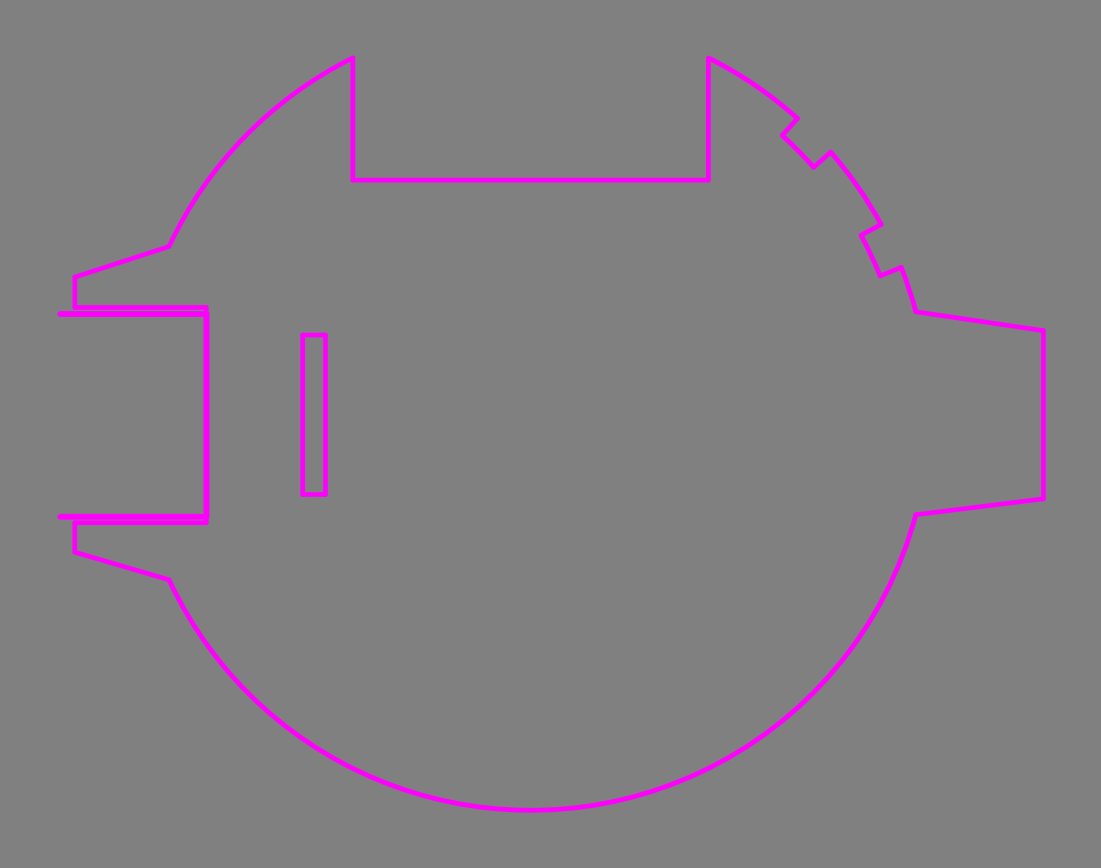
[picture p162: page 1]
