frankcohen/ReflectionsOS/Devices/VladPlus/layouts/TopSilkLayer.pdf

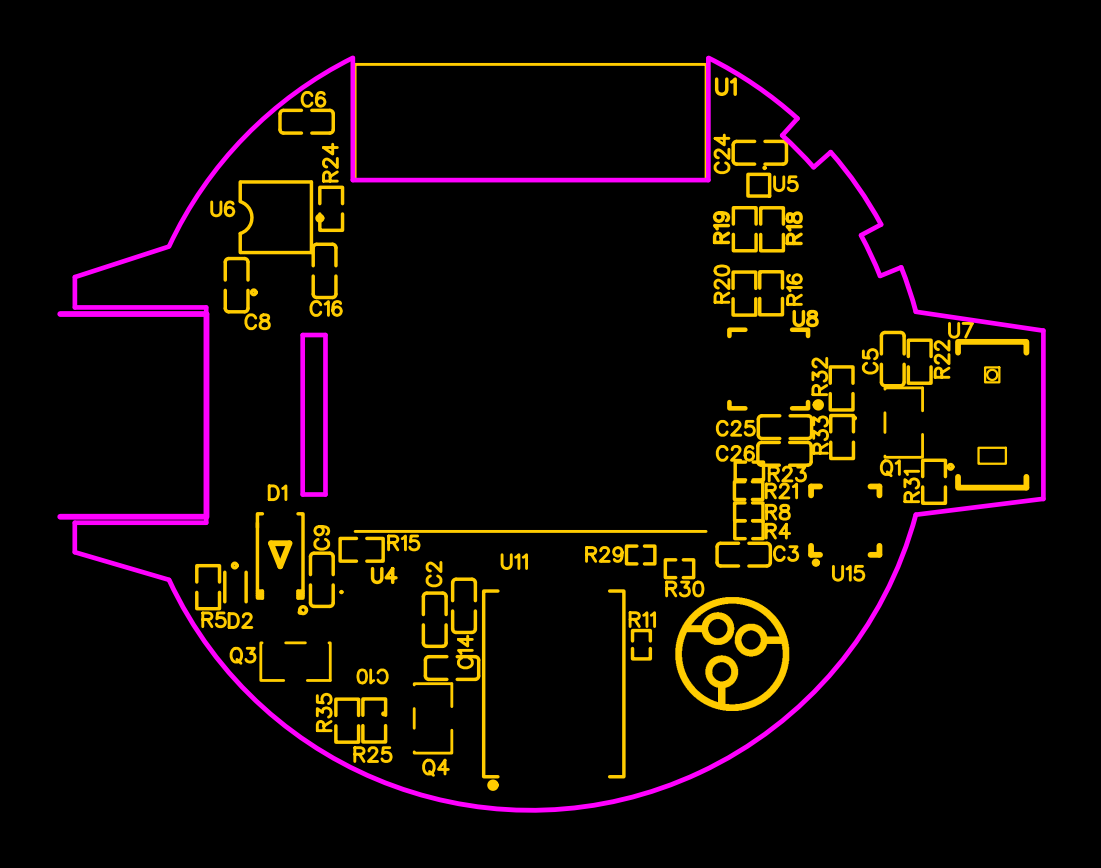
[picture p163: page 1]
