frankcohen/ReflectionsOS/Devices/Horton/Software/06Haptic/06Haptic.ino

#include <Wire.h>
#include "Adafruit_DRV2605.h"

Adafruit_DRV2605 drv;

#define I2C2_SDA 3
#define I2C2_SCL 4

void scan() {
  Serial.println("\nI2C Scanner");
  byte error, address;
  int nDevices;
  nDevices = 0;
  for(address = 1; address < 127; address++ ) {
    Wire.beginTransmission(address);
    error = Wire.endTransmission();
    if (error == 0) {
      Serial.print("I2C device found at address 0x");
      if (address<16) {
        Serial.print("0");
      }
      Serial.println(address,HEX);
      nDevices++;
    }
    else if (error==4) {
      Serial.print("Unknow error at address 0x");
      if (address<16) {
        Serial.print("0");
      }
      Serial.println(address,HEX);
    }    
  }
  if (nDevices == 0) {
    Serial.println("No I2C devices found\n");
  }
  else {
    Serial.println("done\n");
  }
}

void setup() {
  Serial.begin(115200);
  long time = millis();
  while (!Serial && ( millis() < time + 5000) ); // wait up to 5 seconds for Arduino Serial Monitor  
  Serial.setDebugOutput(true);
  Serial.println("Reflections Haptic research");

  Wire.begin(3,4);
  
  Serial.println("drv.begin");
  delay(1000);
  drv.begin();
  
  Serial.println("drv.selectLibrary");
  drv.selectLibrary(1);
  
  // I2C trigger by sending 'go' command 
  // default, internal trigger when sending GO command
  drv.setMode(DRV2605_MODE_INTTRIG);

  Serial.println("done");

  //scan();
}

uint8_t effect = 1;

void loop() {
  Serial.print("Effect #"); Serial.println(effect);

   if (effect == 1) {
    Serial.println("11.2 Waveform Library Effects List");
  }

  if (effect == 1) {
    Serial.println(F("1 − Strong Click - 100%"));
  }
  if (effect == 2) {
    Serial.println(F("2 − Strong Click - 60%"));
  }
  if (effect == 3) {
    Serial.println(F("3 − Strong Click - 30%"));
  }
  if (effect == 4) {
    Serial.println(F("4 − Sharp Click - 100%"));
  }
  if (effect == 5) {
    Serial.println(F("5 − Sharp Click - 60%"));
  }
  if (effect == 6) {
    Serial.println(F("6 − Sharp Click - 30%"));
  }
  if (effect == 7) {
    Serial.println(F("7 − Soft Bump - 100%"));
  }
  if (effect == 8) {
    Serial.println(F("8 − Soft Bump - 60%"));
  }
  if (effect == 9) {
    Serial.println(F("9 − Soft Bump - 30%"));
  }
  if (effect == 10) {
    Serial.println(F("10 − Double Click - 100%"));
  }
  if (effect == 11) {
    Serial.println(F("11 − Double Click - 60%"));
  }
  if (effect == 12) {
    Serial.println(F("12 − Triple Click - 100%"));
  }
  if (effect == 13) {
    Serial.println(F("13 − Soft Fuzz - 60%"));
  }
  if (effect == 14) {
    Serial.println(F("14 − Strong Buzz - 100%"));
  }
  if (effect == 15) {
    Serial.println(F("15 − 750 ms Alert 100%"));
  }
  if (effect == 16) {
    Serial.println(F("16 − 1000 ms Alert 100%"));
  }
  if (effect == 17) {
    Serial.println(F("17 − Strong Click 1 - 100%"));
  }
  if (effect == 18) {
    Serial.println(F("18 − Strong Click 2 - 80%"));
  }
  if (effect == 19) {
    Serial.println(F("19 − Strong Click 3 - 60%"));
  }
  if (effect == 20) {
    Serial.println(F("20 − Strong Click 4 - 30%"));
  }
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
  }

  // set the effect to play
  drv.setWaveform(0, effect);  // play effect 
  drv.setWaveform(1, 0);       // end waveform

  // play the effect!
  drv.go();

  // wait a bit
  delay(500);

  effect++;
  if (effect > 117) effect = 1;

  delay(2000);
  
}
