frankcohen/ReflectionsOS/Devices/Horton/Software/08Compass/08Compass.ino

#include <Adafruit_MMC56x3.h>

/* Assign a unique ID to this sensor at the same time */
Adafruit_MMC5603 mag = Adafruit_MMC5603(12345);

void setup(void) {
  Serial.begin(115200);
  long time = millis();
  while (!Serial && ( millis() < time + 5000) ); // wait up to 5 seconds for Arduino Serial Monitor  
  Serial.setDebugOutput(true);
  Serial.println("Reflections compass research");

  Serial.println("Adafruit_MMC5603 Magnetometer Compass");
  Serial.println("");

  Wire.begin(3,4);

  /* Initialise the sensor */
  if (!mag.begin(MMC56X3_DEFAULT_ADDRESS, &Wire)) {  // I2C mode
    /* There was a problem detecting the MMC5603 ... check your connections */
    Serial.println("Ooops, no MMC5603 detected ... Check your wiring!");
    while (1) delay(10);
  }
}

void loop(void)
{
  /* Get a new sensor event */
  sensors_event_t event;
  mag.getEvent(&event);

  float Pi = 3.14159;

  // Calculate the angle of the vector y,x
  float heading = (atan2(event.magnetic.y,event.magnetic.x) * 180) / Pi;

  // Normalize to 0-360
  if (heading < 0)
  {
    heading = 360 + heading;
  }
  Serial.print("Compass Heading: ");
  Serial.println(heading);
  delay(500);
}
