frankcohen/ReflectionsOS/src/ReflectionsOSdev/SomeTimeLater12pt7b.h

/*
 Reflections, mobile connected entertainment device

 Repository is at https://github.com/frankcohen/ReflectionsOS
 Includes board wiring directions, server side components, examples, support

 Licensed under GPL v3 Open Source Software
 (c) Frank Cohen, All rights reserved. fcohen@starlingwatch.com
 Read the license in the license.txt file that comes with this code.
*/

#ifndef SomeTimeLater12pt7b_h
#define SomeTimeLater12pt7b_h

const uint8_t Some_Time_Later12pt7bBitmaps[] PROGMEM = {
  0x00, 0x78, 0x3C, 0x1E, 0x07, 0x03, 0x80, 0xE0, 0x70, 0x38, 0x0C, 0x06,
  0x01, 0x80, 0xC0, 0x00, 0x18, 0x1C, 0x0E, 0x00, 0x00, 0xDE, 0xF7, 0xBD,
  0x80, 0xF8, 0x73, 0xEF, 0x87, 0x62, 0xFC, 0x76, 0x2F, 0xC7, 0x62, 0x7E,
  0x72, 0x66, 0xF7, 0x3C, 0x6F, 0x70, 0x06, 0x7F, 0x7E, 0x67, 0xF7, 0xE6,
  0x7F, 0x00, 0x63, 0xF0, 0x06, 0x3F, 0x00, 0x61, 0xF0, 0x06, 0x1F, 0x00,
  0x60, 0xF0, 0x06, 0x0F, 0x00, 0x09, 0x07, 0xE1, 0xFE, 0x7F, 0xEF, 0xFD,
  0xFF, 0xB8, 0x76, 0x00, 0x60, 0x07, 0x00, 0x38, 0x00, 0xC0, 0x1D, 0x03,
  0xBF, 0xFF, 0xFE, 0xFF, 0xDF, 0xF0, 0x7C, 0x00, 0x78, 0x02, 0x60, 0xE9,
  0x83, 0xA6, 0x1C, 0xF0, 0xF0, 0x03, 0x80, 0x1C, 0x00, 0xE0, 0x07, 0x00,
  0x18, 0x00, 0xE7, 0x87, 0x19, 0x38, 0x45, 0xE1, 0x97, 0x06, 0x40, 0x0E,
  0x0C, 0x06, 0x03, 0xCF, 0xE6, 0x3B, 0xC4, 0xF0, 0x3C, 0x30, 0x38, 0x3C,
  0x3F, 0xE7, 0xF1, 0xF0, 0x30, 0x18, 0xDB, 0x6C, 0x39, 0xC7, 0x3C, 0xF3,
  0xCF, 0x3C, 0xF3, 0xCF, 0x3C, 0xFB, 0xE7, 0xC6, 0x63, 0xE7, 0xDF, 0x3C,
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
  {   662,  11,  16,  13,    1,  -15 },   // 0x47 'G'
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

const GFXfont Some_Time_Later12pt7b PROGMEM = {
  (uint8_t  *)Some_Time_Later12pt7bBitmaps,
  (GFXglyph *)Some_Time_Later12pt7bGlyphs,
  0x20, 0x7E, 26 };

// Approx. 2330 bytes

#endif // _TOF_
