frankcohen/ReflectionsOS/src/ReflectionsOSdev/SomeTimeLater20pt7b.h

/*
 Reflections, mobile connected entertainment device

 Repository is at https://github.com/frankcohen/ReflectionsOS
 Includes board wiring directions, server side components, examples, support

 Licensed under GPL v3 Open Source Software
 (c) Frank Cohen, All rights reserved. fcohen@starlingwatch.com
 Read the license in the license.txt file that comes with this code.
*/

#ifndef Some_Time_Later20pt7b_h
#define Some_Time_Later20pt7b_h

const uint8_t Some_Time_Later20pt7bBitmaps[] PROGMEM = {
  0x00, 0x0C, 0x07, 0xF0, 0x3F, 0x80, 0xFC, 0x07, 0xE0, 0x3F, 0x00, 0xFC,
  0x07, 0xE0, 0x1F, 0x00, 0xF8, 0x07, 0xC0, 0x1F, 0x00, 0xF8, 0x03, 0xC0,
  0x1E, 0x00, 0x70, 0x03, 0x80, 0x1E, 0x00, 0x70, 0x03, 0x80, 0x08, 0x00,
  0x00, 0x00, 0x00, 0x07, 0x01, 0xF8, 0x07, 0xC0, 0x3E, 0x01, 0xF0, 0x0C,
  0x00, 0x10, 0xFB, 0xFD, 0xEE, 0x77, 0x3B, 0x9D, 0xCE, 0xE7, 0x73, 0x80,
  0xFE, 0x07, 0xE1, 0xFE, 0xFE, 0x07, 0xE3, 0x8F, 0xFF, 0x07, 0xE3, 0x07,
  0xFF, 0x07, 0xE3, 0x07, 0xFF, 0x87, 0xE3, 0x07, 0xFF, 0x87, 0xE3, 0x07,
  0x7F, 0xC7, 0xE3, 0x0F, 0x7F, 0xC7, 0xE3, 0x8E, 0x7B, 0xE7, 0xE3, 0xFE,
  0x7B, 0xE7, 0xE1, 0xFC, 0x7B, 0xE7, 0xE0, 0xF8, 0x79, 0xF7, 0xE0, 0x00,
  0x79, 0xF7, 0xE0, 0x1E, 0x79, 0xFF, 0xE7, 0xFF, 0x78, 0xFF, 0xE7, 0xFF,
  0x78, 0xFF, 0xE0, 0x00, 0x78, 0x7F, 0xE0, 0x00, 0x78, 0x7F, 0xE0, 0x00,
  0x78, 0x7F, 0xE0, 0x00, 0x78, 0x3F, 0xE0, 0x00, 0x78, 0x3F, 0xE0, 0x00,
  0x78, 0x3F, 0xE0, 0x00, 0x78, 0x1F, 0xE0, 0x00, 0x78, 0x1F, 0xE0, 0x00,
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
  {  1866,  15,  28,  17,    1,  -27 },   // 0x46 'F'
  {  1919,  18,  28,  20,    1,  -27 },   // 0x47 'G'
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

const GFXfont Some_Time_Later20pt7b PROGMEM = {
  (uint8_t  *)Some_Time_Later20pt7bBitmaps,
  (GFXglyph *)Some_Time_Later20pt7bGlyphs,
  0x20, 0x7E, 43 };

#endif
