frankcohen/ReflectionsOS/src/ReflectionsOSdev/Minya_Nouvelle_Rg30pt7b.h

/*
 Reflections, mobile connected entertainment device

 Repository is at https://github.com/frankcohen/ReflectionsOS
 Includes board wiring directions, server side components, examples, support

 Licensed under GPL v3 Open Source Software
 (c) Frank Cohen, All rights reserved. fcohen@starlingwatch.com
 Read the license in the license.txt file that comes with this code.
*/

#ifndef MinyaRg30pt7b_h
#define MinyaRg30pt7b_h

const uint8_t Minya_Nouvelle_Rg30pt7bBitmaps[] PROGMEM = {
  0x00, 0x0F, 0x07, 0x83, 0xC1, 0xE0, 0xF0, 0x78, 0x78, 0x3C, 0x1E, 0x0F,
  0x07, 0x83, 0xC1, 0xE0, 0xF0, 0x78, 0x3C, 0x1E, 0x0F, 0x07, 0x83, 0xC1,
  0xE0, 0xF0, 0x78, 0x3C, 0x1E, 0x0F, 0x07, 0x83, 0xC1, 0xE0, 0xF0, 0x00,
  0x00, 0x00, 0x1F, 0x1F, 0xDF, 0xEF, 0xFF, 0xFF, 0xFD, 0xFE, 0x7E, 0x1E,
  0x00, 0xF0, 0x0F, 0x0F, 0xF0, 0xFF, 0x0F, 0xF0, 0xFF, 0x0F, 0xF0, 0xFF,
  0x0F, 0xF0, 0xFF, 0x0F, 0xF0, 0xF7, 0x8F, 0x78, 0xF7, 0x8F, 0x00, 0xE0,
  0x00, 0x38, 0x38, 0x00, 0x1F, 0x1E, 0x00, 0x0F, 0x1F, 0x00, 0x0F, 0x8F,
  0x80, 0x07, 0xC7, 0x80, 0x03, 0xC7, 0xC0, 0x03, 0xE3, 0xE0, 0x01, 0xF1,
  0xF0, 0x00, 0xF8, 0xF0, 0x07, 0xFF, 0xFF, 0xDF, 0xFF, 0xFF, 0xEF, 0xFF,
  0xFF, 0xF7, 0xFF, 0xFF, 0xFB, 0xFF, 0x9F, 0x0C, 0x0F, 0x8F, 0x00, 0x07,
  0x87, 0x80, 0x03, 0xC7, 0xC0, 0x01, 0xE3, 0xC1, 0x81, 0xFF, 0xFF, 0xDF,
  0xFF, 0xFF, 0xEF, 0xFF, 0xFF, 0xF7, 0xFF, 0xFF, 0xFB, 0xFE, 0x3C, 0x00,
  0x1F, 0x1E, 0x00, 0x0F, 0x8F, 0x00, 0x07, 0x87, 0x80, 0x03, 0xC3, 0xC0,
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
  {  3610,  39,  46,  41,    2,  -41 },   // 0x47 'G'
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

const GFXfont Minya_Nouvelle_Rg30pt7b PROGMEM = {
  (uint8_t  *)Minya_Nouvelle_Rg30pt7bBitmaps,
  (GFXglyph *)Minya_Nouvelle_Rg30pt7bGlyphs,
  0x20, 0x7E, 71 };

// Approx. 11871 bytes

#endif
