frankcohen/ReflectionsOS/src/ReflectionsOSdev/Minya16pt7b.h

/*
 Reflections, mobile connected entertainment device

 Repository is at https://github.com/frankcohen/ReflectionsOS
 Includes board wiring directions, server side components, examples, support

 Licensed under GPL v3 Open Source Software
 (c) Frank Cohen, All rights reserved. fcohen@starlingwatch.com
 Read the license in the license.txt file that comes with this code.
*/

#ifndef Minya16pt7b_h
#define Minya16pt7b_h

#include <Arduino_GFX_Library.h>
#include <stdint.h>
#include <pgmspace.h>

const uint8_t Minya16pt7bBitmaps[] PROGMEM = {
  0x00, 0x27, 0x77, 0x77, 0x77, 0x77, 0x77, 0x77, 0x66, 0x20, 0x06, 0xFF,
  0x60, 0x63, 0xF9, 0xFC, 0xFE, 0x7F, 0x3F, 0x9D, 0xCE, 0xE7, 0x71, 0xB0,
  0xC8, 0x00, 0x00, 0xC0, 0x03, 0x00, 0x06, 0x18, 0x1C, 0x20, 0x30, 0xC0,
  0x61, 0x81, 0x87, 0x9F, 0xFF, 0x3E, 0x10, 0x18, 0x23, 0xF0, 0xFF, 0xFF,
  0xF1, 0x86, 0x03, 0x0C, 0x06, 0x38, 0x1C, 0x60, 0x10, 0xC0, 0x03, 0x80,
  0x06, 0x00, 0x00, 0x60, 0x31, 0x80, 0xE6, 0x01, 0x98, 0x07, 0xF8, 0x38,
  0x31, 0x81, 0xCC, 0x07, 0x30, 0x00, 0xE0, 0x01, 0x80, 0x07, 0x00, 0x0E,
  0x00, 0x1C, 0x00, 0x38, 0x00, 0x70, 0x00, 0xE0, 0x01, 0x87, 0x07, 0x38,
  0x0C, 0x40, 0x21, 0x81, 0x03, 0xF8, 0x0D, 0xC0, 0x33, 0x00, 0x80, 0x00,
  0x00, 0x0C, 0x70, 0x76, 0x63, 0x90, 0xCE, 0xC3, 0x73, 0x0D, 0xCE, 0x6E,
  0x1F, 0xB8, 0x3D, 0xC0, 0x06, 0x00, 0x38, 0x01, 0xC0, 0x07, 0x00, 0x38,
  0x00, 0xE0, 0x07, 0x38, 0x19, 0xF0, 0xE6, 0x63, 0x30, 0x9C, 0xC2, 0xE3,
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
  {  1199,  17,  23,  19,    1,  -22 },   // 0x46 'F'
  {  1248,  20,  24,  20,    1,  -23 },   // 0x47 'G'
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

const GFXfont Minya16pt7b PROGMEM = {
  (uint8_t  *)Minya16pt7bBitmaps,
  (GFXglyph *)Minya16pt7bGlyphs,
  0x20, 0x7E, 38 };

// Approx. 4146 bytes

#endif
