frankcohen/ReflectionsOS/src/ReflectionsOSdev/ScienceFair14pt7b.h

/*
 Reflections, mobile connected entertainment device

 Repository is at https://github.com/frankcohen/ReflectionsOS
 Includes board wiring directions, server side components, examples, support

 Licensed under GPL v3 Open Source Software
 (c) Frank Cohen, All rights reserved. fcohen@starlingwatch.com
 Read the license in the license.txt file that comes with this code.
*/

#ifndef ScienceFair14pt_h
#define ScienceFair14pt_h

#include <Arduino_GFX_Library.h>
#include <stdint.h>
#include <pgmspace.h>

const uint8_t ScienceFair14pt7bBitmaps[] PROGMEM = {
  0x00, 0xFF, 0xFF, 0xFF, 0xFF, 0xFF, 0xF8, 0x03, 0xFE, 0xEF, 0xDF, 0xBF,
  0x7E, 0xE0, 0x02, 0x00, 0x01, 0xC7, 0x00, 0xE7, 0x00, 0x63, 0x83, 0xFF,
  0xF9, 0xFF, 0xFC, 0xFF, 0xFC, 0x0C, 0x70, 0x0E, 0x38, 0x3F, 0xFF, 0x1F,
  0xFF, 0x9F, 0xFF, 0xC1, 0xC7, 0x00, 0xE7, 0x00, 0x63, 0x80, 0x00, 0x00,
  0x07, 0x00, 0x38, 0x01, 0xC0, 0x7F, 0xC7, 0xFF, 0x7F, 0xFF, 0x9C, 0xFC,
  0xE7, 0xE7, 0x3F, 0x38, 0x39, 0xC1, 0xCE, 0x0F, 0xFE, 0x3F, 0xF8, 0xFF,
  0xE0, 0xE7, 0x07, 0x38, 0x39, 0xF9, 0xCF, 0xCE, 0x7E, 0x73, 0xFF, 0xFD,
  0xFF, 0xC7, 0xFC, 0x07, 0x00, 0x38, 0x00, 0x00, 0x02, 0x00, 0x03, 0xC0,
  0xE0, 0x03, 0xFC, 0x38, 0x01, 0xFF, 0x9C, 0x00, 0xF0, 0xE7, 0x00, 0x38,
  0x1D, 0xC0, 0x0E, 0x07, 0x70, 0x03, 0x81, 0xF8, 0x00, 0xE0, 0x7E, 0x00,
  0x3C, 0x3B, 0x80, 0x07, 0xFE, 0xE3, 0xC0, 0xFF, 0x33, 0xFC, 0x1F, 0x1D,
  0xFF, 0x80, 0x07, 0x70, 0xE0, 0x01, 0xF8, 0x1C, 0x00, 0x6E, 0x07, 0x00,
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
  {   980,  10,  21,  12,    1,  -20 },   // 0x46 'F'
  {  1007,  12,  21,  14,    1,  -20 },   // 0x47 'G'
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

const GFXfont ScienceFair14pt7b PROGMEM = {
  (uint8_t  *)ScienceFair14pt7bBitmaps,
  (GFXglyph *)ScienceFair14pt7bGlyphs,
  0x20, 0x7E, 34 };

// Approx. 3401 bytes


#endif
