frankcohen/ReflectionsOS/ShowRunner/tjpgdClass.cpp

/*----------------------------------------------------------------------------/
/ TJpgDec - Tiny JPEG Decompressor R0.01c                     (C)ChaN, 2019
/-----------------------------------------------------------------------------/
/ The TJpgDec is a generic JPEG decompressor module for tiny embedded systems.
/ This is a free software that opened for education, research and commercial
/  developments under license policy of following terms.
/
/  Copyright (C) 2019, ChaN, all right reserved.
/
/ * The TJpgDec module is a free software and there is NO WARRANTY.
/ * No restriction on use. You can use, modify and redistribute it for
/   personal, non-profit or commercial products UNDER YOUR RESPONSIBILITY.
/ * Redistributions of source code must retain the above copyright notice.
/
/-----------------------------------------------------------------------------/
/ Oct 04, 2011 R0.01  First release.
/ Feb 19, 2012 R0.01a Fixed decompression fails when scan starts with an escape seq.
/ Sep 03, 2012 R0.01b Added JD_TBLCLIP option.
/ Mar 16, 2019 R0.01c Supprted stdint.h.
/----------------------------------------------------------------------------/
/ May 2019 ～ July 2020  Tweak for ESP32 ( modify by lovyan03 )
/----------------------------------------------------------------------------*/

#pragma GCC optimize ("O3")

#include "tjpgdClass.h"

#include <string.h> // for memcpy memset
#include <freertos/FreeRTOS.h>
#include <freertos/task.h>
#include <freertos/queue.h>


/*-----------------------------------------------*/
/* Zigzag-order to raster-order conversion table */
/*-----------------------------------------------*/

#define ZIG(n)	Zig[n]

static const uint8_t Zig[64] = {	/* Zigzag-order to raster-order conversion table */
	 0,  1,  8, 16,  9,  2,  3, 10, 17, 24, 32, 25, 18, 11,  4,  5,
	12, 19, 26, 33, 40, 48, 41, 34, 27, 20, 13,  6,  7, 14, 21, 28,
	35, 42, 49, 56, 57, 50, 43, 36, 29, 22, 15, 23, 30, 37, 44, 51,
	58, 59, 52, 45, 38, 31, 39, 46, 53, 60, 61, 54, 47, 55, 62, 63
};



/*-------------------------------------------------*/
/* Input scale factor of Arai algorithm            */
/* (scaled up 16 bits for fixed point operations)  */
/*-------------------------------------------------*/

#define IPSF(n)	Ipsf[n]

static const uint16_t Ipsf[64] = {	/* See also aa_idct.png */
	(uint16_t)(1.00000*8192), (uint16_t)(1.38704*8192), (uint16_t)(1.30656*8192), (uint16_t)(1.17588*8192), (uint16_t)(1.00000*8192), (uint16_t)(0.78570*8192), (uint16_t)(0.54120*8192), (uint16_t)(0.27590*8192),
	(uint16_t)(1.38704*8192), (uint16_t)(1.92388*8192), (uint16_t)(1.81226*8192), (uint16_t)(1.63099*8192), (uint16_t)(1.38704*8192), (uint16_t)(1.08979*8192), (uint16_t)(0.75066*8192), (uint16_t)(0.38268*8192),
	(uint16_t)(1.30656*8192), (uint16_t)(1.81226*8192), (uint16_t)(1.70711*8192), (uint16_t)(1.53636*8192), (uint16_t)(1.30656*8192), (uint16_t)(1.02656*8192), (uint16_t)(0.70711*8192), (uint16_t)(0.36048*8192),
	(uint16_t)(1.17588*8192), (uint16_t)(1.63099*8192), (uint16_t)(1.53636*8192), (uint16_t)(1.38268*8192), (uint16_t)(1.17588*8192), (uint16_t)(0.92388*8192), (uint16_t)(0.63638*8192), (uint16_t)(0.32442*8192),
	(uint16_t)(1.00000*8192), (uint16_t)(1.38704*8192), (uint16_t)(1.30656*8192), (uint16_t)(1.17588*8192), (uint16_t)(1.00000*8192), (uint16_t)(0.78570*8192), (uint16_t)(0.54120*8192), (uint16_t)(0.27590*8192),
	(uint16_t)(0.78570*8192), (uint16_t)(1.08979*8192), (uint16_t)(1.02656*8192), (uint16_t)(0.92388*8192), (uint16_t)(0.78570*8192), (uint16_t)(0.61732*8192), (uint16_t)(0.42522*8192), (uint16_t)(0.21677*8192),
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
	0, 0, 0, 0, 0, 0, 0, 0, 0, 0, 0, 0, 0, 0, 0, 0, 0, 0, 0, 0, 0, 0, 0, 0, 0, 0, 0, 0, 0, 0, 0, 0,
	0, 0, 0, 0, 0, 0, 0, 0, 0, 0, 0, 0, 0, 0, 0, 0, 0, 0, 0, 0, 0, 0, 0, 0, 0, 0, 0, 0, 0, 0, 0, 0,
	0, 0, 0, 0, 0, 0, 0, 0, 0, 0, 0, 0, 0, 0, 0, 0, 0, 0, 0, 0, 0, 0, 0, 0, 0, 0, 0, 0, 0, 0, 0, 0,
	0, 0, 0, 0, 0, 0, 0, 0, 0, 0, 0, 0, 0, 0, 0, 0, 0, 0, 0, 0, 0, 0, 0, 0, 0, 0, 0, 0, 0, 0, 0, 0,
	0, 0, 0, 0, 0, 0, 0, 0, 0, 0, 0, 0, 0, 0, 0, 0, 0, 0, 0, 0, 0, 0, 0, 0, 0, 0, 0, 0, 0, 0, 0, 0,
	0, 0, 0, 0, 0, 0, 0, 0, 0, 0, 0, 0, 0, 0, 0, 0, 0, 0, 0, 0, 0, 0, 0, 0, 0, 0, 0, 0, 0, 0, 0, 0,
	0, 0, 0, 0, 0, 0, 0, 0, 0, 0, 0, 0, 0, 0, 0, 0, 0, 0, 0, 0, 0, 0, 0, 0, 0, 0, 0, 0, 0, 0, 0, 0,
	/* -256..-1 */
	0, 0, 0, 0, 0, 0, 0, 0, 0, 0, 0, 0, 0, 0, 0, 0, 0, 0, 0, 0, 0, 0, 0, 0, 0, 0, 0, 0, 0, 0, 0, 0,
	0, 0, 0, 0, 0, 0, 0, 0, 0, 0, 0, 0, 0, 0, 0, 0, 0, 0, 0, 0, 0, 0, 0, 0, 0, 0, 0, 0, 0, 0, 0, 0,
	0, 0, 0, 0, 0, 0, 0, 0, 0, 0, 0, 0, 0, 0, 0, 0, 0, 0, 0, 0, 0, 0, 0, 0, 0, 0, 0, 0, 0, 0, 0, 0,
	0, 0, 0, 0, 0, 0, 0, 0, 0, 0, 0, 0, 0, 0, 0, 0, 0, 0, 0, 0, 0, 0, 0, 0, 0, 0, 0, 0, 0, 0, 0, 0,
	0, 0, 0, 0, 0, 0, 0, 0, 0, 0, 0, 0, 0, 0, 0, 0, 0, 0, 0, 0, 0, 0, 0, 0, 0, 0, 0, 0, 0, 0, 0, 0,
	0, 0, 0, 0, 0, 0, 0, 0, 0, 0, 0, 0, 0, 0, 0, 0, 0, 0, 0, 0, 0, 0, 0, 0, 0, 0, 0, 0, 0, 0, 0, 0,
	0, 0, 0, 0, 0, 0, 0, 0, 0, 0, 0, 0, 0, 0, 0, 0, 0, 0, 0, 0, 0, 0, 0, 0, 0, 0, 0, 0, 0, 0, 0, 0,
	0, 0, 0, 0, 0, 0, 0, 0, 0, 0, 0, 0, 0, 0, 0, 0, 0, 0, 0, 0, 0, 0, 0, 0, 0, 0, 0, 0, 0, 0, 0, 0
};

#else	/* JD_TBLCLIP */

inline uint_fast8_t BYTECLIP (
	int32_t val
)
{
	if (val < 0) val = 0;
	else if (val > 255) val = 255;

	return val;
}

#endif


/*-----------------------------------------------------------------------*/
/* Allocate a memory block from memory pool                              */
/*-----------------------------------------------------------------------*/

static void* alloc_pool (	/* Pointer to allocated memory block (NULL:no memory available) */
	TJpgD* jd,		/* Pointer to the decompressor object */
	uint_fast16_t nd		/* Number of bytes to allocate */
)
{
	char *rp = 0;


	nd = (nd + 3) & ~3;			/* Align block size to the word boundary */

	if (jd->sz_pool >= nd) {
		jd->sz_pool -= nd;
		rp = (char*)jd->pool;			/* Get start of available memory pool */
		jd->pool = (void*)(rp + nd);	/* Allocate requierd bytes */
	}

	return (void*)rp;	/* Return allocated memory block (NULL:no memory to allocate) */
}




/*-----------------------------------------------------------------------*/
/* Create de-quantization and prescaling tables with a DQT segment       */
/*-----------------------------------------------------------------------*/

static int create_qt_tbl (	/* 0:OK, !0:Failed */
	TJpgD* jd,				/* Pointer to the decompressor object */
	const uint8_t* data,	/* Pointer to the quantizer tables */
	uint_fast16_t ndata			/* Size of input data */
)
{
	uint_fast8_t d, z;
	int32_t *pb;

	do {	/* Process all tables in the segment */
		d = *data++;							/* Get table property */
		if (d & 0xF0) return TJpgD::JDR_FMT1;			/* Err: not 8-bit resolution */
		pb = (int32_t*)alloc_pool(jd, 64 * sizeof (int32_t));/* Allocate a memory block for the table */
		if (!pb) return TJpgD::JDR_MEM1;				/* Err: not enough memory */
		jd->qttbl[d & 3] = pb;						/* Register the table */
		for (size_t i = 0; i < 64; ++i) {			/* Load the table */
			z = ZIG(i);							/* Zigzag-order to raster-order conversion */
			pb[z] = (int32_t)((uint32_t)data[i] * IPSF(z));	/* Apply scale factor of Arai algorithm to the de-quantizers */
		}
		data += 64;
	} while (ndata -= 65);

	return TJpgD::JDR_OK;
}




/*-----------------------------------------------------------------------*/
/* Create huffman code tables with a DHT segment                         */
/*-----------------------------------------------------------------------*/

static int create_huffman_tbl (	/* 0:OK, !0:Failed */
	TJpgD* jd,					/* Pointer to the decompressor object */
	const uint8_t* data,		/* Pointer to the packed huffman tables */
	uint_fast16_t ndata				/* Size of input data */
)
{
	uint_fast16_t d, b, np, cls, num, hc;
	uint8_t *pb, *pd;
	uint_fast16_t *ph;


	do {	/* Process all tables in the segment */
		d = *data++;						/* Get table number and class */
		if (d & 0xEE) return TJpgD::JDR_FMT1;		/* Err: invalid class/number */
		cls = d >> 4; num = d & 0x0F;		/* class = dc(0)/ac(1), table number = 0/1 */
		pb = (uint8_t*)alloc_pool(jd, 16);			/* Allocate a memory block for the bit distribution table */
		if (!pb) return TJpgD::JDR_MEM1;			/* Err: not enough memory */
		jd->huffbits[num][cls] = pb - 1;
		np = 0;
		for (size_t i = 0; i < 16; ++i) {		/* Load number of patterns for 1 to 16-bit code */
			np += (pb[i] = data[i]);		/* Get sum of code words for each code */
		}

		ph = (uint_fast16_t*)alloc_pool(jd, (np * sizeof (uint_fast16_t)));/* Allocate a memory block for the code word table */
		if (!ph) return TJpgD::JDR_MEM1;			/* Err: not enough memory */
		jd->huffcode[num][cls] = ph - 1;
		hc = 0;
		for (size_t i = 0; i < 16; ++i) {		/* Re-build huffman code word table */
			b = pb[i];
			while (b--) *ph++ = hc++;
			hc <<= 1;
		}

		pd = (uint8_t*)alloc_pool(jd, np);			/* Allocate a memory block for the decoded data */
		if (!pd) return TJpgD::JDR_MEM1;			/* Err: not enough memory */
		jd->huffdata[num][cls] = pd - 1;

		memcpy(pd, data += 16, np);		/* Load decoded data corresponds to each code ward */
		data += np;
	} while (ndata -= 17 + np);

	return TJpgD::JDR_OK;
}




/*-----------------------------------------------------------------------*/
/* Extract N bits from input stream                                      */
/*-----------------------------------------------------------------------*/

static inline int_fast16_t bitext (	/* >=0: extracted data, <0: error code */
	TJpgD* jd,		/* Pointer to the decompressor object */
	int_fast16_t nbit		/* Number of bits to extract (1 to 11) */
)
{
	uint8_t *dp = jd->dptr;	/* Bit mask, number of data available, read ptr */
	uint_fast8_t s = *dp;
	uint_fast8_t msk = jd->dmsk;
	uint_fast16_t v = 0;

	if (msk) {
		if (msk >= nbit) {
			msk -= nbit;
			jd->dmsk = msk;
			return (s >> msk) & ((1 << nbit) - 1);	/* Get bits */
		}
		nbit -= msk;
		v = (s & ((1 << msk) - 1)) << nbit;	/* Get bits */
	}

	uint8_t *dpend = jd->dpend;

	for (;;) {
		if (++dp == dpend) {			/* No input data is available, re-fill input buffer */
			dp = jd->inbuf;	/* Top of input buffer */
			jd->dpend = dpend = dp + jd->infunc(jd, dp, TJPGD_SZBUF);
			if (dp == dpend) return 0 - (int_fast16_t)TJpgD::JDR_INP;	/* Err: read error or wrong stream termination */
		}
		s = *dp;				/* Get next data byte */
		if (s == 0xFF) {		/* Is start of flag sequence? */
			if (++dp == dpend) {			/* No input data is available, re-fill input buffer */
				dp = jd->inbuf;	/* Top of input buffer */
				jd->dpend = dpend = dp + jd->infunc(jd, dp, TJPGD_SZBUF);
				if (dp == dpend) return 0 - (int_fast16_t)TJpgD::JDR_INP;	/* Err: read error or wrong stream termination */
			}
			if (*dp != 0) return 0 - (int_fast16_t)TJpgD::JDR_FMT1;	/* Err: unexpected flag is detected (may be collapted data) */
			*dp = s;			/* The flag is a data 0xFF */
		}
		if (8 >= nbit) {
			msk = 8 - nbit;
			jd->dmsk = msk; jd->dptr = dp;
			return v + ((s >> msk) & ((1 << nbit) - 1));	/* Get bits */
		}
		nbit -= 8;
		v |= s << nbit;	/* Get bits */
	}
}




/*-----------------------------------------------------------------------*/
/* Extract a huffman decoded data from input stream                      */
/*-----------------------------------------------------------------------*/

static int_fast16_t huffext (	/* >=0: decoded data, <0: error code */
	TJpgD* jd,				/* Pointer to the decompressor object */
	const uint8_t* hbits,	/* Pointer to the bit distribution table */
	const uint_fast16_t* hcode,	/* Pointer to the code word table */
	const uint8_t* hdata	/* Pointer to the data table */
)
{
	uint_fast8_t msk = jd->dmsk;
	uint8_t *dpend = jd->dpend;	/* Bit mask, number of data available, read ptr */
	uint8_t *dp = jd->dptr;
	uint_fast8_t s = *dp;
	uint_fast8_t v = 0;
	uint_fast8_t bl = 16;	/* Max code length */

	for (;;) {
		if (!msk) {				/* Next byte? */
			msk = 8;			/* Read from MSB */
			if (++dp == dpend) {			/* No input data is available, re-fill input buffer */
				dp = jd->inbuf;	/* Top of input buffer */
				jd->dpend = dpend = dp + jd->infunc(jd, dp, TJPGD_SZBUF);
				if (dp == dpend) return 0 - (int_fast16_t)TJpgD::JDR_INP;	/* Err: read error or wrong stream termination */
			}
			s = *dp;				/* Get next data byte */
			if (s == 0xFF) {		/* Is start of flag sequence? */
				if (++dp == dpend) {			/* No input data is available, re-fill input buffer */
					dp = jd->inbuf;	/* Top of input buffer */
					jd->dpend = dpend = dp + jd->infunc(jd, dp, TJPGD_SZBUF);
					if (dp == dpend) return 0 - (int_fast16_t)TJpgD::JDR_INP;	/* Err: read error or wrong stream termination */
				}
				if (*dp != 0) return 0 - (int_fast16_t)TJpgD::JDR_FMT1;	/* Err: unexpected flag is detected (may be collapted data) */
				*dp = s;			/* The flag is a data 0xFF */
			}
		}
		do {
			v = (v << 1) + ((s >> (--msk)) & 1);	/* Get a bit */
			uint_fast8_t nd = *++hbits;
			if (nd) {
				do {
					++hdata;
					if (v == *++hcode) goto huffext_match;	/* Matched? */
				} while (--nd);	/* Search the code word in this bit length */
			}
			if (!--bl) return 0 - (int_fast16_t)TJpgD::JDR_FMT1;	/* Err: code not found (may be collapted data) */
		} while (msk);
	}
huffext_match:
	jd->dmsk = msk;
	jd->dptr = dp;
	return *hdata;					/* Return the decoded data */
}

/*-----------------------------------------------------------------------*/
/* Apply Inverse-DCT in Arai Algorithm (see also aa_idct.png)            */
/*-----------------------------------------------------------------------*/

static void block_idct (
	int32_t* src,	/* Input block data (de-quantized and pre-scaled for Arai Algorithm) */
	uint8_t* dst	/* Pointer to the destination to store the block as byte array */
)
{
	const int32_t M13 = (int32_t)(1.41421*256), M4 = (int32_t)(2.61313*256);
	const float F2 = 1.08239, F5 = 1.84776;

	int32_t v0, v1, v2, v3, v4, v5, v6, v7;
	int32_t t10, t11, t12, t13;

	/* Process columns */
	for (size_t i = 0; i < 8; ++i) {
		/* Get and Process the even elements */
		t12 = src[8 * 0];
		t10 = src[8 * 4];
		t10 += t12;
		t12 = (t12 << 1) - t10;

		t11 = src[8 * 2];
		t13 = src[8 * 6];
		t13 += t11;
		t11 = (t11 << 1) - t13;
		t11 = t11 * M13 >> 8;
		t11 = t11 - t13;

		v0 = t10 + t13;
		v3 = t10 - t13;
		v1 = t12 + t11;
		v2 = t12 - t11;

		/* Get and Process the odd elements */
		v4 = src[8 * 1];
		v5 = src[8 * 7];
		v5 += v4;
		v4 = (v4 << 1) - v5;

		v7 = src[8 * 3];
		v6 = src[8 * 5];
		v6 -= v7;
		v7 = (v7 << 1) + v6;
		v7 += v5;

		t13 = v4 + v6;
		t13 *= F5;
		v6 = v6 * M4 >> 8;
		v6 += v7;
		v6 = t13 - v6;
		v5 = (v5 << 1) - v7;
		v5 = v5 * M13 >> 8;
		v5 -= v6;
		v4 *= F2;
		v4 += v5;
		v4 = t13 - v4;

		/* Write-back transformed values */
		src[8 * 0] = v0 + v7;
		src[8 * 7] = v0 - v7;
		src[8 * 1] = v1 + v6;
		src[8 * 6] = v1 - v6;
		src[8 * 2] = v2 + v5;
		src[8 * 5] = v2 - v5;
		src[8 * 3] = v3 + v4;
		src[8 * 4] = v3 - v4;

		++src;	/* Next column */
	}

	/* Process rows */
	src -= 8;
	for (size_t i = 0; i < 8; ++i) {
		/* Get and Process the even elements */
		t12 = src[0] + (128L << 8);	/* remove DC offset (-128) here */
		t10 = src[4];
		t10 += t12;
		t12 = (t12 << 1) - t10;

		t11 = src[2];
		t13 = src[6];
		t13 += t11;
		t11 = (t11 << 1) - t13;
		t11 = t11 * M13 >> 8;
		t11 -= t13;

		v0 = t10 + t13;
		v3 = t10 - t13;
		v1 = t12 + t11;
		v2 = t12 - t11;

		/* Get and Process the odd elements */
		v4 = src[1];
		v5 = src[7];
		v5 += v4;
		v4 = (v4 << 1) - v5;

		v7 = src[3];
		v6 = src[5];
		v6 -= v7;
		v7 = (v7 << 1) + v6;
		v7 += v5;

		t13 = v4 + v6;
		t13 *= F5;
		v6 = v6 * M4 >> 8;
		v6 += v7;
		v6 = t13 - v6;
		v5 = (v5 << 1) - v7;
		v5 = v5 * M13 >> 8;
		v5 -= v6;
		v4 *= F2;
		v4 += v5;
		v4 = t13 - v4;

		/* Descale the transformed values 8 bits and output */
		dst[0] = BYTECLIP((v0 + v7) >> 8);
		dst[7] = BYTECLIP((v0 - v7) >> 8);
		dst[1] = BYTECLIP((v1 + v6) >> 8);
		dst[6] = BYTECLIP((v1 - v6) >> 8);
		dst[2] = BYTECLIP((v2 + v5) >> 8);
		dst[5] = BYTECLIP((v2 - v5) >> 8);
		dst[3] = BYTECLIP((v3 + v4) >> 8);
		dst[4] = BYTECLIP((v3 - v4) >> 8);

		dst += 8;
		src += 8;	/* Next row */
	}
}




/*-----------------------------------------------------------------------*/
/* Load all blocks in the MCU into working buffer                        */
/*-----------------------------------------------------------------------*/

static TJpgD::JRESULT mcu_load (
	TJpgD* jd,		/* Pointer to the decompressor object */
	uint8_t* bp,		/* mcubuf */
	int32_t* tmp	/* Block working buffer for de-quantize and IDCT */
)
{
	int_fast16_t b, d, e;
	uint_fast8_t blk, nby, nbc, i, z;
	const uint8_t *hb, *hd;
	const uint_fast16_t *hc;

	nby = jd->msx * jd->msy;	/* Number of Y blocks (1, 2 or 4) */
	nbc = 2;					/* Number of C blocks (2) */

	for (blk = 0; blk < nby + nbc; blk++) {
		uint_fast8_t cmp = (blk < nby) ? 0 : blk - nby + 1;	/* Component number 0:Y, 1:Cb, 2:Cr */
		uint_fast8_t id = cmp ? 1 : 0;						/* Huffman table ID of the component */

		/* Extract a DC element from input stream */
		hb = jd->huffbits[id][0];				/* Huffman table for the DC element */
		hc = jd->huffcode[id][0];
		hd = jd->huffdata[id][0];
		b = huffext(jd, hb, hc, hd);			/* Extract a huffman coded data (bit length) */
		if (b < 0) return (TJpgD::JRESULT)(-b);		/* Err: invalid code or input */
		d = jd->dcv[cmp];						/* DC value of previous block */
		if (b) {								/* If there is any difference from previous block */
			e = bitext(jd, b);					/* Extract data bits */
			if (e < 0) return (TJpgD::JRESULT)(-e);	/* Err: input */
			b = 1 << (b - 1);					/* MSB position */
			if (!(e & b)) e -= (b << 1) - 1;	/* Restore sign if needed */
			d += e;								/* Get current value */
			jd->dcv[cmp] = d;			/* Save current DC value for next block */
		}
		const int32_t *dqf = jd->qttbl[jd->qtid[cmp]];			/* De-quantizer table ID for this component */
		tmp[0] = d * dqf[0] >> 8;				/* De-quantize, apply scale factor of Arai algorithm and descale 8 bits */

		/* Extract following 63 AC elements from input stream */
		memset(&tmp[1], 0, 4 * 63);				/* Clear rest of elements */
		hb = jd->huffbits[id][1];				/* Huffman table for the AC elements */
		hc = jd->huffcode[id][1];
		hd = jd->huffdata[id][1];
		i = 1;					/* Top of the AC elements */
		do {
			b = huffext(jd, hb, hc, hd);		/* Extract a huffman coded value (zero runs and bit length) */
			if (b == 0) break;					/* EOB? */
			if (b < 0) return (TJpgD::JRESULT)(-b);	/* Err: invalid code or input error */
			i += b >> 4;
			if (b &= 0x0F) {					/* Bit length */
				d = bitext(jd, b);				/* Extract data bits */
				if (d < 0) return (TJpgD::JRESULT)(-d);/* Err: input device */
				b = 1 << (b - 1);				/* MSB position */
				if (!(d & b)) d -= (b << 1) - 1;/* Restore negative value if needed */
				z = ZIG(i);						/* Zigzag-order to raster-order converted index */
				tmp[z] = d * dqf[z] >> 8;		/* De-quantize, apply scale factor of Arai algorithm and descale 8 bits */
			}
		} while (++i != 64);		/* Next AC element */

		block_idct(tmp, bp);		/* Apply IDCT and store the block to the MCU buffer */

		bp += 64;				/* Next block */
	}

	return TJpgD::JDR_OK;	/* All blocks have been loaded successfully */
}




/*-----------------------------------------------------------------------*/
/* Output an MCU: Convert YCrCb to RGB and output it in RGB form         */
/*-----------------------------------------------------------------------*/
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
